sonydevworld/spresense-hw-design-files/GNSS/SPRESENSE_GNSS_antenna_char_en.pdf

## The characteristics of GNSS antenna

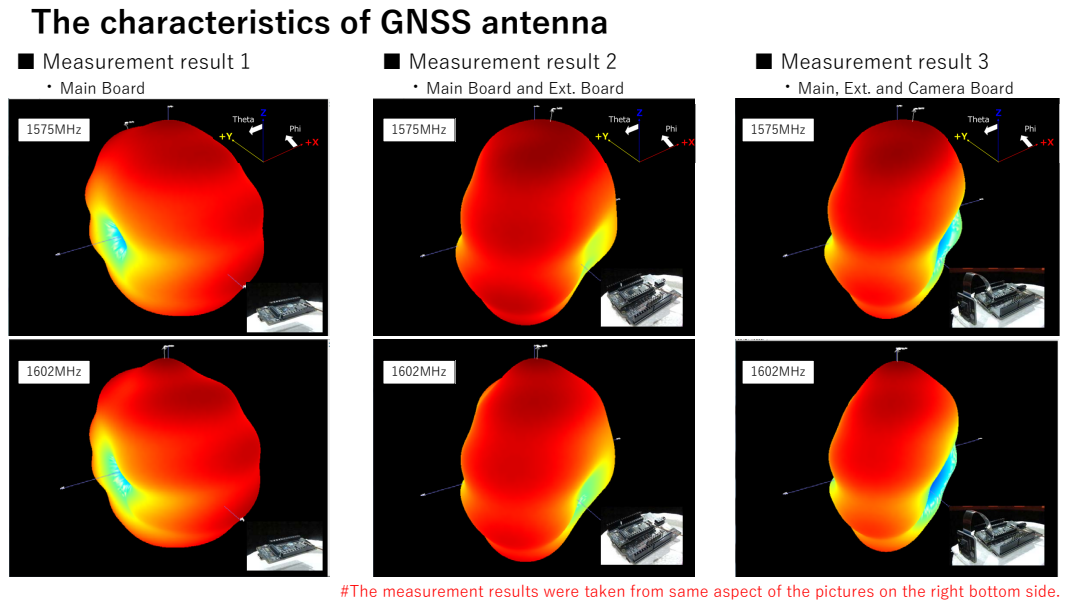
[picture p5: page 1]
1602MHz; 1575MHz; ■ Measurement result 1 ・Main Board

■ Measurement result 2
・Main Board and Ext. Board

■ Measurement result 3
・Main, Ext. and Camera Board

#The measurement results were taken from same aspect of the pictures on the right bottom side.

## Total gain in two-dimensional plane （Main board）

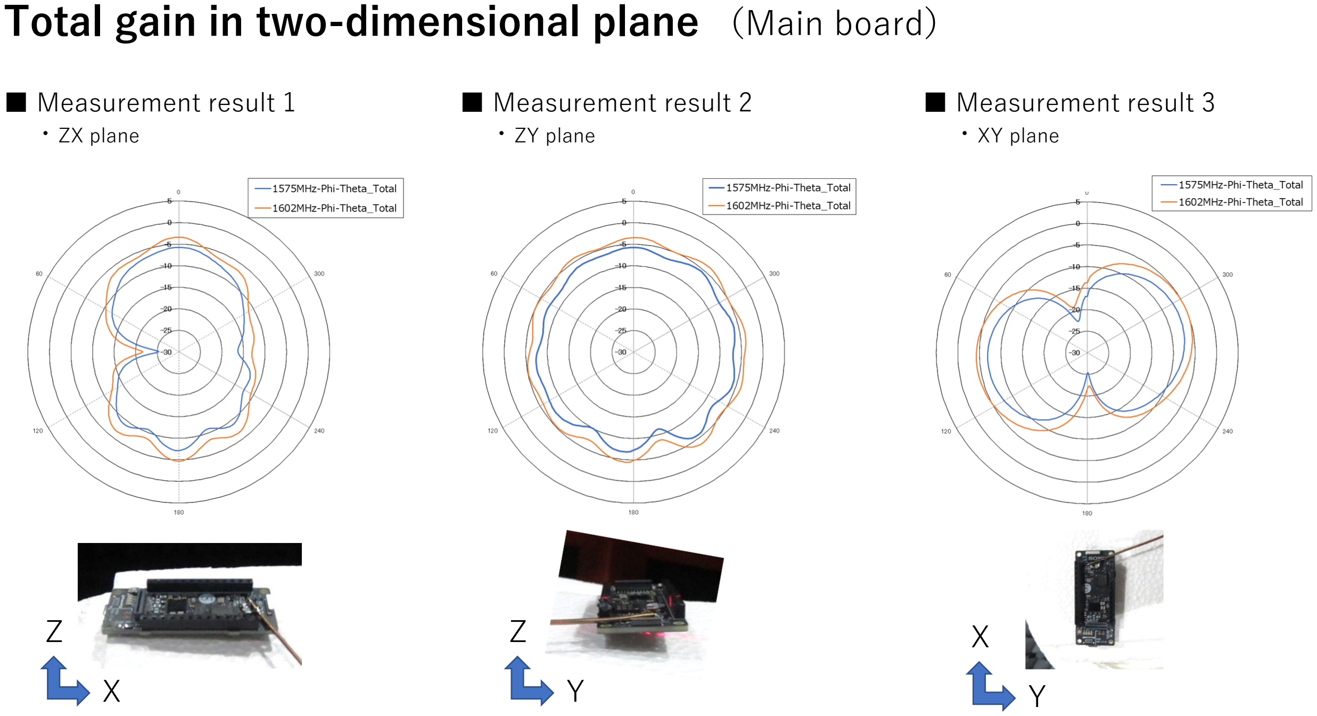
[picture p6: page 2]

■ Measurement result 1
・ZX plane

■ Measurement result 2
・ZY plane

■ Measurement result 3
・XY plane

X

Z

Y

Z

Y

X

## Total gain in two-dimensional plane （ Main board ＋Ext board）

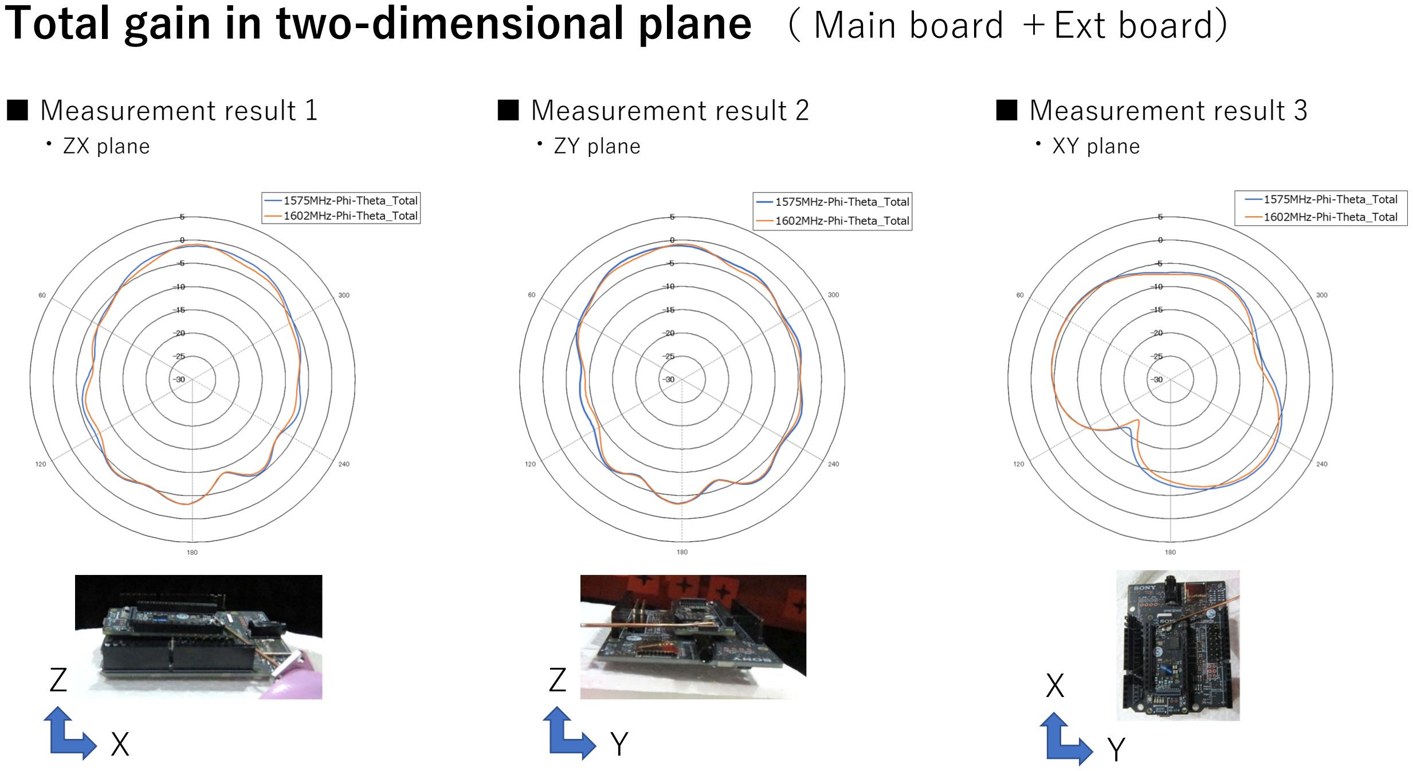
[picture p7: page 3]

X

Z

Y

Z

Y

X

■ Measurement result 1
・ZX plane

■ Measurement result 2
・ZY plane

■ Measurement result 3
・XY plane

## Total gain in two-dimensional plane （ Main＋Ext + Camera board）

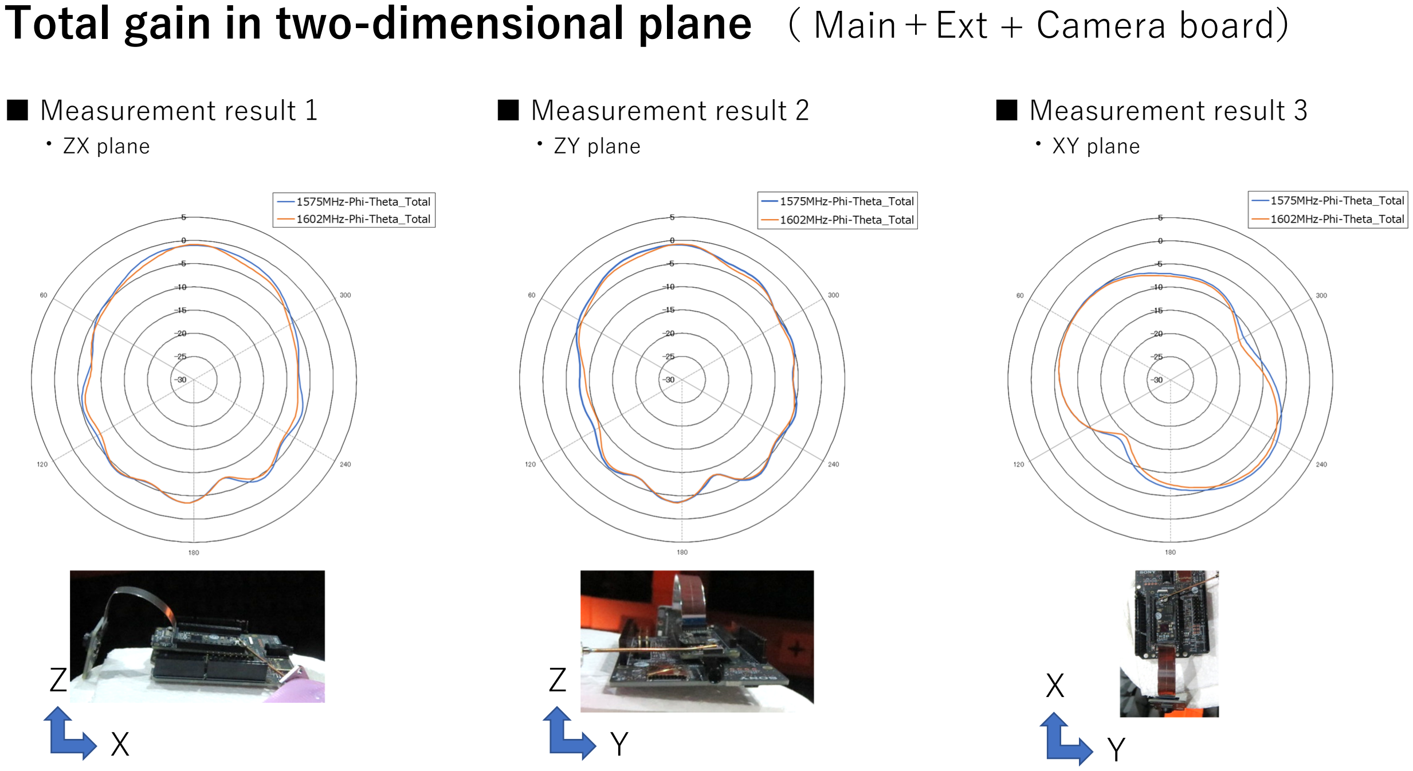
[picture p8: page 4]

X

Z

Y

Z

Y

X

■ Measurement result 1
・ZX plane

■ Measurement result 2
・ZY plane

■ Measurement result 3
・XY plane

Main Board
| 1575MHz | 1602MHz
Gain | Peak | Average of upper hemisphere(+Z) | Overall average | Peak | Average of upper hemisphere(+Z) | Overall average
[dBic] | -5.6 | -7.9 | -8.4 | -3.4 | -5.9 | -6.2
| 1575MHz | 1602MHz
Gain | Peak | Average of upper hemisphere(+Z) | Overall average | Peak | Average of upper hemisphere(+Z) | Overall average
[dBic] | -0.9 | -3.6 | -4.4 | -0.9 | -4.0 | -4.9
| 1575MHz | 1602MHz
Gain | Peak | Average of upper hemisphere(+Z) | Overall average | Peak | Average of upper hemisphere(+Z) | Overall average
[dBic] | -1.2 | -3.6 | -4.2 | -0.9 | -4.0 | -4.6

Main Board and Ext. Board

Main, Ext. and Camera Board

## The gain values of the antenna
