sonydevworld/spresense-hw-design-files/GNSS/SPRESENSE_GNSS_antenna_char_ja.pdf

## GNSSアンテナ特性

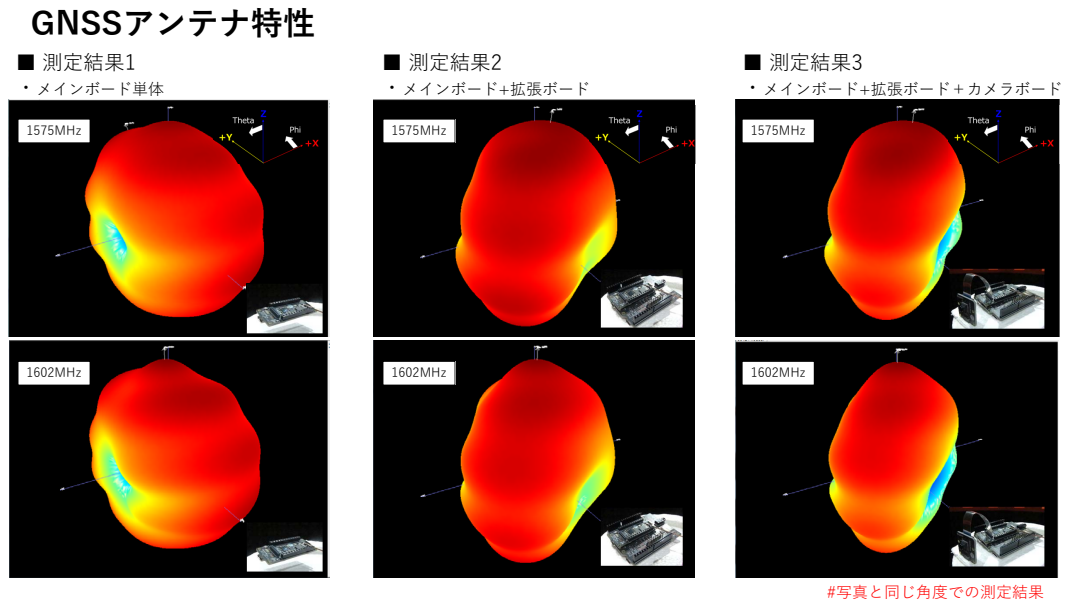
[picture p9: page 1]
#写真と同じ⾓度での測定結果; 1602MHz; 1575MHz; ■ 測定結果1 ・メインボード単体; ■ 測定結果2 ・メインボード+拡張ボード

■ 測定結果3
・メインボード+拡張ボード＋カメラボード

## 2D放射パターン Total Gain （メインボード単体）

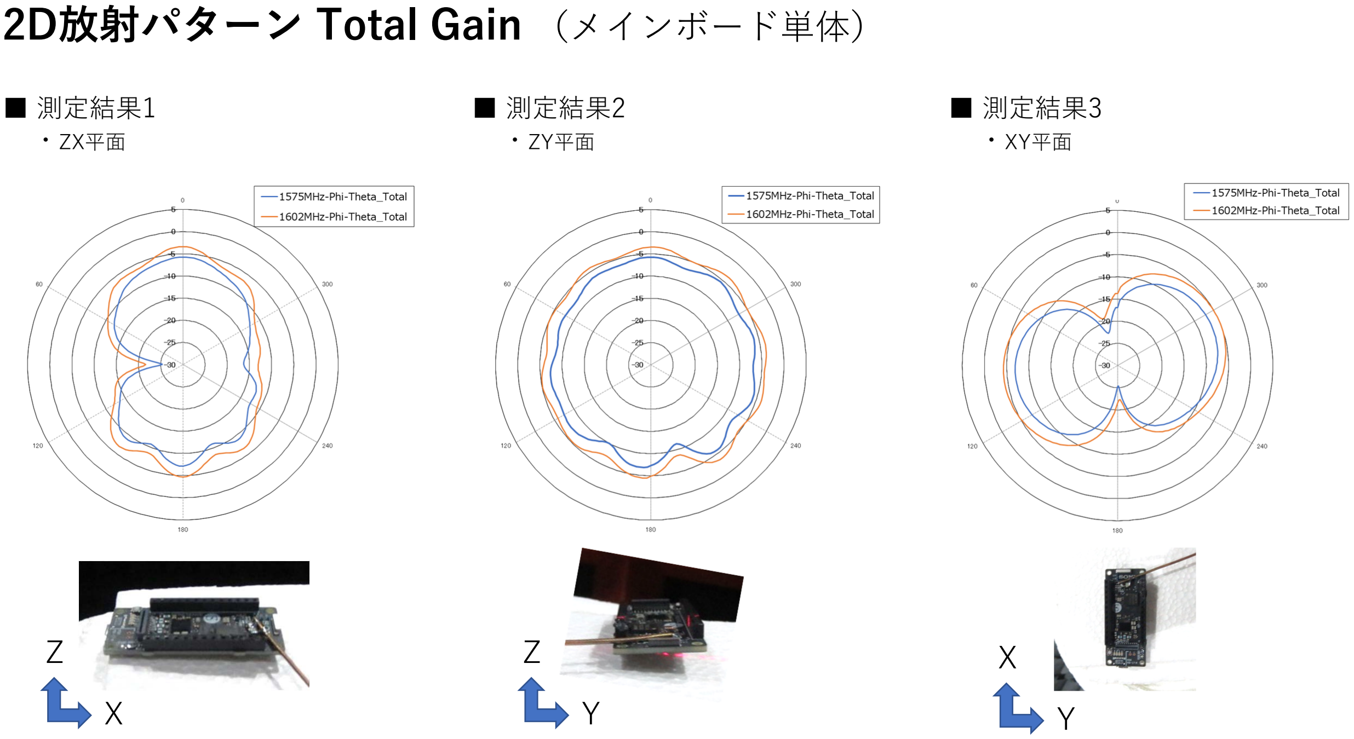
[picture p10: page 2]

■ 測定結果1
・ZX平⾯

■ 測定結果2
・ZY平⾯

■ 測定結果3
・XY平⾯

X

Z

Y

Z

Y

X

## 2D放射パターン Total Gain （メインボード＋拡張ボード）

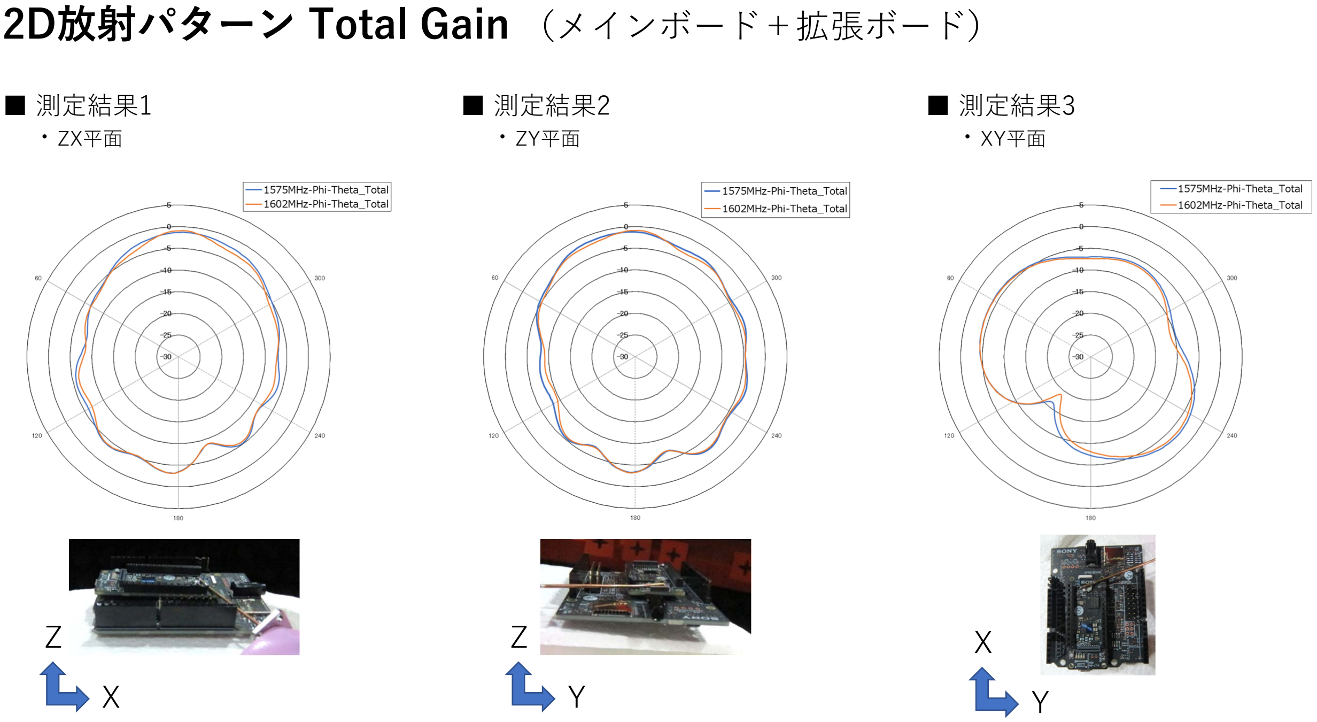
[picture p11: page 3]

■ 測定結果1
・ZX平⾯

■ 測定結果2
・ZY平⾯

■ 測定結果3
・XY平⾯

X

Z

Y

Z

Y

X

## 2D放射パターン Total Gain （メイン＋拡張＋カメラボード）

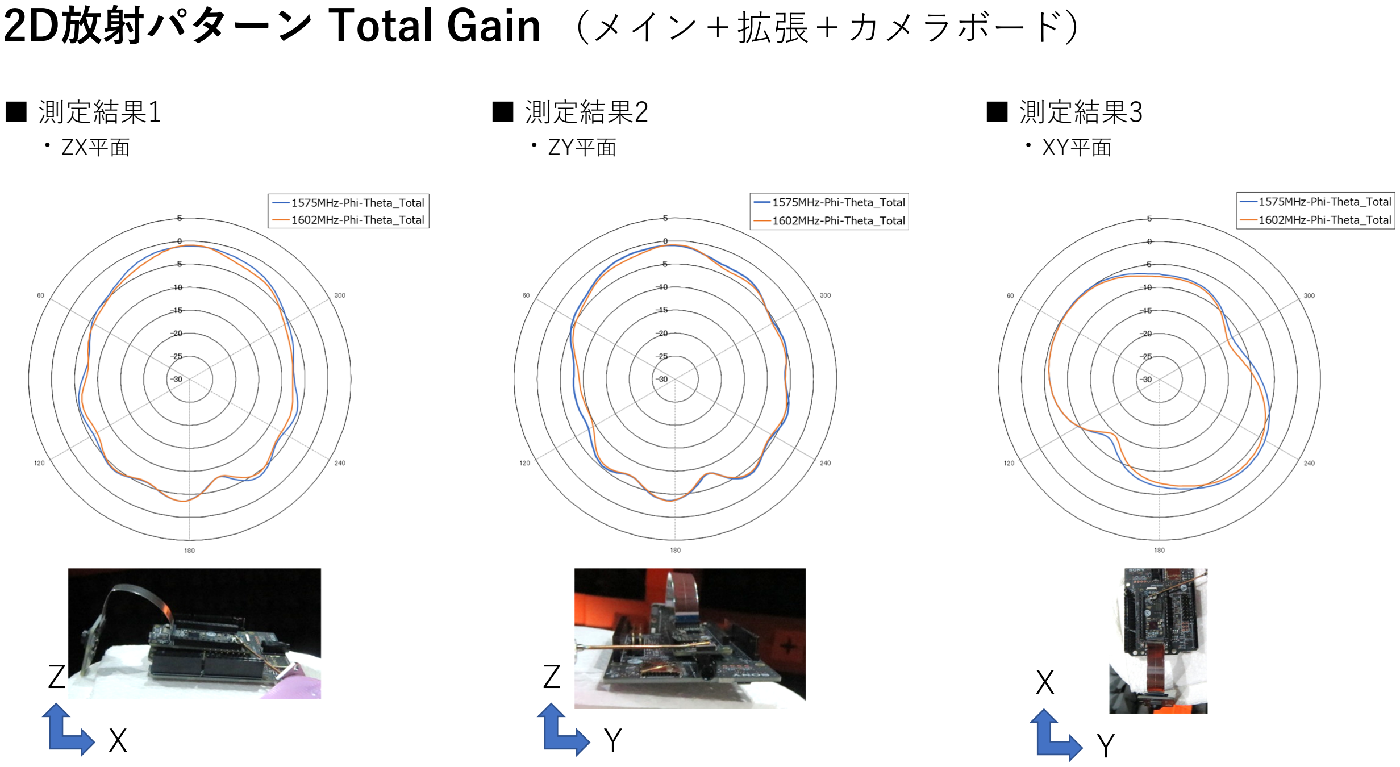
[picture p12: page 4]

■ 測定結果1
・ZX平⾯

■ 測定結果2
・ZY平⾯

■ 測定結果3
・XY平⾯

X

Z

Y

Z

Y

X

Main基板単体
| 1575MHz | 1602MHz
ゲイン | Peak | 上半球(+Z) 平均 | 全体平均 | Peak | 上半球(+Z) 平均 | 全体平均
[dBic] | -5.6 | -7.9 | -8.4 | -3.4 | -5.9 | -6.2
| 1575MHz | 1602MHz
ゲイン | Peak | 上半球(+Z) 平均 | 全体平均 | Peak | 上半球(+Z) 平均 | 全体平均
[dBic] | -0.9 | -3.6 | -4.4 | -0.9 | -4.0 | -4.9
| 1575MHz | 1602MHz
ゲイン | Peak | 上半球(+Z) 平均 | 全体平均 | Peak | 上半球(+Z) 平均 | 全体平均
[dBic] | -1.2 | -3.6 | -4.2 | -0.9 | -4.0 | -4.6

Main基板+Ext基板

Main基板+Ext基板＋Camera基板

## アンテナゲイン
