sonydevworld/spresense-hw-design-files/CXD5602PWBCAM1/BOM/CXD5602PWBCAM1_BOM_list_en.pdf

CXD5602PWBCAM1 BOM List | Sony Semiconductor Solutions
Qty | Ref | Name | Model | Vender
5 | C1,C2,C3,C4,C5 | Ceramic capacitor 1uF (6.3V X5R 0603)
1 | C8 | Ceramic capacitor 10uF (6.3V X5R 1005)
1 | C7 | Ceramic capacitor 22pF （50V C0G 0603)
1 | C6 | Ceramic capacitor 4.7uF (6.3V X5R 1005)
1 | R3 | Chip resistor 47Ω (1/20W 0603 5%)
2 | R1,R2 | Chip ferrite bead (0603) | BLM03BD121SN | Murata
1 | FB1 | Chip resistor 0Ω (0603)
1 | L1 | Chip inductor 2.2uH (2016) | DFE201610E-2R2M=P2 | Murata
1 | CN1 | FFC/FPC connector ZIF (20P) | 086262020340846+ | Kyocera
1 | CN2 | FFC/FPC connector ZIF (25P) | FH35C-25S-0.3SHW(42) | Hirose Electric
1 | IC3 | Switching regurator | RP507K001B-TR | Ricoh Electronic Devices
1 | IC2 | LDO voltage regulator (1.8V) | TCR3DF18 | Toshiba Device
1 | IC1 | LDO voltage regulator (2.7V) | TCR3DF27 | Toshiba Device
1 | | Camera Module | G8P5-5604FF V2 | KingCome
