sonydevworld/spresense-hw-design-files/CXD5602PWBCAM1/BOM/CXD5602PWBCAM1_BOM_list_ja.pdf

CXD5602PWBCAM1 BOM List | Sony Semiconductor Solutions
Qty | Ref | 名称 | Model | ベンダー
5 | C1,C2,C3,C4,C5 | セラミックコンデンサ 1uF (6.3V X5R 0603)
1 | C8 | セラミックコンデンサ 10uF (6.3V X5R 1005)
1 | C7 | セラミツクコンデンサ 22pF （50V C0G 0603)
1 | C6 | セラミックコンデンサ 4.7uF (6.3V X5R 0603)
1 | R3 | チップ抵抗 47Ω (1/20W 0603 5%)
2 | R1,R2 | チップフェライトビーズ (0603) | BLM03BD121SN | 村田製作所
1 | FB1 | チップ抵抗 0Ω (0603)
1 | L1 | チップインダクタ 2.2uH (2016) | DFE201610E-2R2M=P2 | 村田製作所
1 | CN1 | FFC/FPC コネクタ ZIF (20極) | 086262020340846+ | 京セラ
1 | CN2 | FFC/FPC コネクタ ZIF (25極) | FH35C-25S-0.3SHW(42) | ヒロセ電機
1 | IC3 | スイッチングレギュレータ | RP507K001B-TR | リコー電子デバイス
1 | IC2 | LDO電圧レギュレータ (1.8V) | TCR3DF18 | 東芝デバイス
1 | IC1 | LDO電圧レギュレータ (2.7V) | TCR3DF27 | 東芝デバイス
1 | | カメラモジュール | G8P5-5604FF V2 | KingCome
