sonydevworld/spresense-hw-design-files/Case/LTE-Board-Case-Sample/stl/LTE-Board-Case-Sample_bottom.stl

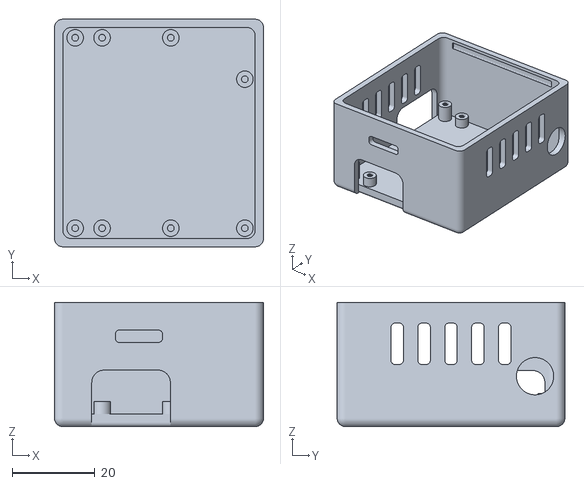
[picture p32: CAD file, 2021-03-09]
Case/LTE-Board-Case-Sample/stl/LTE-Board-Case-Sample_bottom.stl
50.5 x 55.0 x 30.0
