sonydevworld/spresense-hw-design-files/CXD5602PWBCAM1/dxf/CXD5602PWBCAM1_side_a.dxf

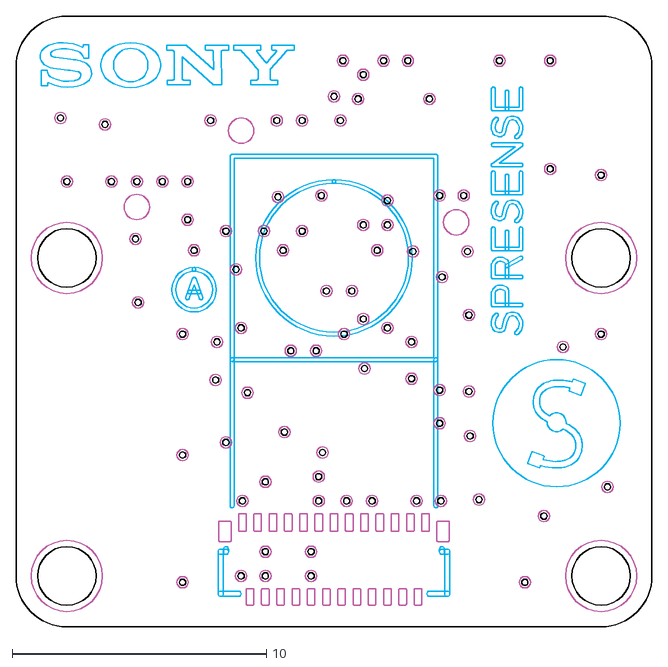
[picture p33: CAD file, 2019-08-30]
CXD5602PWBCAM1/dxf/CXD5602PWBCAM1_side_a.dxf
25.0 x 24.0
