sonydevworld/spresense-hw-design-files/CXD5602PWBCAM2/dxf/CXD5602PWBCAM2_side_b.dxf

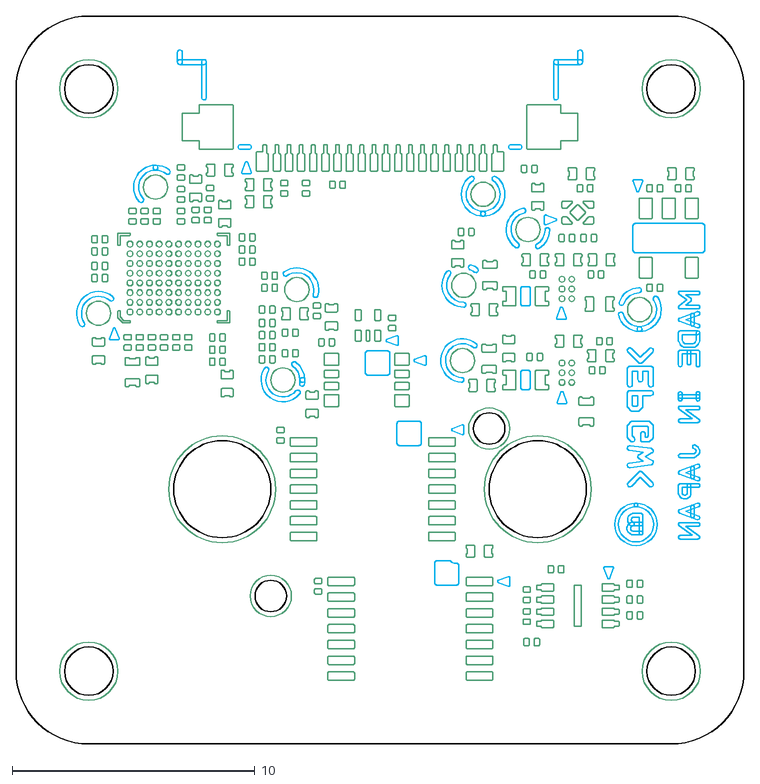
[picture p34: CAD file, 2022-03-31]
CXD5602PWBCAM2/dxf/CXD5602PWBCAM2_side_b.dxf
30.0 x 30.0
