sonydevworld/spresense-hw-design-files/CXD5602PWBEXT1/dxf/CXD5602PWBEXT1_side_b.dxf

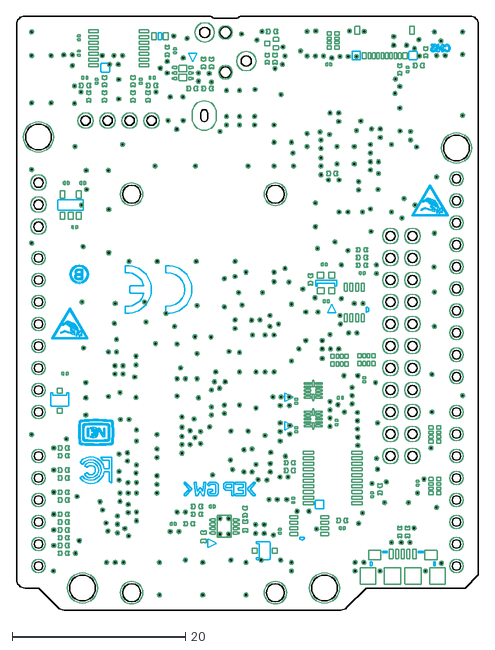
[picture p35: CAD file, 2019-08-30]
CXD5602PWBEXT1/dxf/CXD5602PWBEXT1_side_b.dxf
53.3 x 68.6
