sonydevworld/spresense-hw-design-files/CXD5602PWBGNSS1/dxf/CXD5602PWBGNSS1_side_a.dxf

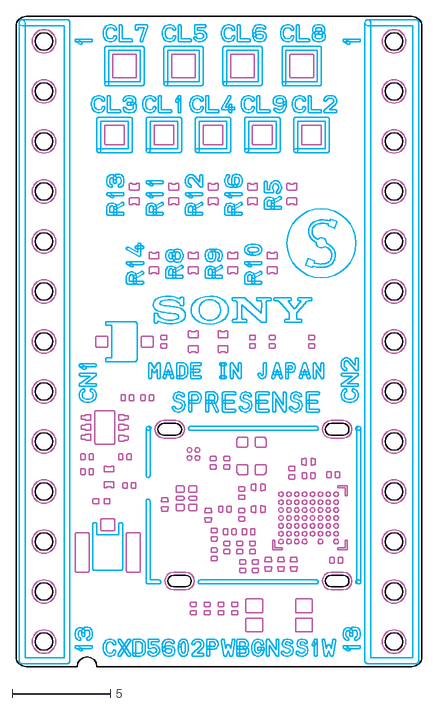
[picture p36: CAD file, 2023-07-11]
CXD5602PWBGNSS1/dxf/CXD5602PWBGNSS1_side_a.dxf
20.6 x 33.0
