sonydevworld/spresense-hw-design-files/CXD5602PWBLM1/dxf/CXD5602PWBLM1_side_b.dxf

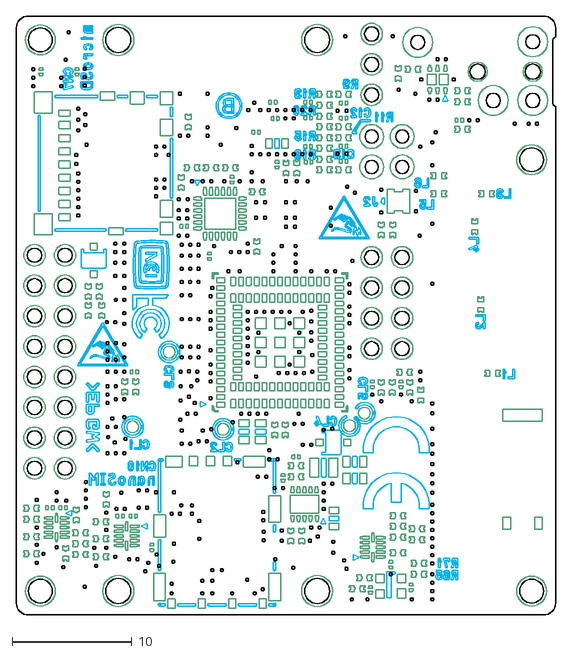
[picture p37: CAD file, 2019-12-17]
CXD5602PWBLM1/dxf/CXD5602PWBLM1_side_b.dxf
45.0 x 50.0
