sonydevworld/spresense-hw-design-files/CXD5602PWBLM2/dxf/CXD5602PWBLM2_side_b.dxf

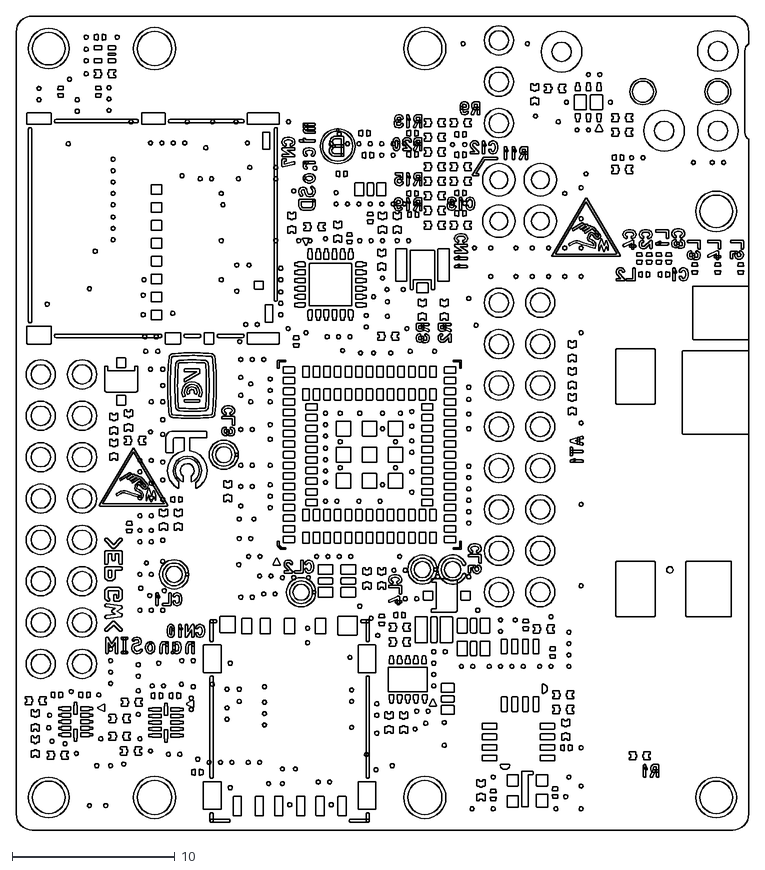
[picture p38: CAD file, 2024-06-07]
CXD5602PWBLM2/dxf/CXD5602PWBLM2_side_b.dxf
45.0 x 50.0
