sonydevworld/spresense-hw-design-files/CXD5602PWBEXT1/schematics/CXD5602PWBEXT1_schematics_en.pdf

# Digital I/F

A

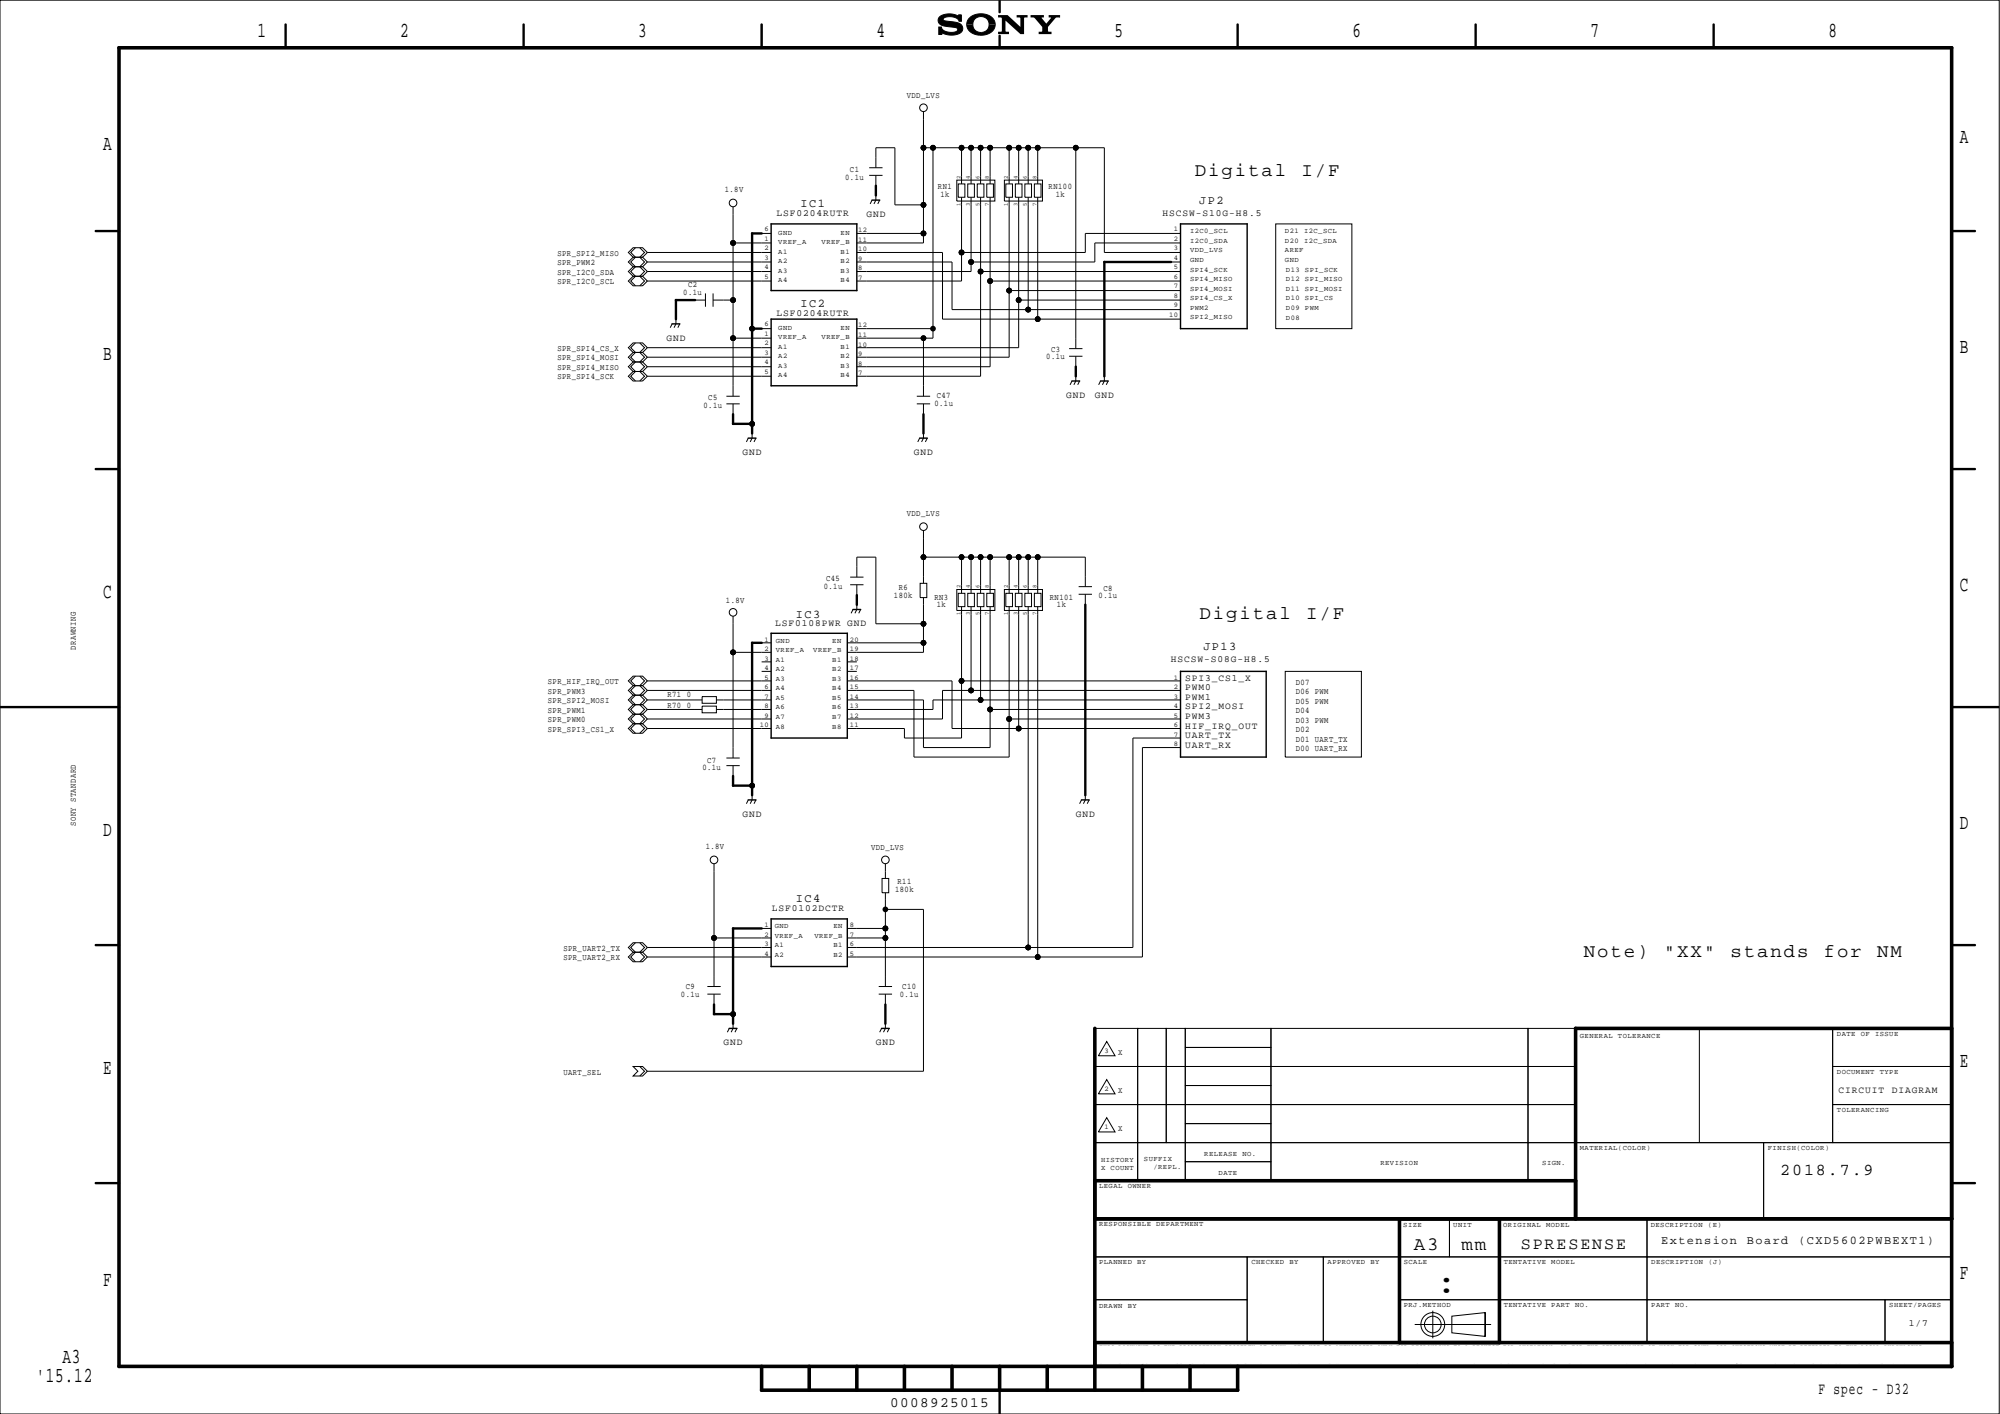
[picture p61: page 1]

Note) "XX" stands for NM

Purchase recyled resins and wire rods only from the business partners that Sony approves as Green Partners.
再生樹脂・被覆電線はグリ－ンパ－トナ－認定取引先から調達すること。

THIS DOCUMENT IS THE PROPRIETARY PROPERTY OF SONY. ITS USE IS AUTHORIZED ONLY FOR RESPONDING TO A REQUEST FOR QUOTATION, OR FOR THE PERFORMANCE OF WORK FOR SONY. ALL QUESTIONS MUST BE REFERRED TO THE LOCAL PURCHASING
DEPARTMENT OF SONY. THIS PART SHOULD NOT CONTAIN ANY SUBSTANCES WHICH ARE SPECIFIED IN SS-00259-01. THE REPRODUCTION, DISTRIBUTION AND UTILIZATION OF THIS DOCUMENT AS WELL AS THE COMMUNICATION OF ITS CONTENTS TO
OTHERS WITHOUT EXPRESS AUTHORIZATION IS PROHIBITED. OFFENDERS WILL BE HELD LIABLE FOR THE PAYMENT OF DAMAGES. ALL RIGHTS RESERVED IN THE EVENT OF THE GRANT OF A PATENT,UTILITY MODEL OR DESIGN. COPYRIGHT RESERVED.

## IC5 PST8416UL

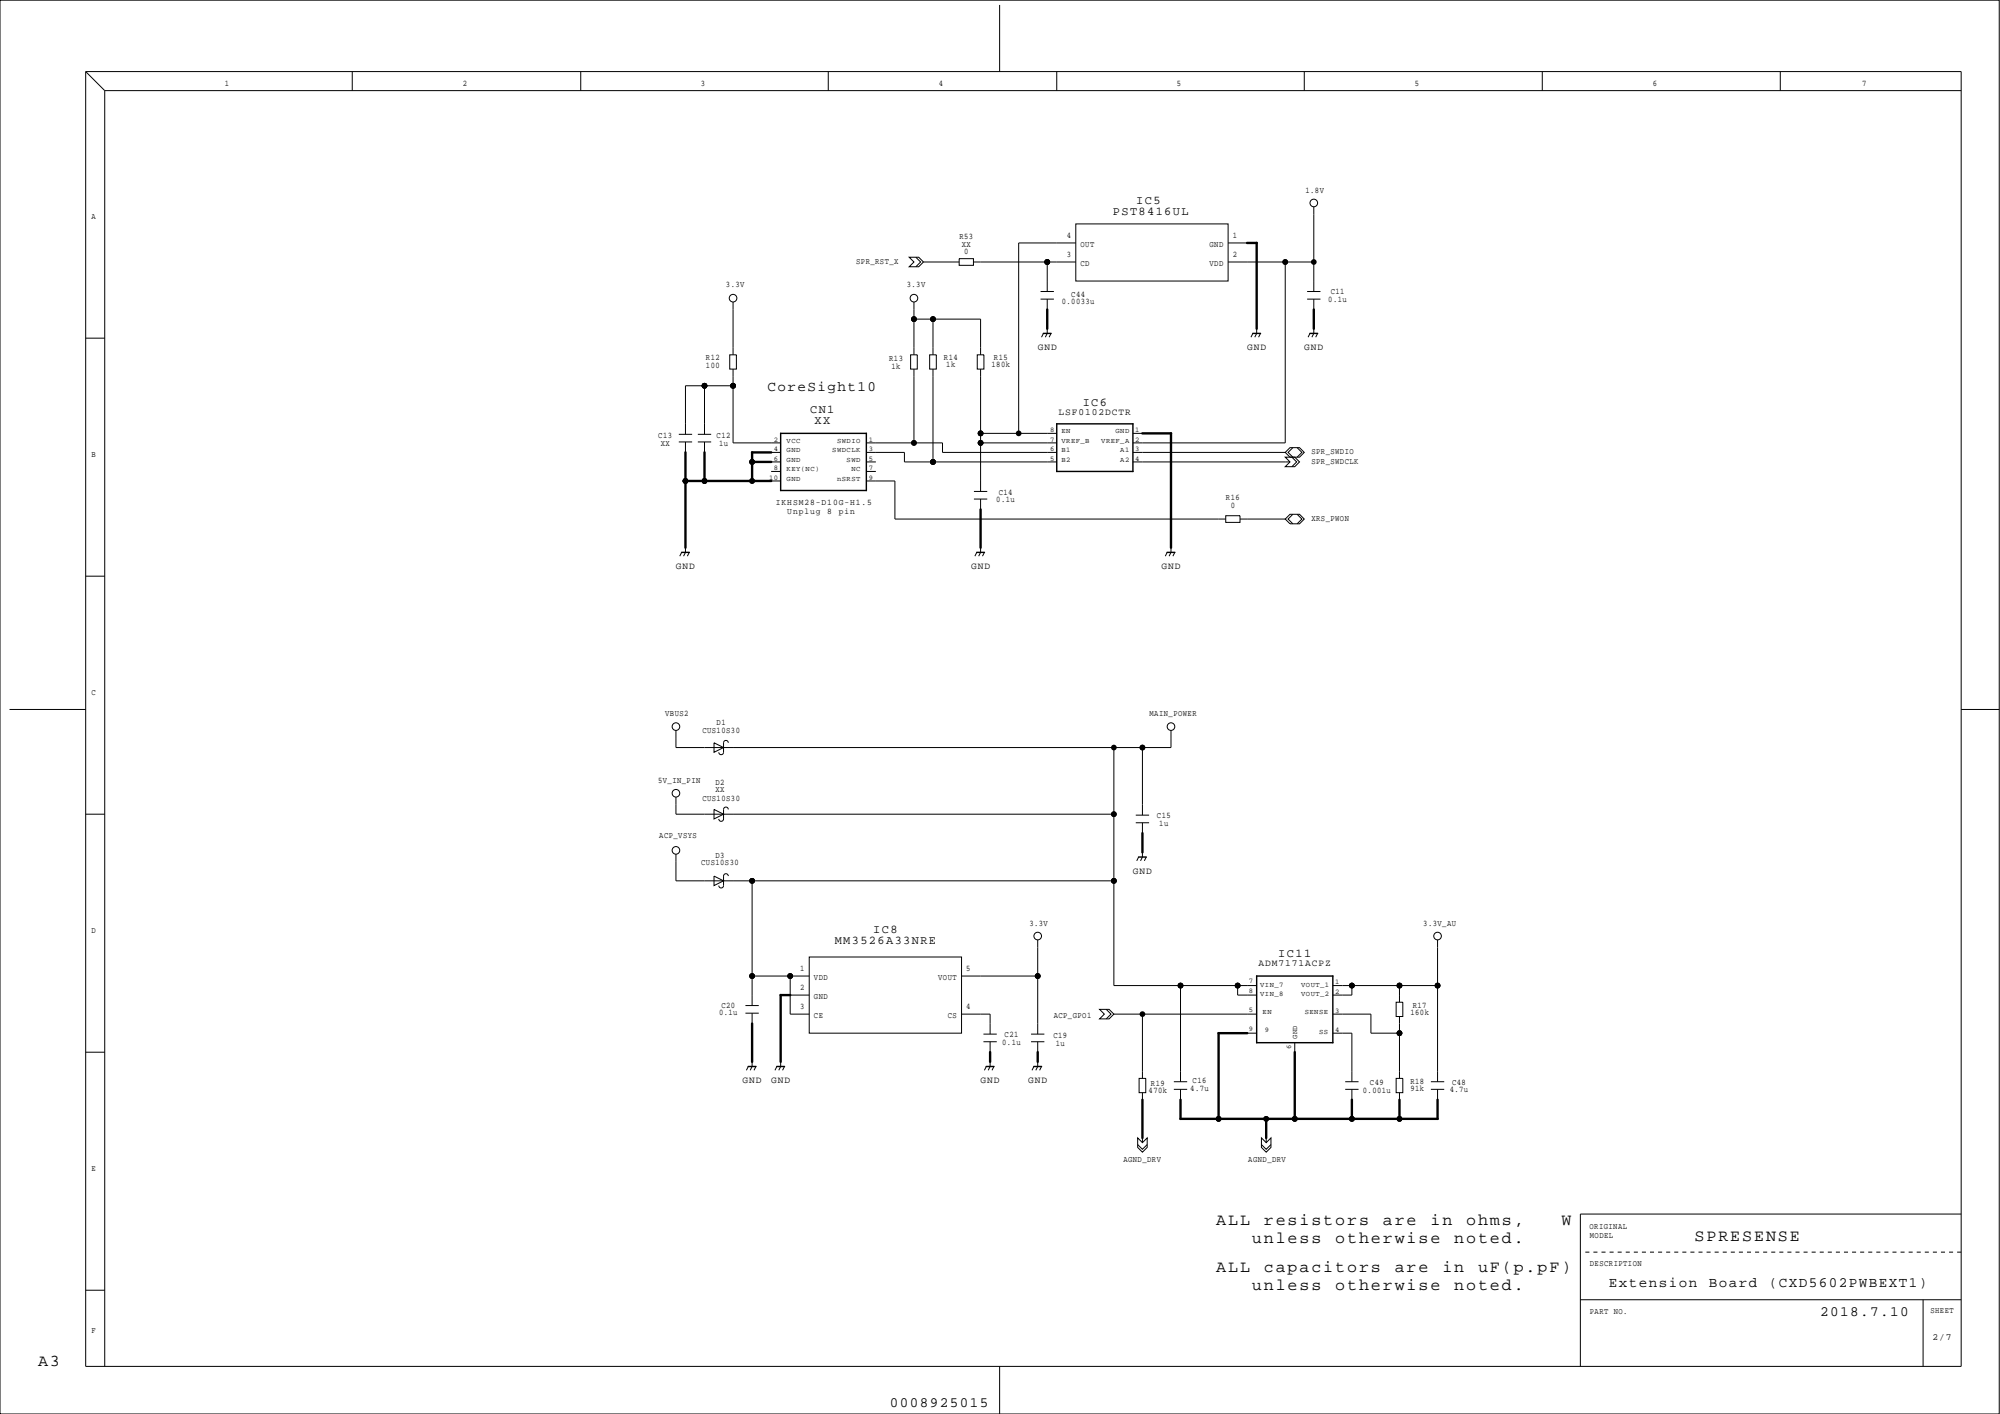
[picture p62: page 2]

unless otherwise noted.
ALL capacitors are in uF(p.pF)

THIS DOCUMENT IS THE PROPRIETARY PROPERTY OF SONY. ITS USE IS AUTHORIZED ONLY FOR RESPONDING TO A REQUEST FOR QUOTATION, OR FOR THE PERFORMANCE OF WORK FOR SONY. ALL QUESTIONS MUST BE
REFERRED TO THE LOCAL PURCHASING DEPARTMENT OF SONY. THE REPRODUCTION, DISTRIBUTION AND UTILIZATION OF THIS DOCUMENT AS WELL AS THE COMMUNICATION OF ITS CONTENTS TO OTHERS WITHOUT EXPRESS
AUTHORIZATION IS PROHIBITED. OFFENDERS WILL BE HELD LIABLE FOR THE PAYMENT OF DAMAGES. ALL RIGHTS RESERVED IN THE EVENT OF THE GRANT OF A PATENT, UTILITY MODEL OR DESIGN. COPYRIGHT RESERVED.

CN3

# BtoB CN

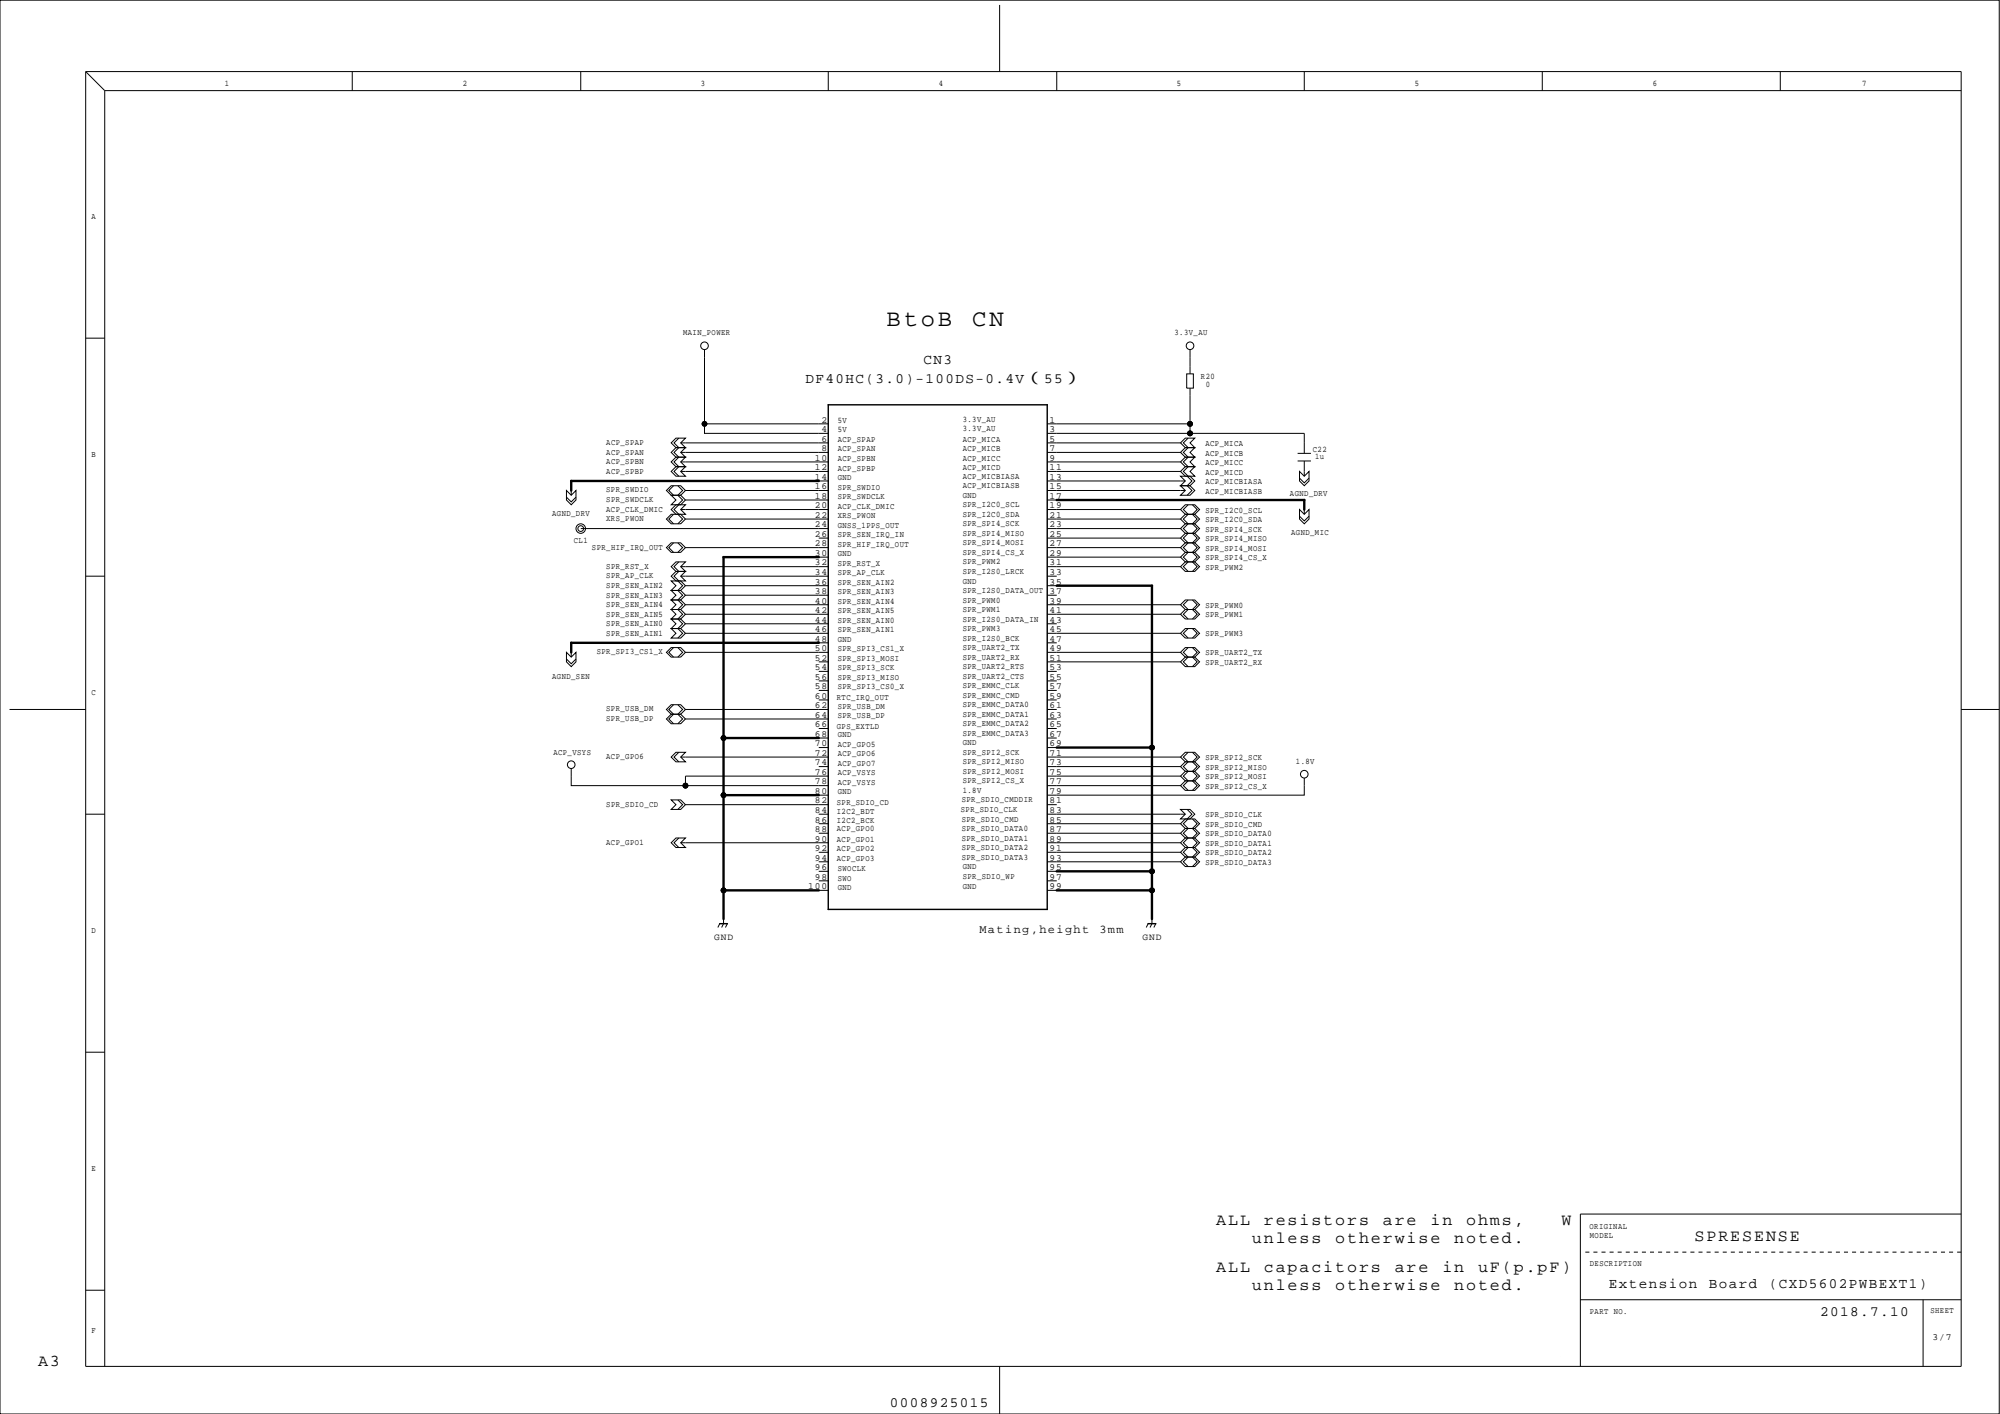
[picture p63: page 3]
ORIGINAL MODEL; DESCRIPTION; SPRESENSE; Extension Board (CXD5602PWBEXT1); ALL resistors are in ohms,; EXT1-00.cir/003.sht; ACP_MICB; SPR_SEN_AIN1; SPR_SEN_AIN0; SPR_SEN_AIN5; SPR_SEN_AIN4; SPR_SEN_AIN3; SPR_SEN_AIN2; SPR_SWDCLK; ACP_MICC ACP_MICD; ACP_MICA; ACP_SPBP; ACP_MICBIASB; SPR_RST_X SPR_AP_CLK; ACP_SPBN; ACP_SPAN; ACP_SPAP; AGND_DRV; AGND_MIC; ACP_CLK_DMIC; AGND_SEN; ACP_MICBIASA; ACP_GPO1; ACP_GPO6; SPR_USB_DP; SPR_USB_DM; SPR_SDIO_DATA3; SPR_SPI3_CS1_X; SPR_HIF_IRQ_OUT; XRS_PWON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

unless otherwise noted.
ALL capacitors are in uF(p.pF)

# Power I/F

# I/O Power SW JP

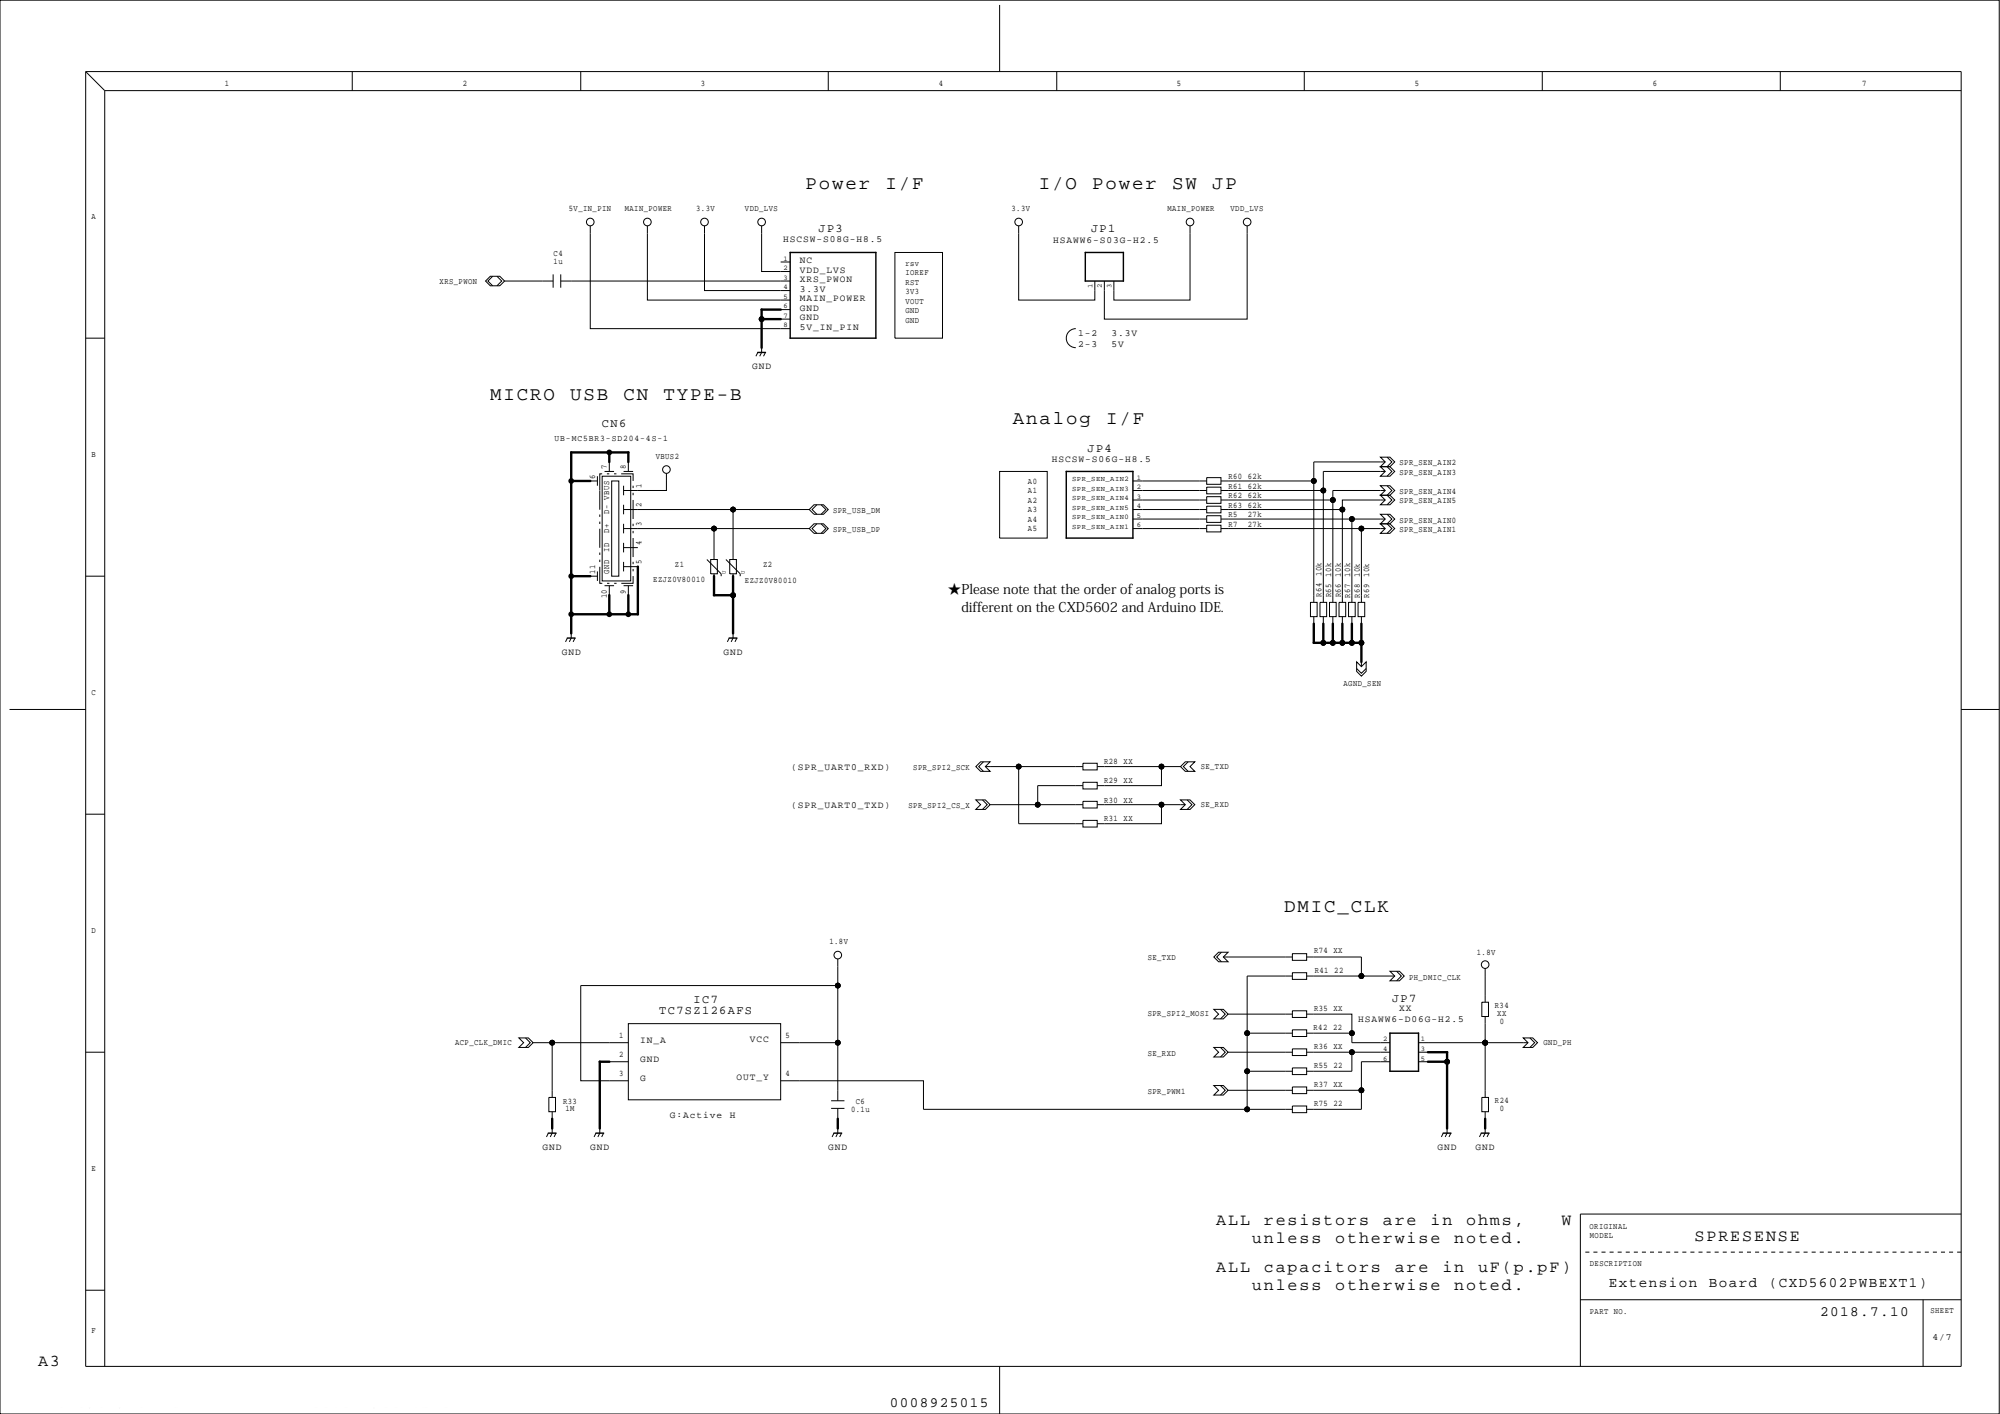
[picture p64: page 4]

MICRO USB CN TYPE-B

★Please note that the order of analog ports is
different on the CXD5602 and Arduino IDE.

unless otherwise noted.
ALL capacitors are in uF(p.pF)

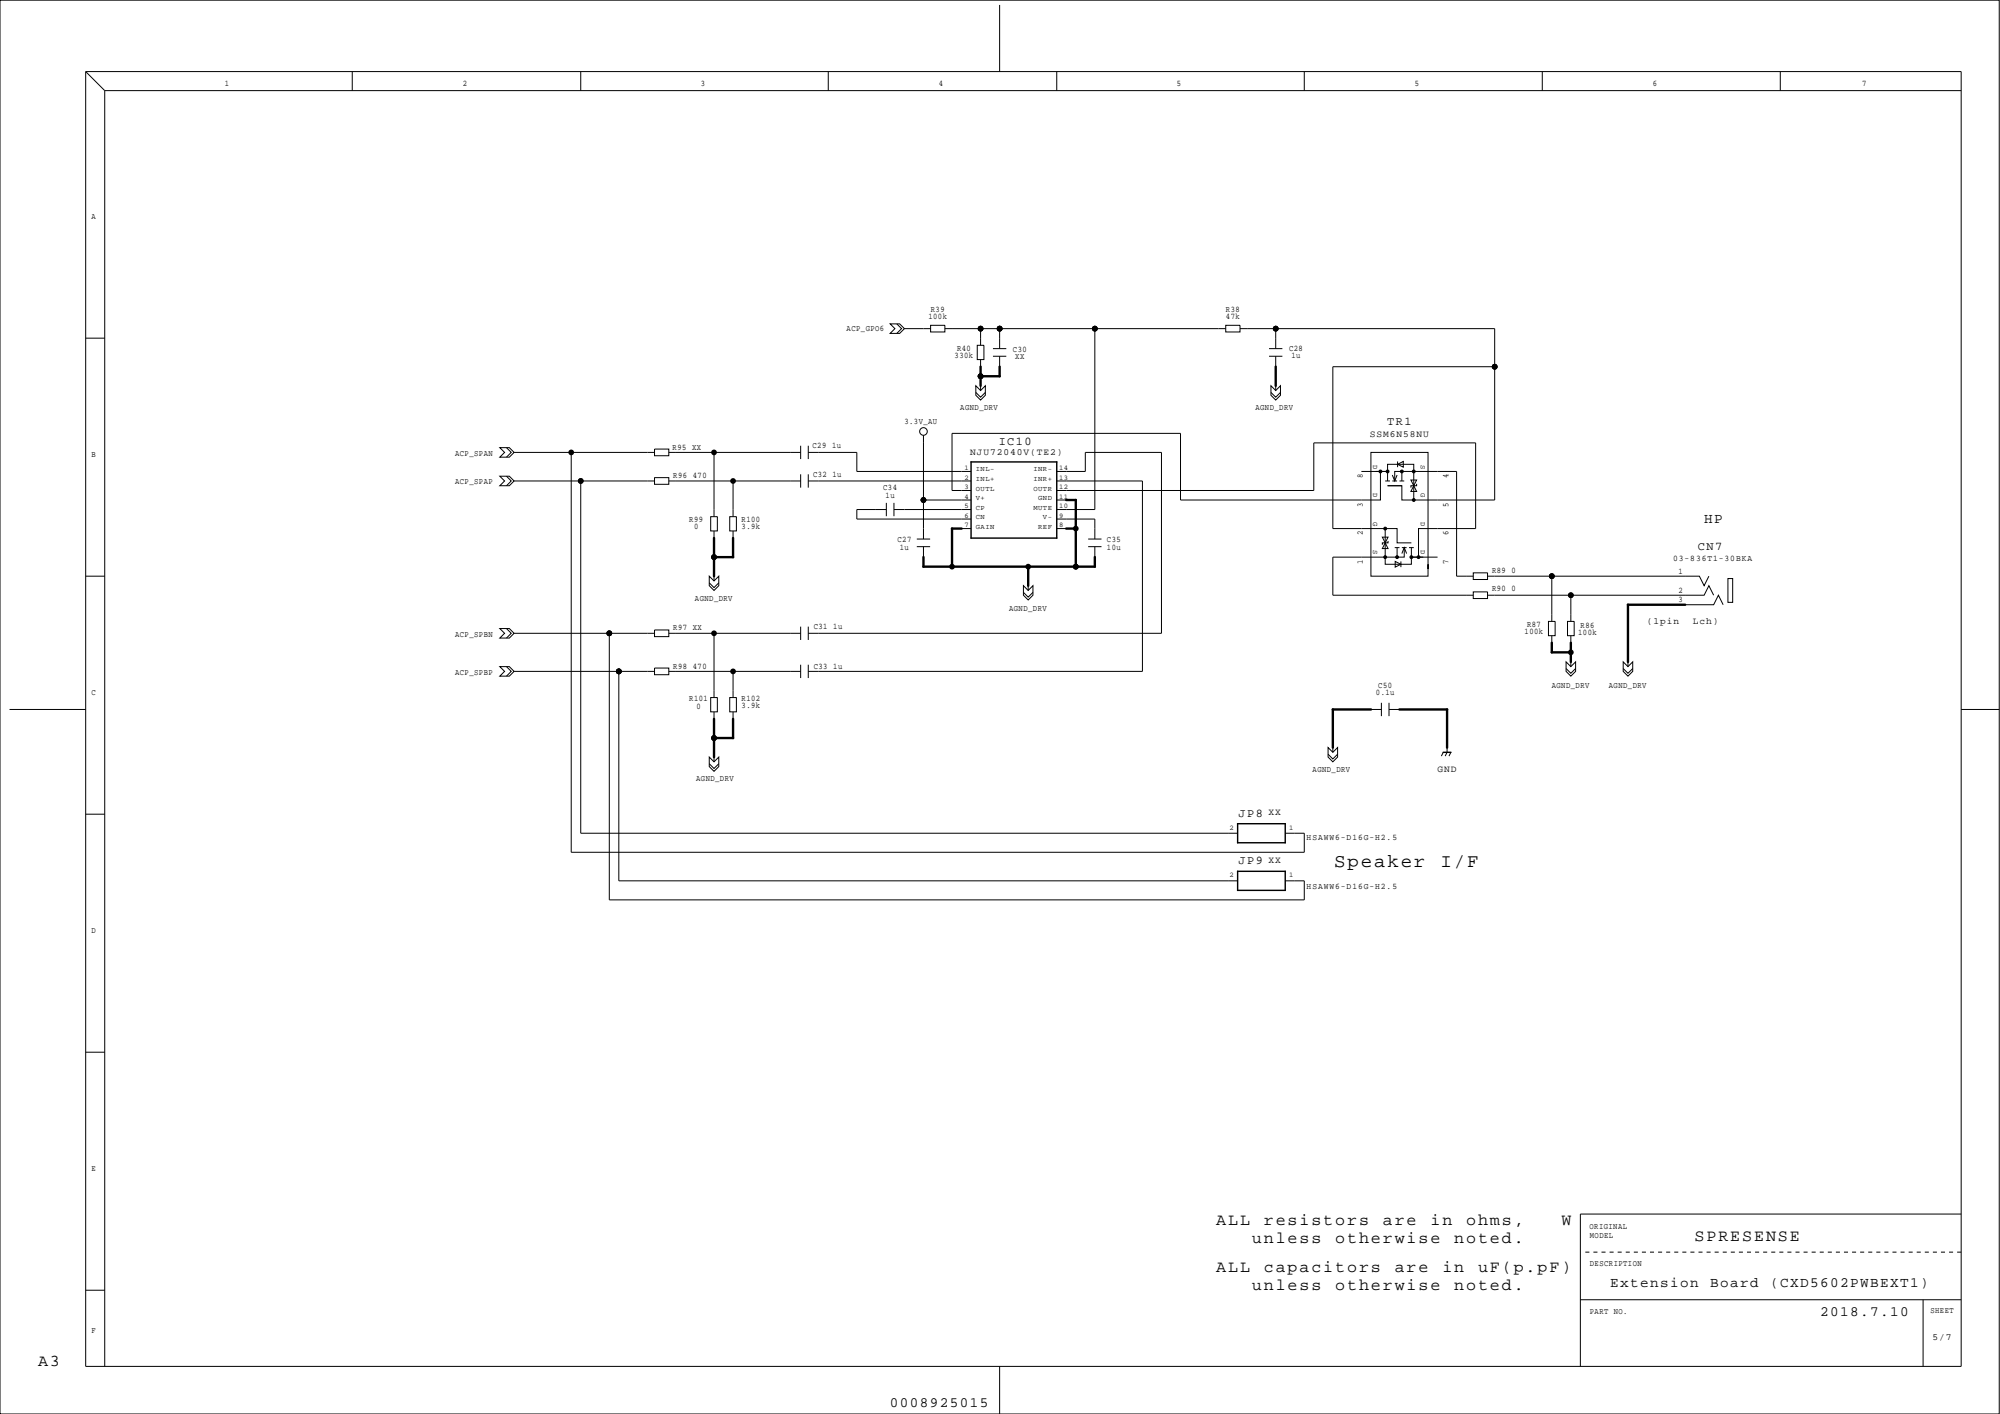
[picture p65: page 5]

unless otherwise noted.
ALL capacitors are in uF(p.pF)

# microSD

CN4

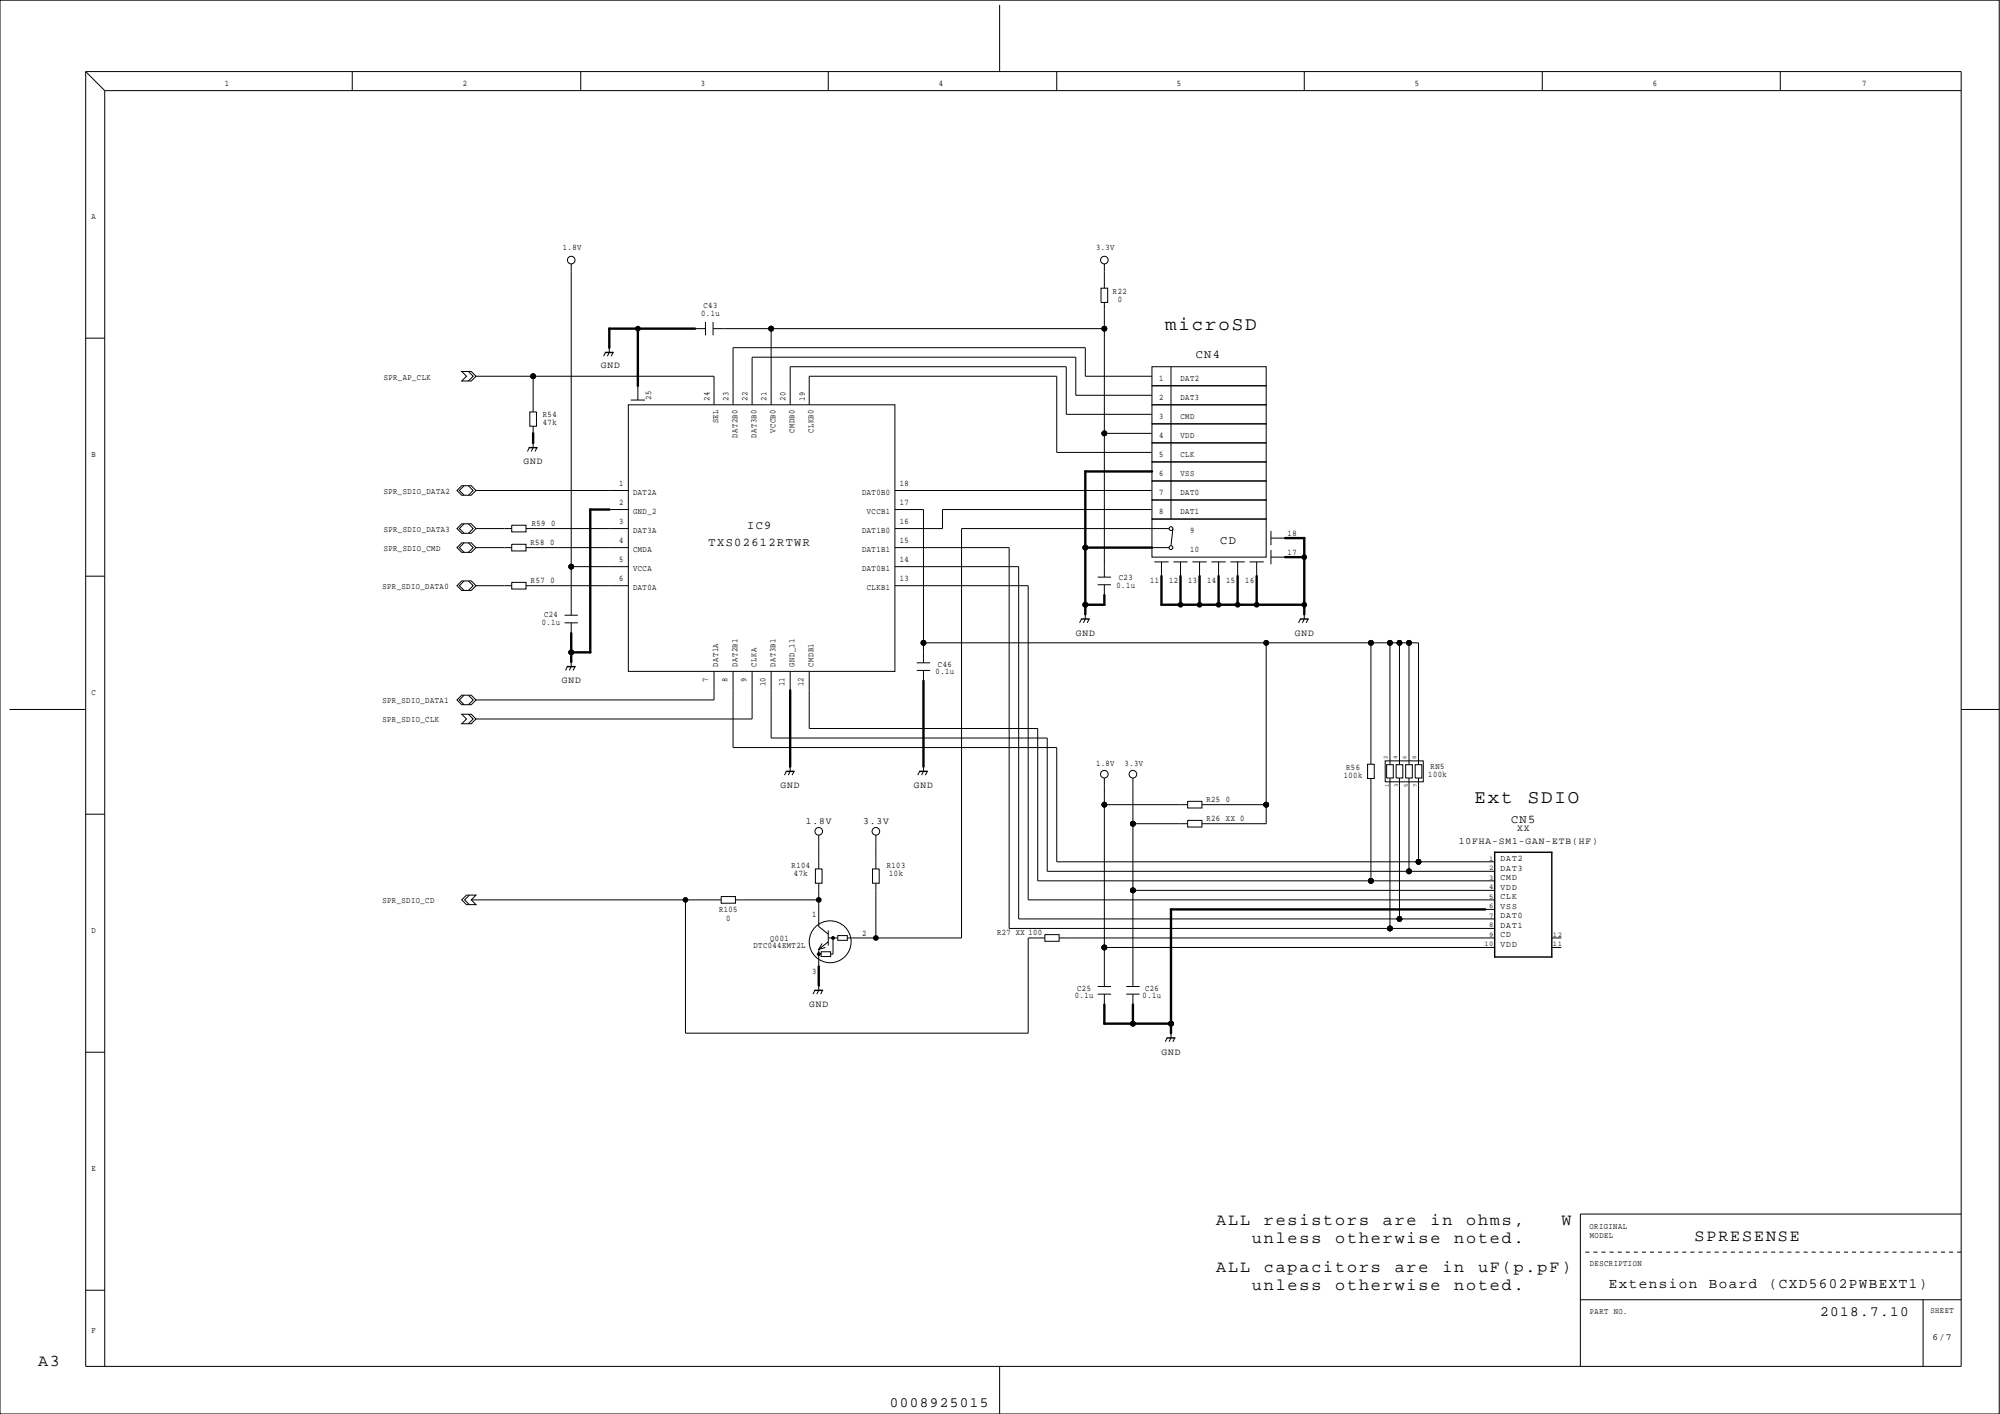
[picture p66: page 6]

1 | DAT2

2 | DAT3

4 | VDD

5 | CLK

6 | VSS

7 | DAT0

8 | DAT1

unless otherwise noted.
ALL capacitors are in uF(p.pF)

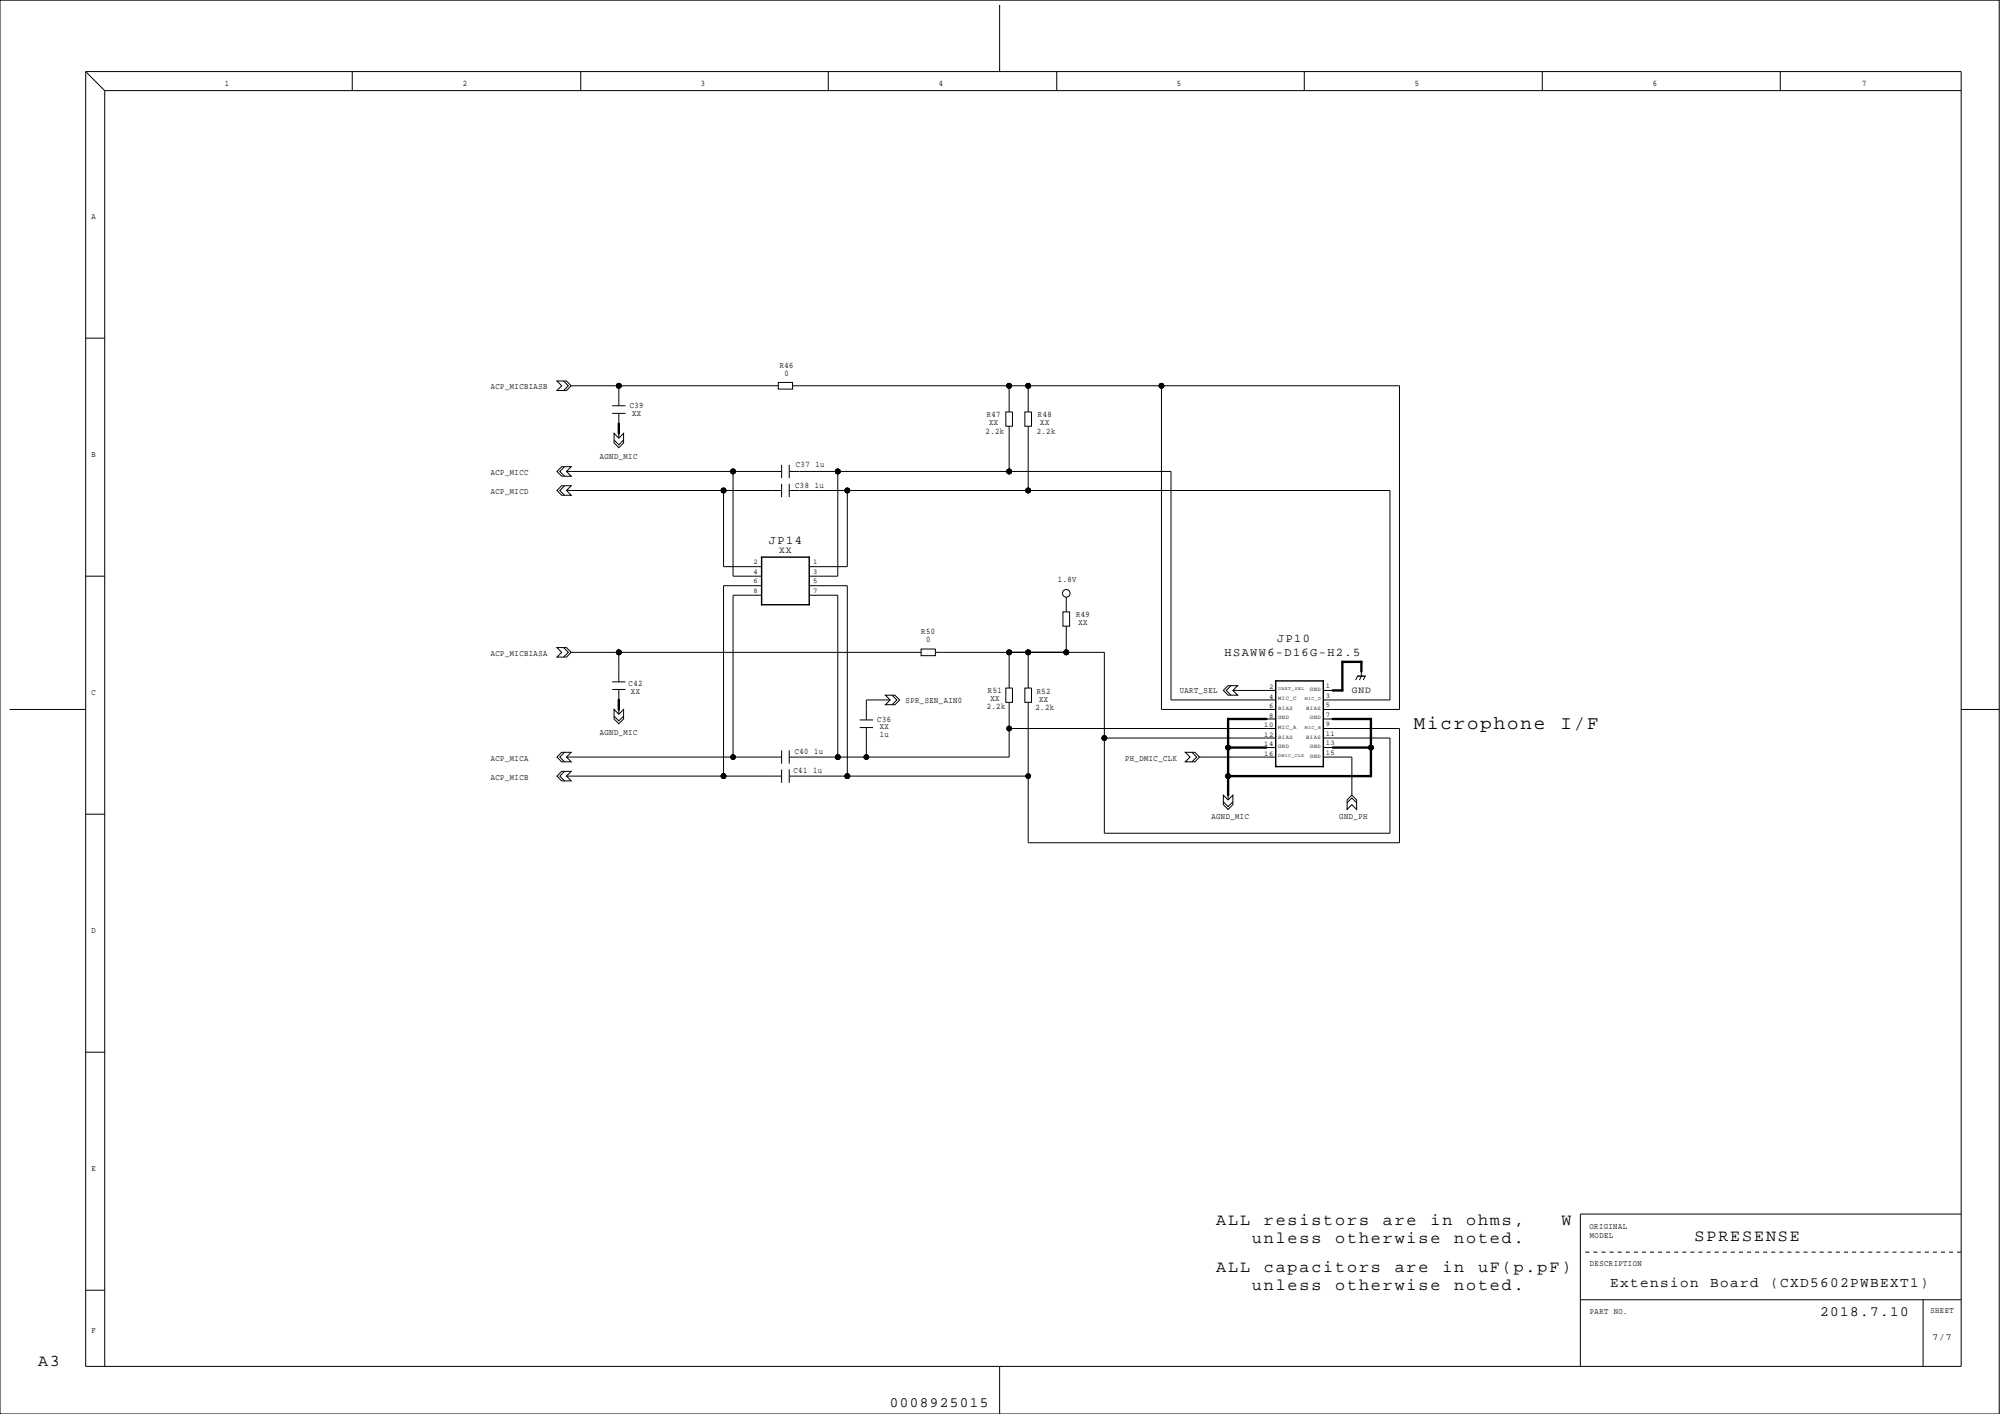
[picture p67: page 7]

unless otherwise noted.
ALL capacitors are in uF(p.pF)
