sonydevworld/spresense-hw-design-files/CXD5602PWBLM1/schematics/CXD5602PWBLM1_schematics.pdf

# I/O Power SW JP

# MICRO USB CN TYPE-B


Note) "XX" stands for NM

CN3

# BtoB CN

SHEET; ORIGINAL; MODEL; DESCRIPTION; SPRESENSE; LTE Board (CXD5602PWBLM1); ALL resistors are in ohms,; ACP_MICB; SPR_SWDCLK; ACP_MICA; SPR_SDIO_CD; SPR_GPS_EXTLD; SPR_RTC_IRQ_OUT; SPR_AP_CLK; SPR_UART2_CTS; SPR_UART2_RTS; ACP_MICC; SPR_SEN_AIN2; SPR_SDIO_CMDDIR; SPR_UART2_RX; SPR_UART2_TX; SPR_SEN_AIN0 SPR_SEN_AIN1; SPR_SDIO_WP; ACP_GPO2; ACP_CLK_DMIC; ACP_MICBIASA; SPR_SWO; ACP_GPO3; ACP_GPO1; ACP_GPO6; SPR_SDIO_CLK; ACP_SPBP; ACP_MICBIASB; AGND_MIC; AGND_DRV; ACP_GPO0; ACP_SPAP ACP_SPAN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

unless otherwise noted.
ALL capacitors are in uF(p.pF)

# Microphone I/F

CN6


unless otherwise noted.
ALL capacitors are in uF(p.pF)

# CLE9108-2A08E


1 | DAT2

2 | DAT3

4 | VDD

5 | CLK

6 | VSS

7 | DAT0

8 | DAT1

unless otherwise noted.
ALL capacitors are in uF(p.pF)

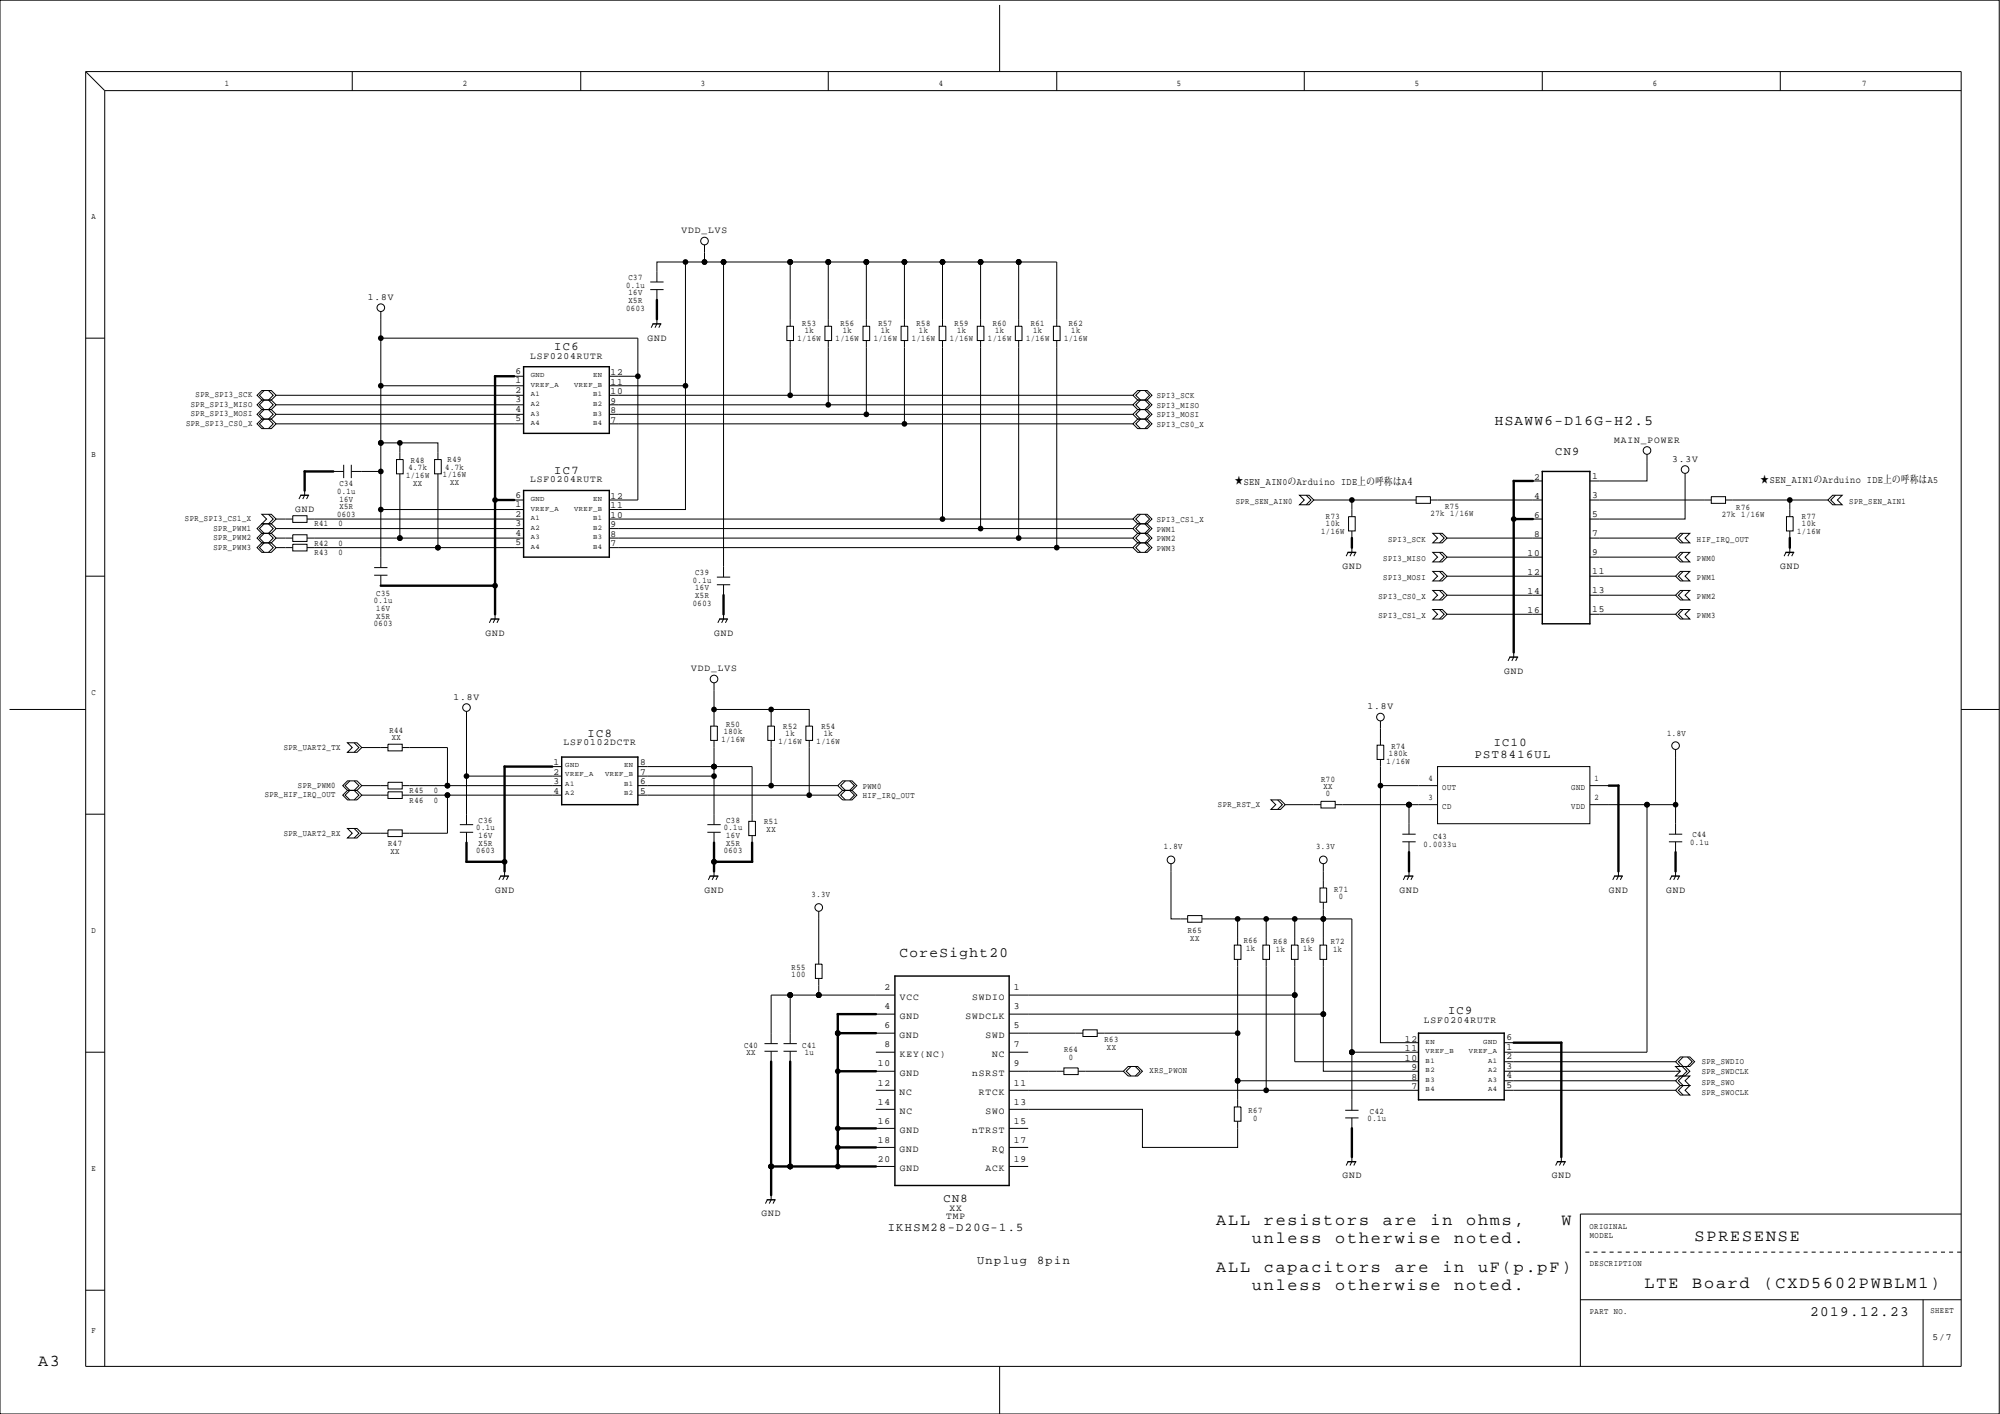
[picture p68: page 5]

unless otherwise noted.
ALL capacitors are in uF(p.pF)

# LBAD01XX1SC

CP1

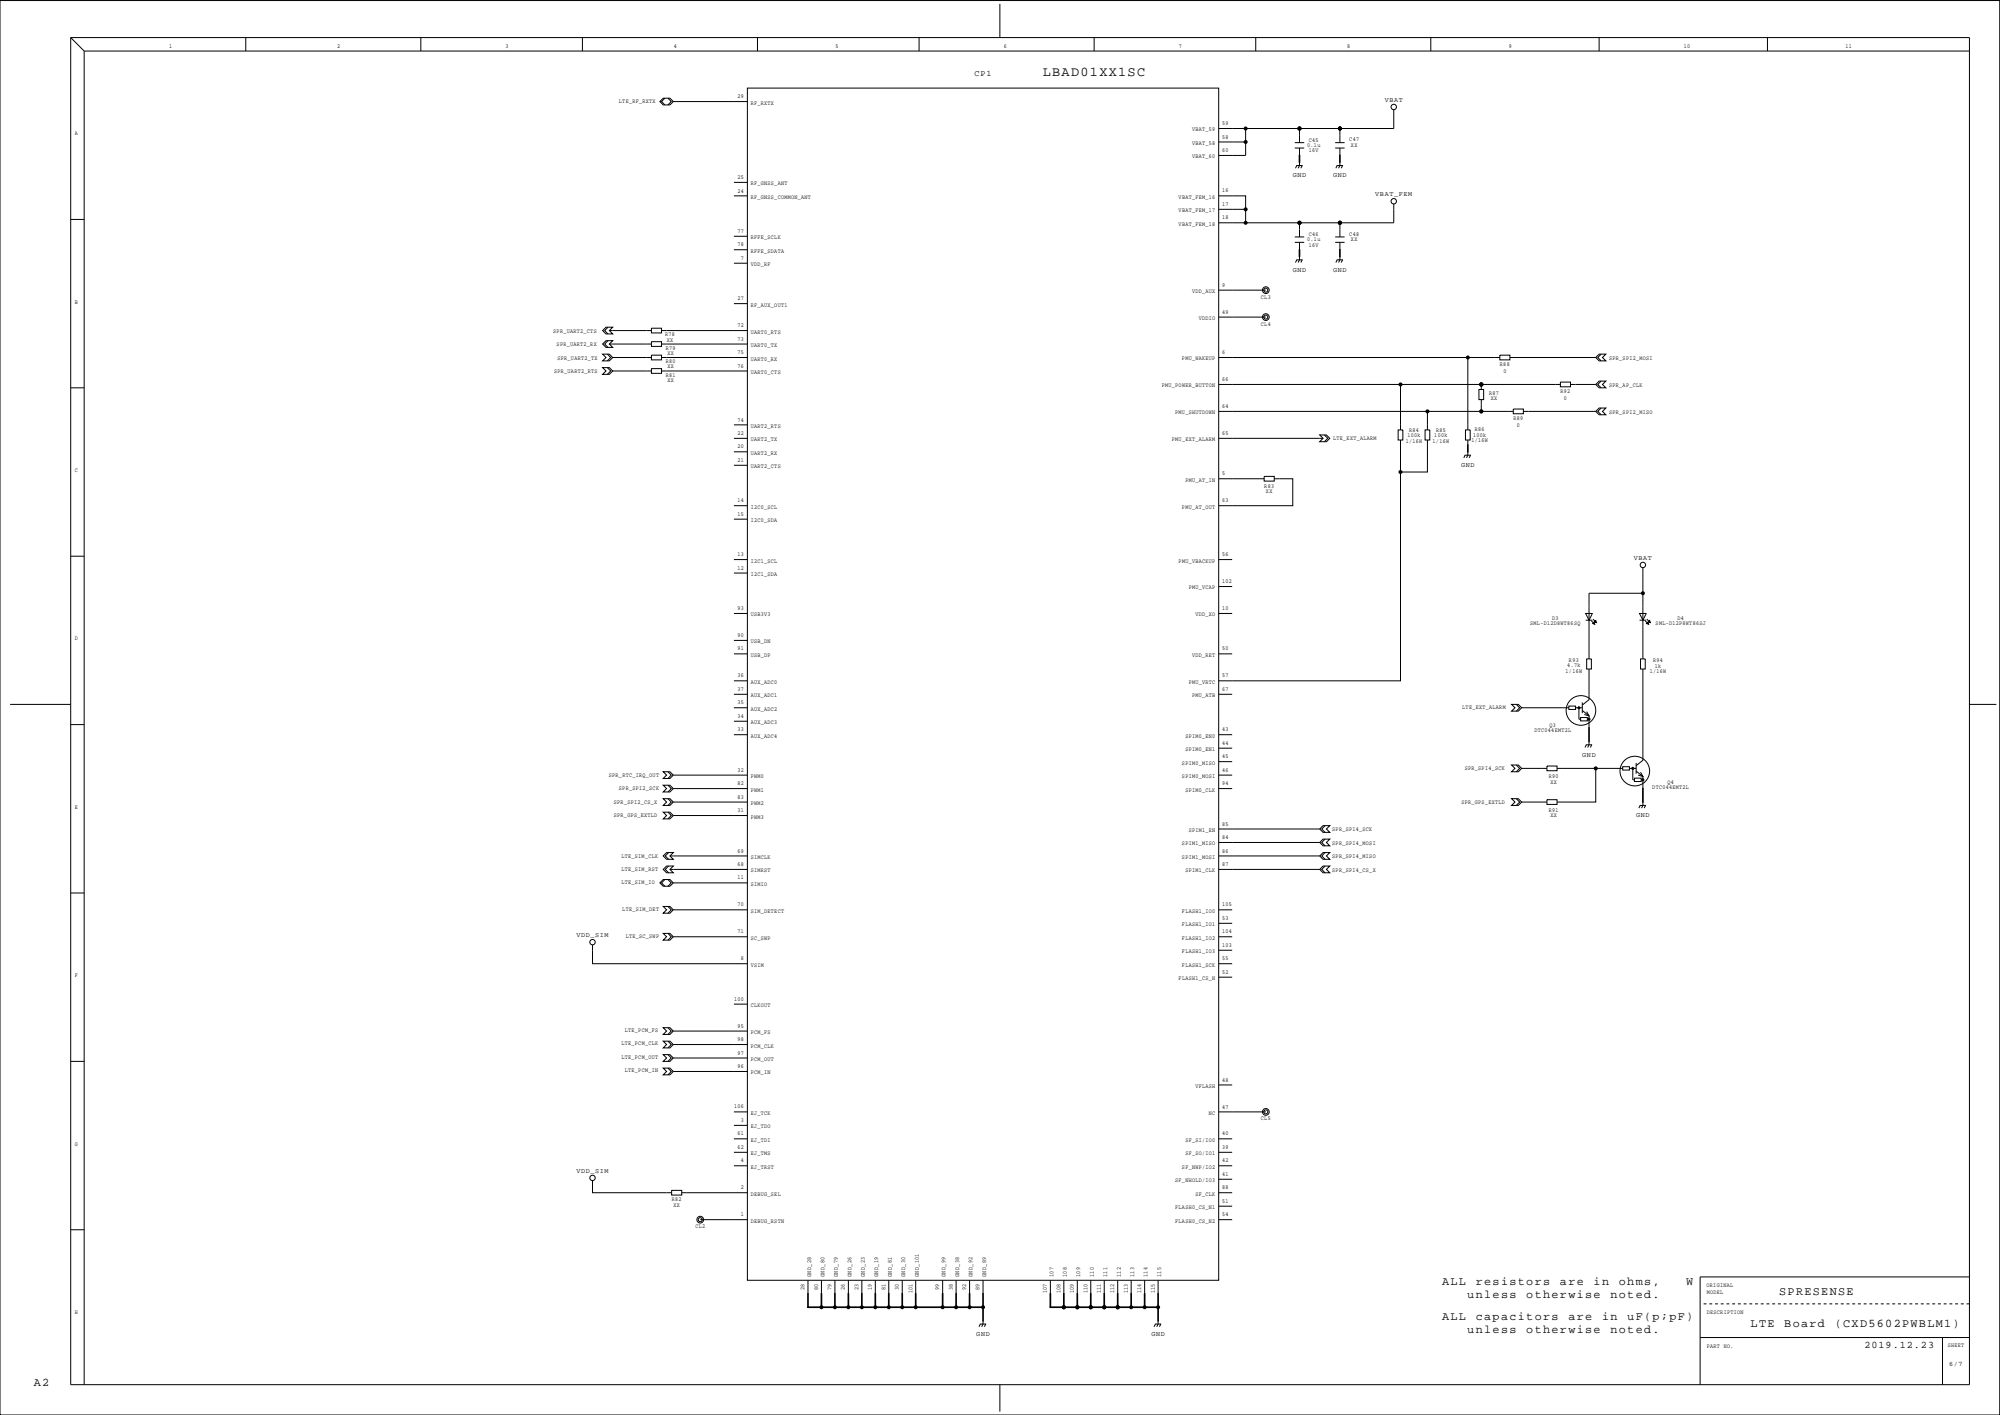
[picture p69: page 6]

unless otherwise noted.
ALL capacitors are in uF(p;pF)

IC13

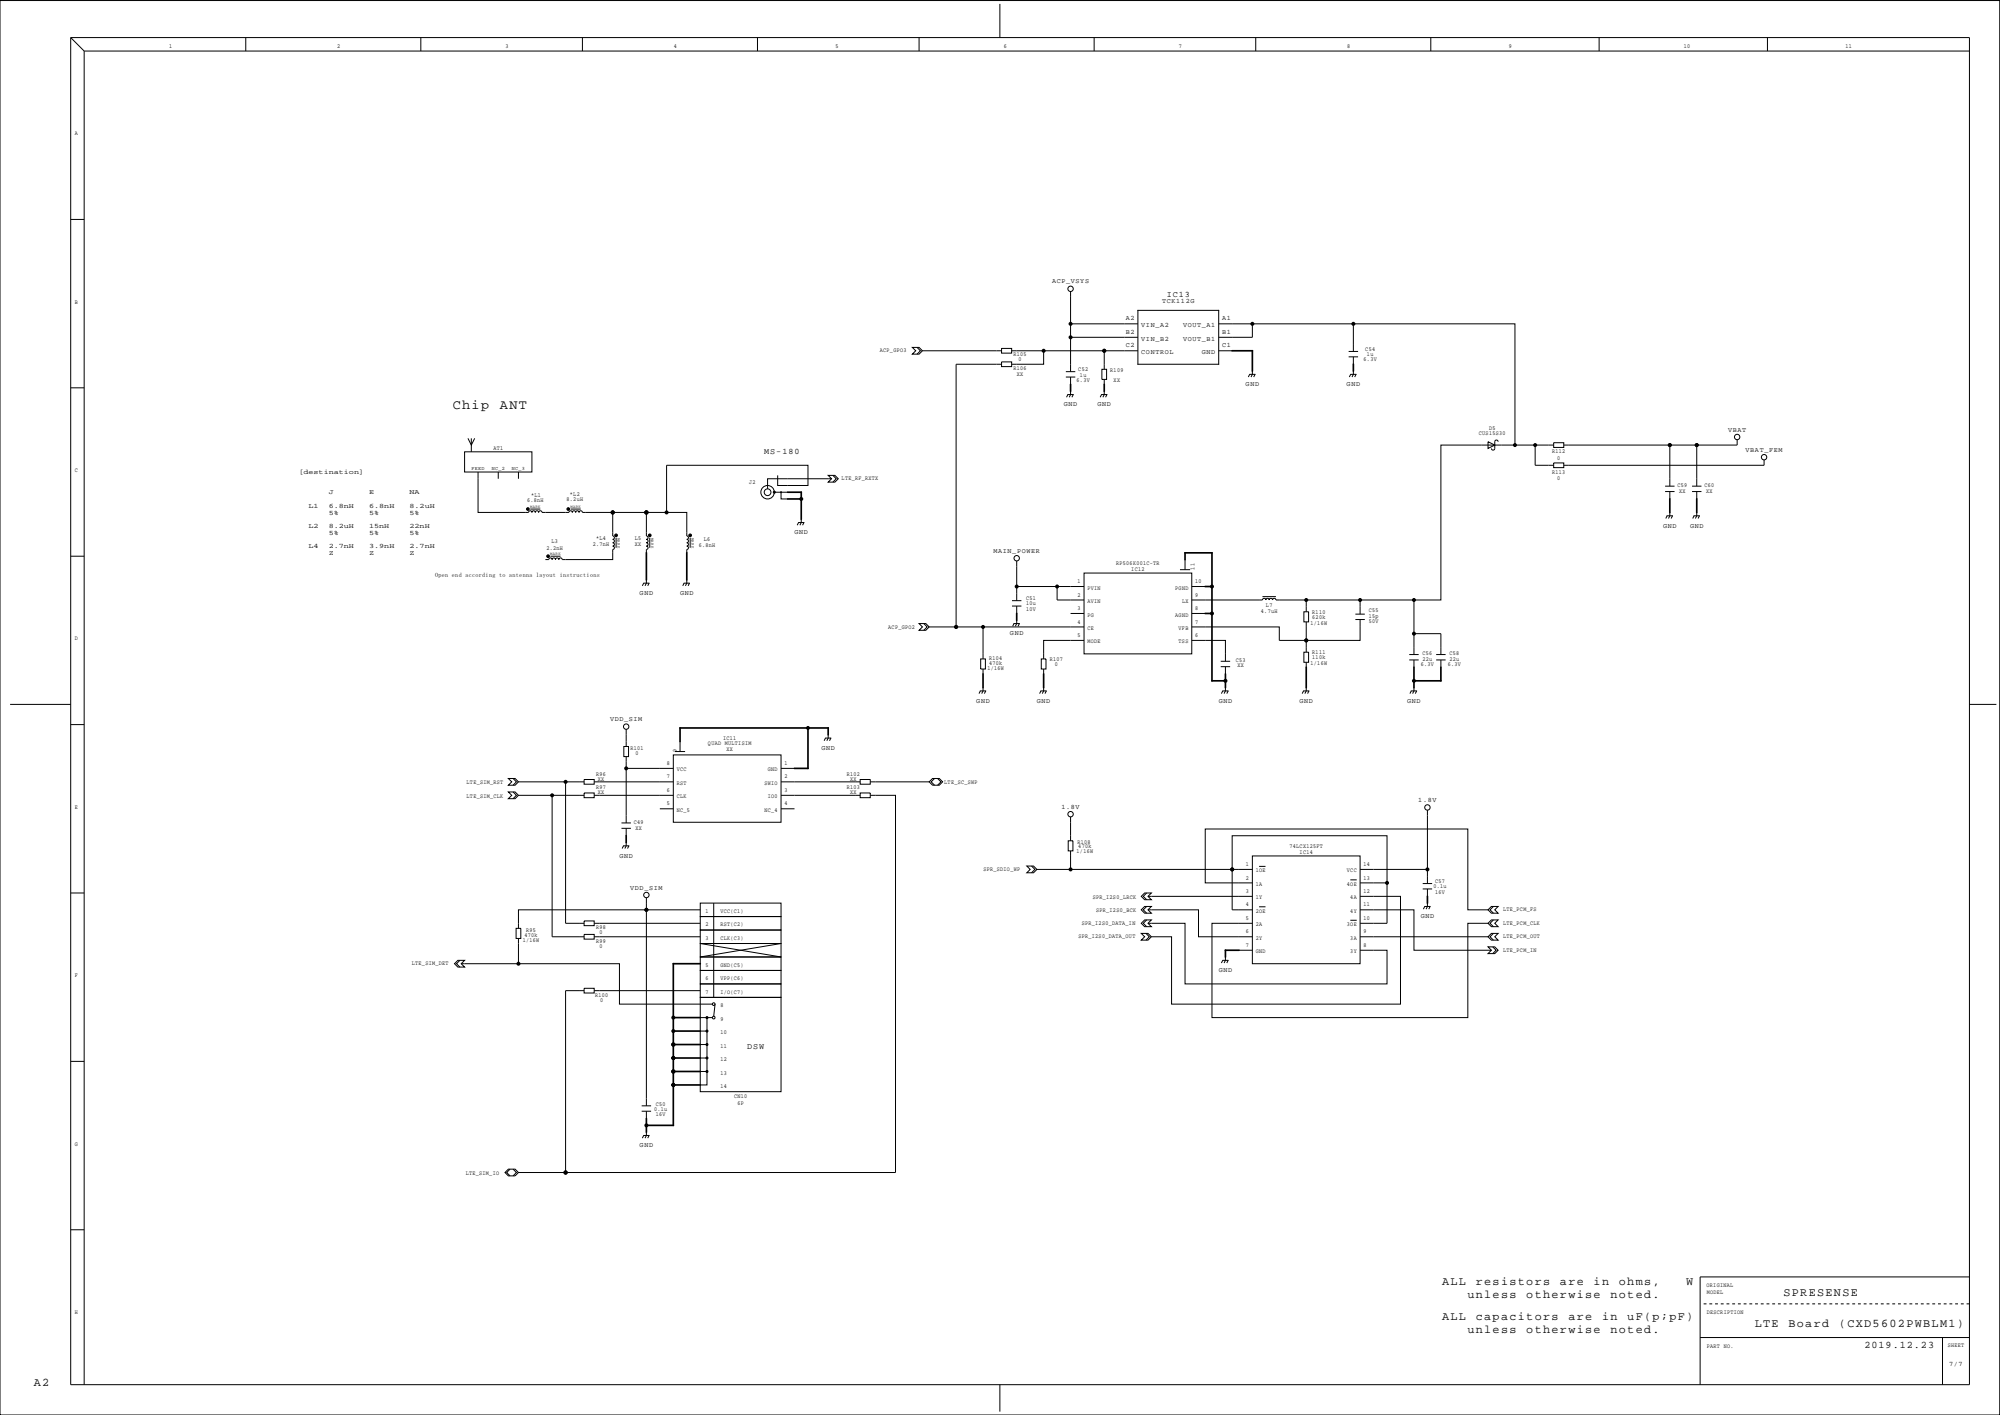
[picture p70: page 7]

Open end according to antenna layout instructions

1 | VCC(C1)

2 | RST(C2)

3 | CLK(C3)

5 | GND(C5)

6 | VPP(C6)

unless otherwise noted.
ALL capacitors are in uF(p;pF)
