sonydevworld/spresense-hw-design-files/CXD5602PWBGNSS1/board_dimensions/CXD5602PWBGNSS1_board_dimensions.pdf

## Spresense GNSS Add_on Board (CXD5602PWBGNSS1W) Dimensional Drawing

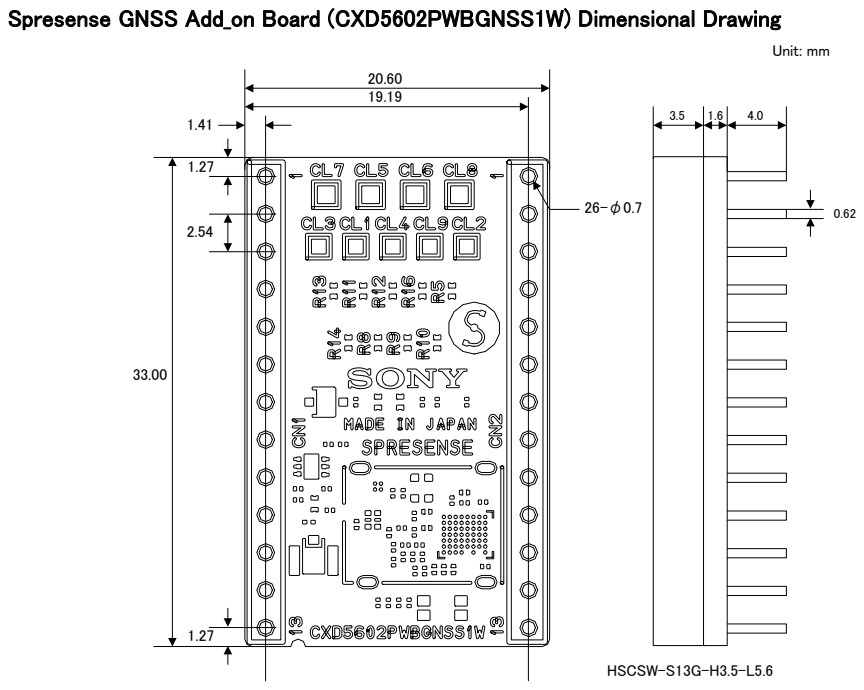
[picture p71: page 1]
HSCSW-S13G-H3.5-L5.6; Unit: mm
