sonydevworld/spresense-hw-design-files/CXD5602PWBLM1/board_dimensions/CXD5602PWBLM1_board_dimensions_en.pdf

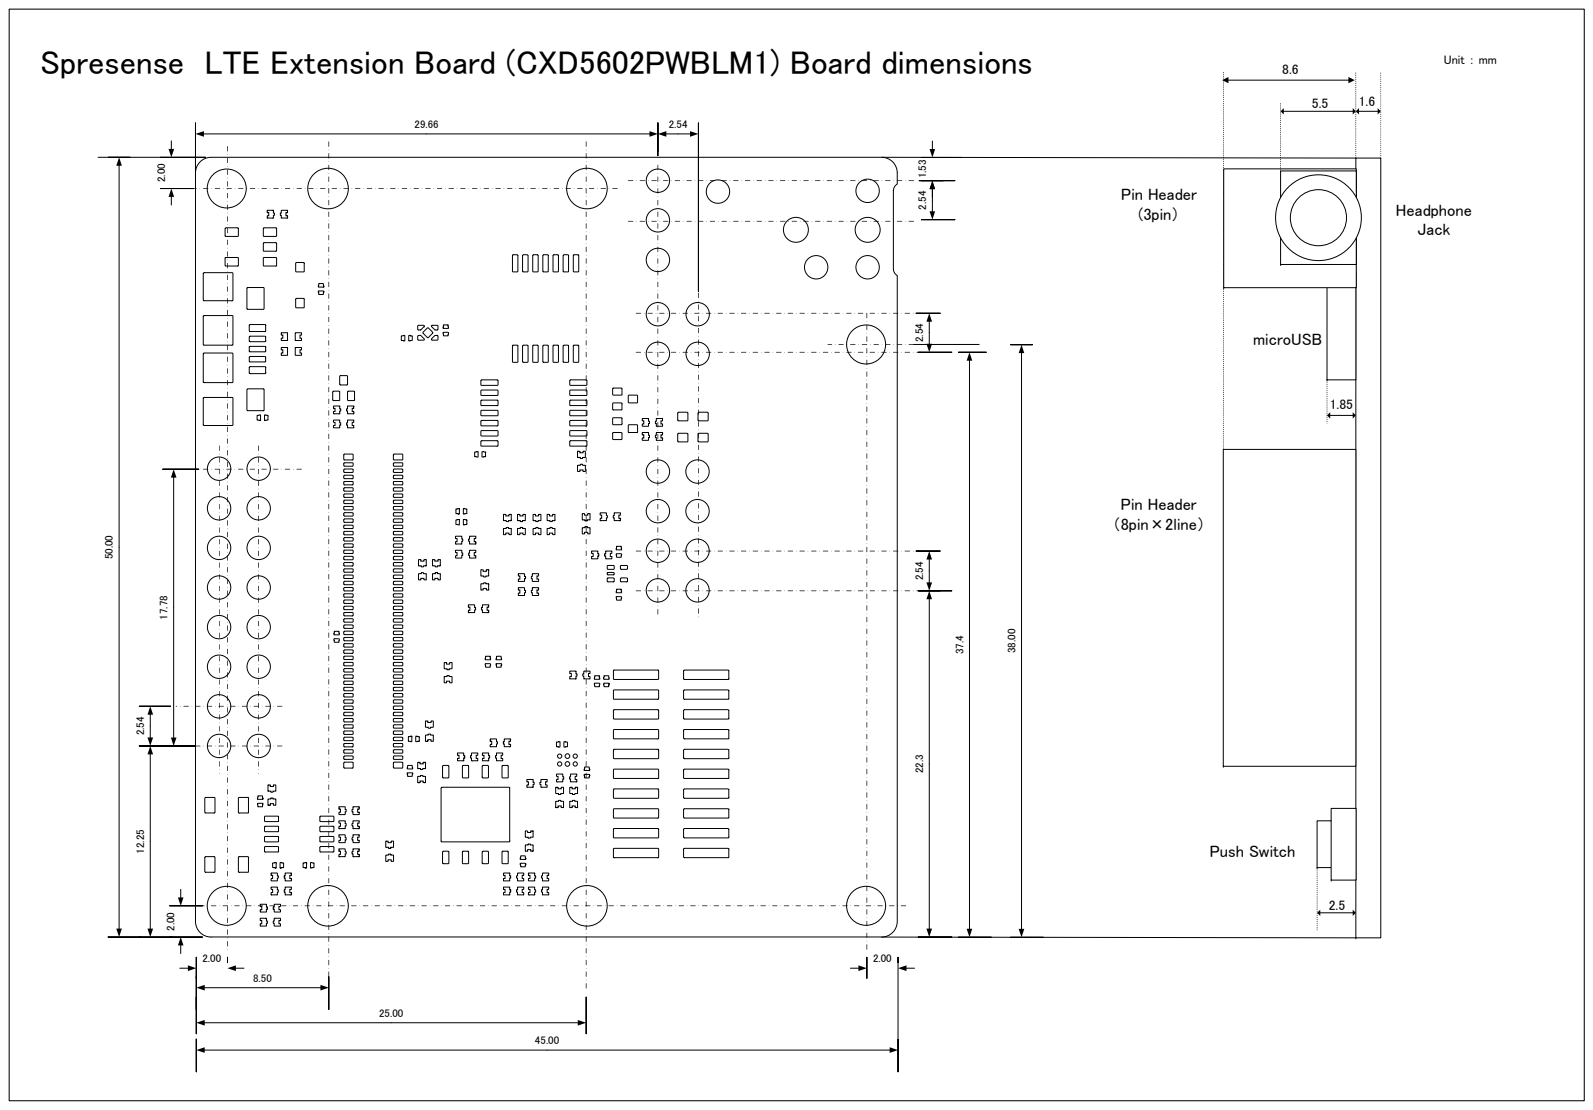
[picture p72: page 1]
Pin Header (3pin）; Pin Header （8pin×2line）; Push Switch; microUSB; Headphone Jack

Unit ： mm Spresense LTE Extension Board (CXD5602PWBLM1) Board dimensions
