sonydevworld/spresense-hw-design-files/CXD5602PWBCAM1/board_dimensions/CXD5602PWBCAM1_board_dimensions_en.pdf

# Spresense Camera Board (CXD5602PWBCAM1) Board dimensions

### Unit : mm

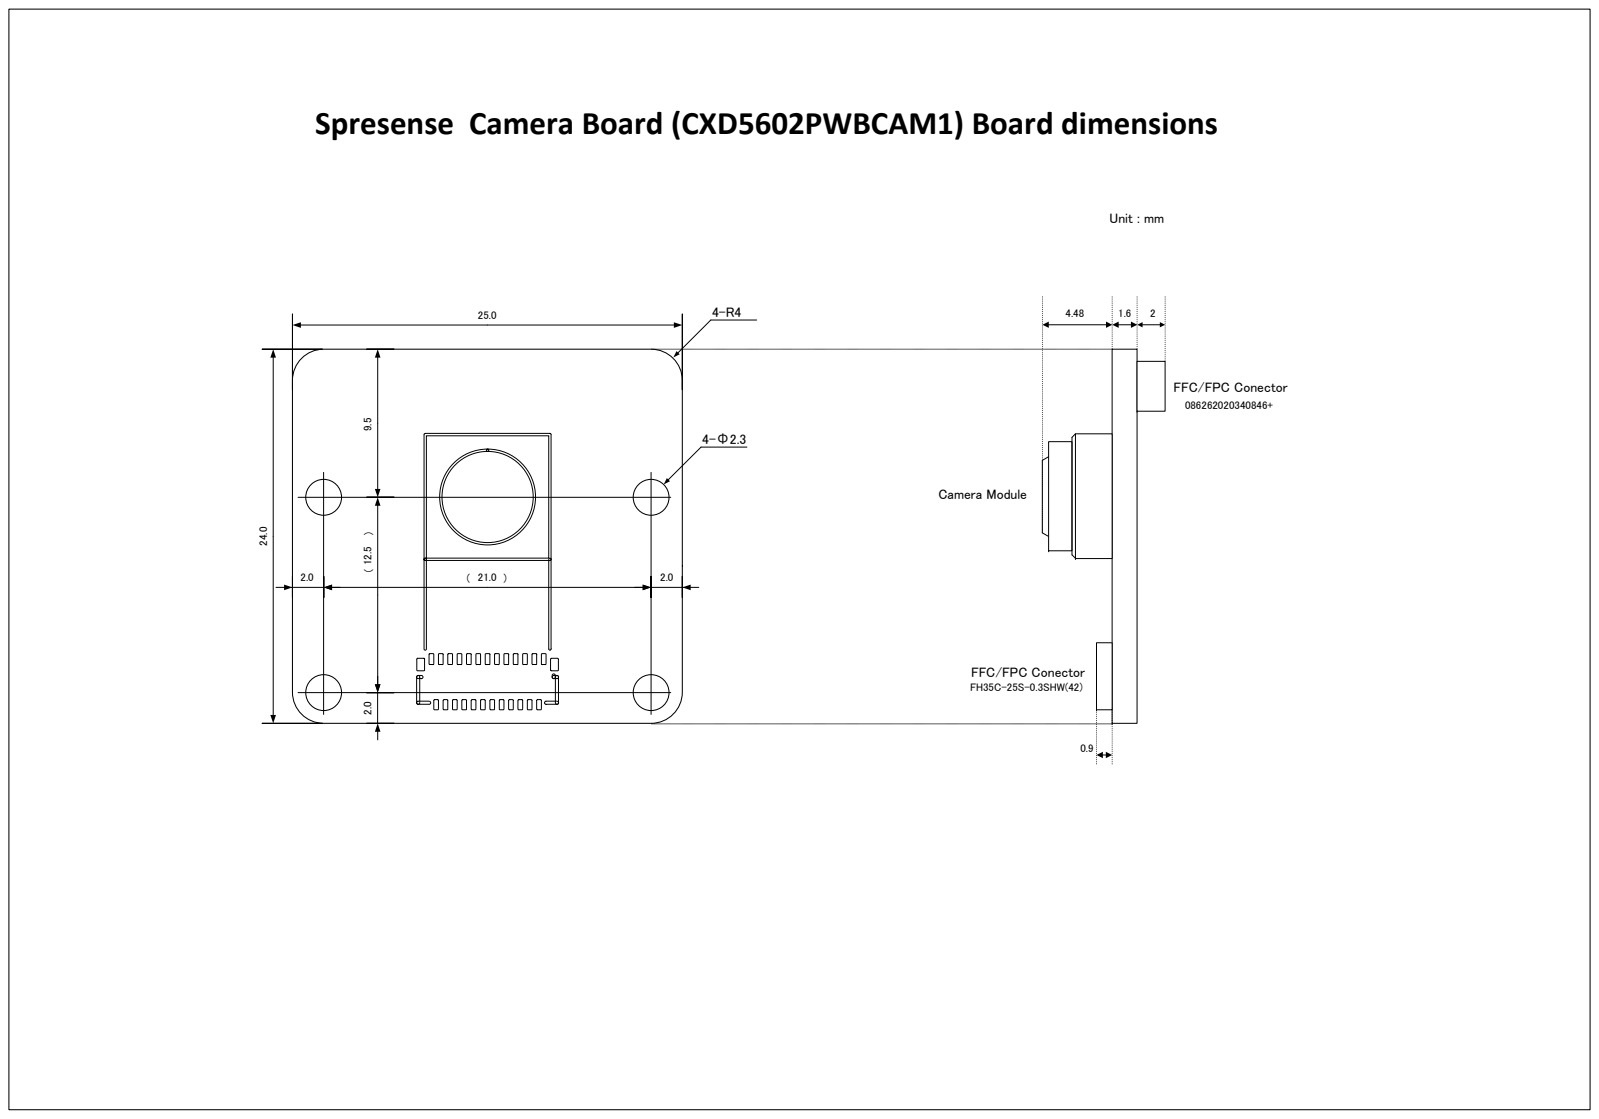
[picture p73: page 1]
Camera Module

FFC/FPC Conector

FH35C-25S-0.3SHW(42)
