sonydevworld/spresense-hw-design-files/CXD5602PWBCAM1/board_dimensions/CXD5602PWBCAM1_board_dimensions_ja.pdf

# Spresense Camera Board (CXD5602PWBCAM1)

### Unit : mm

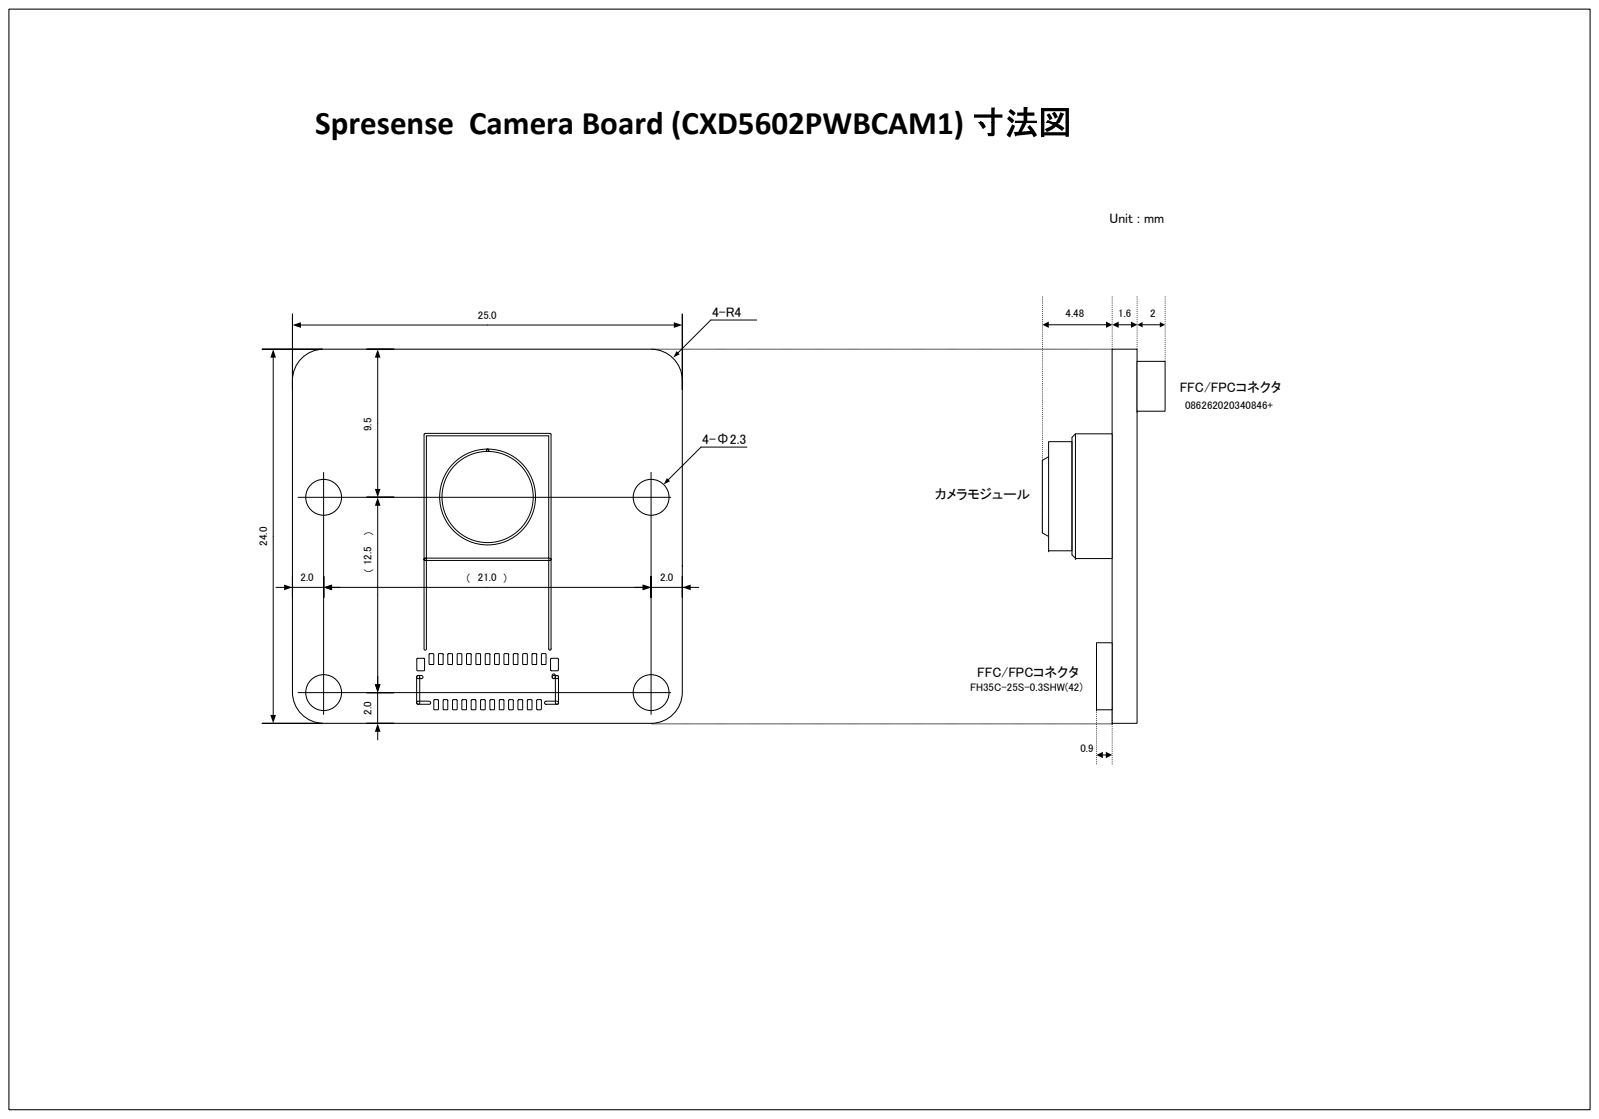
[picture p74: page 1]
FFC/FPCコネクタ; カメラモジュール; FH35C-25S-0.3SHW(42)
