sonydevworld/spresense-hw-design-files/CXD5602PWBEXT1/board_dimensions/CXD5602PWBEXT1_board_dimensions_en.pdf

# Spresense Extension Board (CXD5602PWBEXT1) Board dimensions

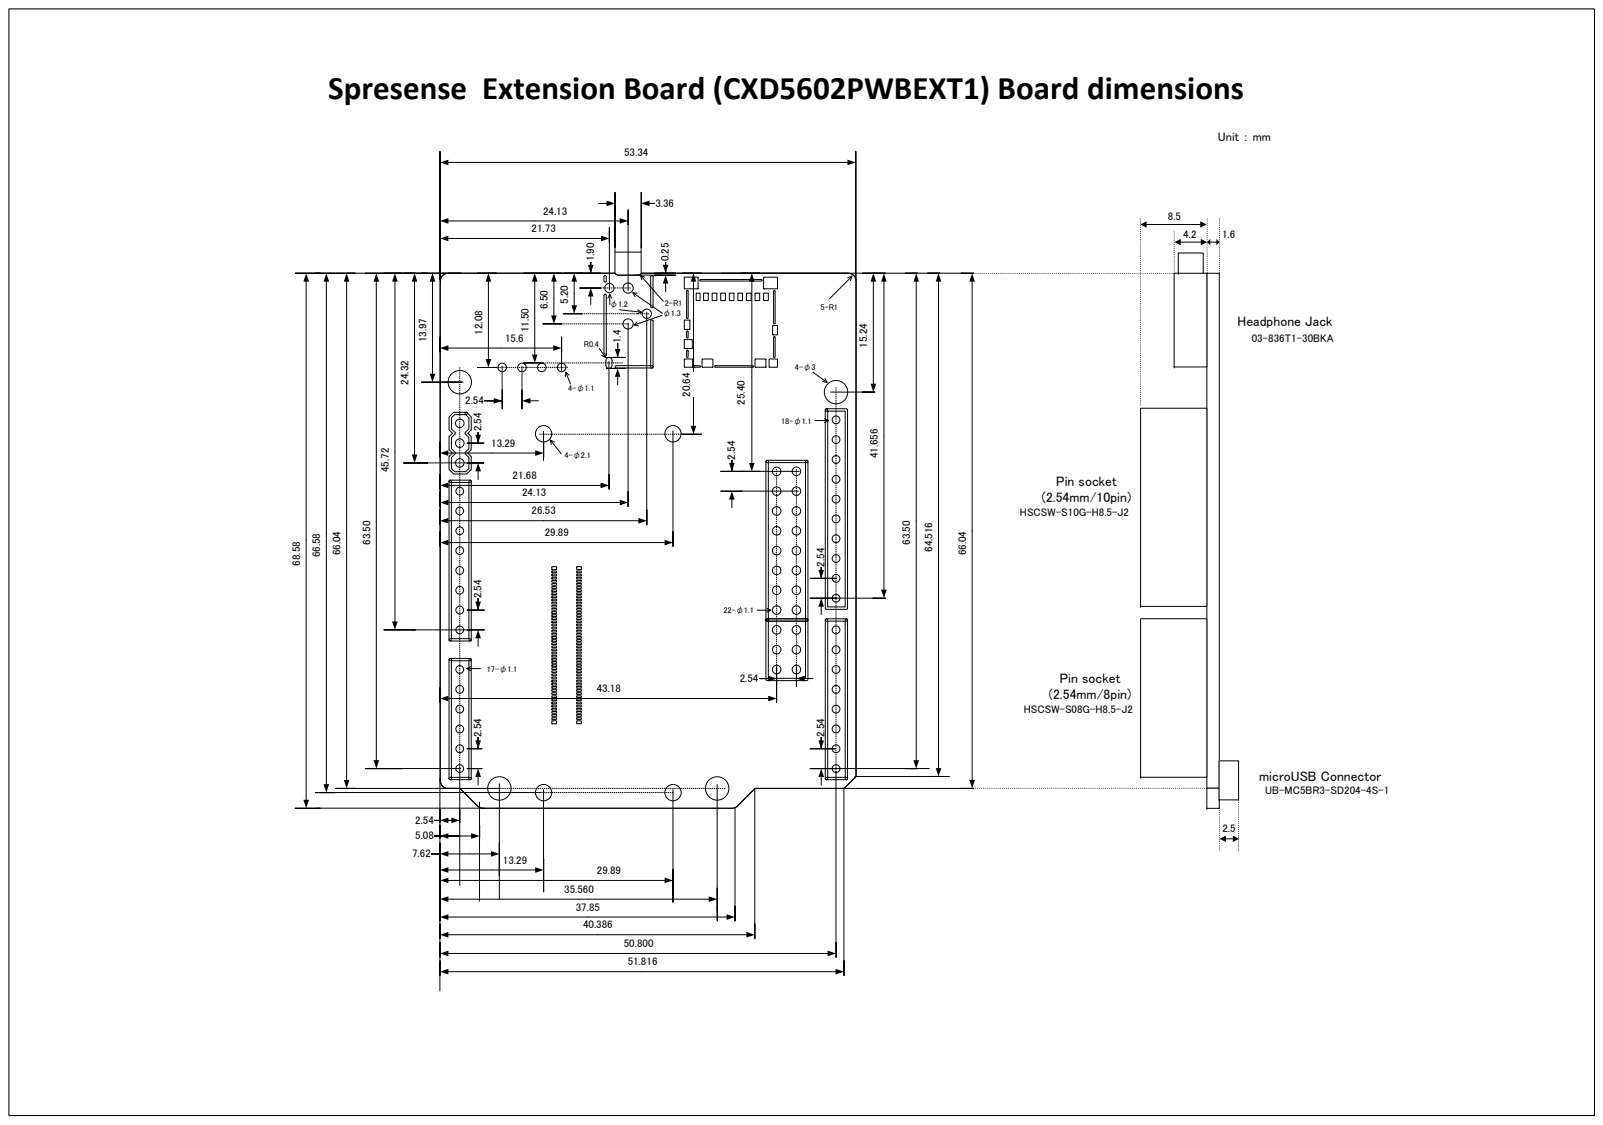
[picture p75: page 1]
Unit ： mm; Headphone Jack; Pin socket (2.54mm/10pin); Pin socket (2.54mm/8pin); microUSB Connector UB-MC5BR3-SD204-4S-1; 03-836T1-30BKA; HSCSW-S08G-H8.5-J2; HSCSW-S10G-H8.5-J2
