sonydevworld/spresense-hw-design-files/CXD5602PWBEXT1/board_dimensions/CXD5602PWBEXT1_board_dimensions_ja.pdf

# Spresense Extension Board (CXD5602PWBEXT1)

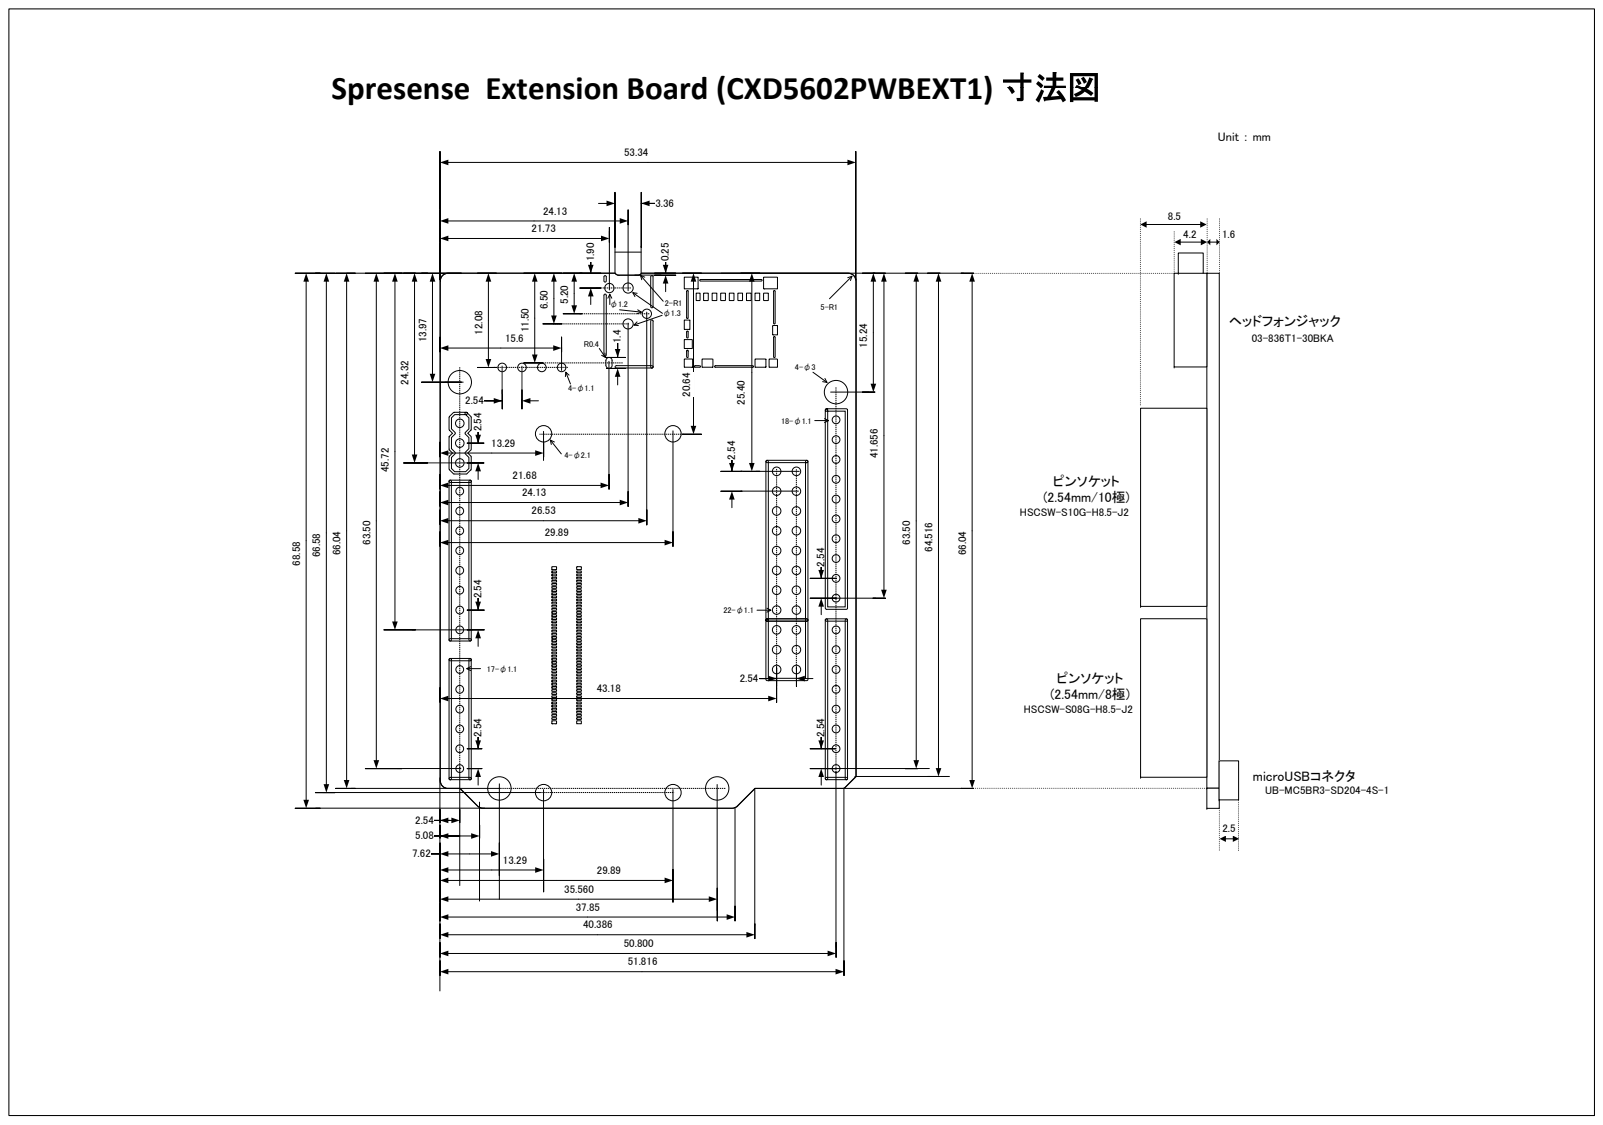
[picture p76: page 1]
Unit ： mm; ヘッドフォンジャック; ピンソケット (2.54mm/10極); ピンソケット (2.54mm/8極); microUSBコネクタ UB-MC5BR3-SD204-4S-1; 03-836T1-30BKA; HSCSW-S08G-H8.5-J2; HSCSW-S10G-H8.5-J2
