sonydevworld/spresense-hw-design-files/CXD5602PWBMAIN1/board_dimensions/CXD5602PWBMAIN1_board_dimensions_en.pdf

# Spresense Main Board (CXD5602PWBMAIN1) Board dimensions

### Unit : mm

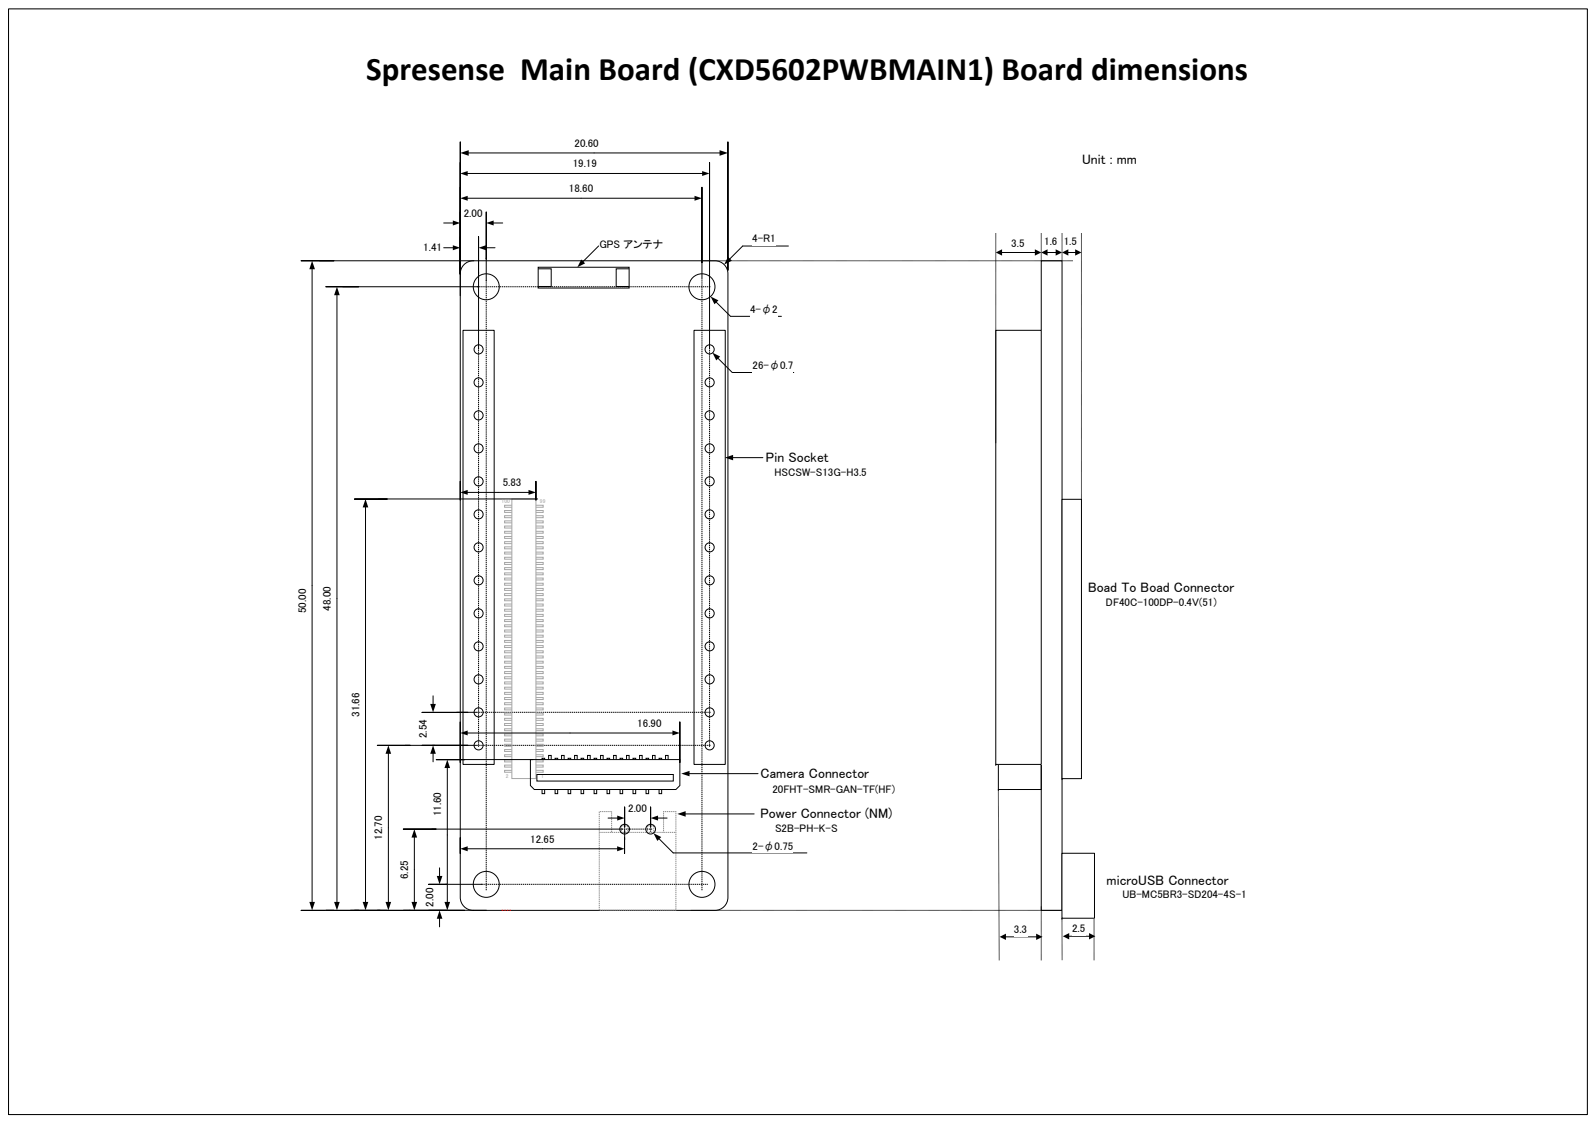
[picture p77: page 1]
Pin Socket HSCSW-S13G-H3.5; GPS アンテナ; microUSB Connector

Boad To Boad Connector

Camera Connector
20FHT-SMR-GAN-TF(HF)
Power Connector (NM)
