sonydevworld/spresense-hw-design-files/CXD5602PWBMAIN1/board_dimensions/CXD5602PWBMAIN1_board_dimensions_ja.pdf

# Spresense Main Board (CXD5602PWBMAIN1)

### Unit : mm

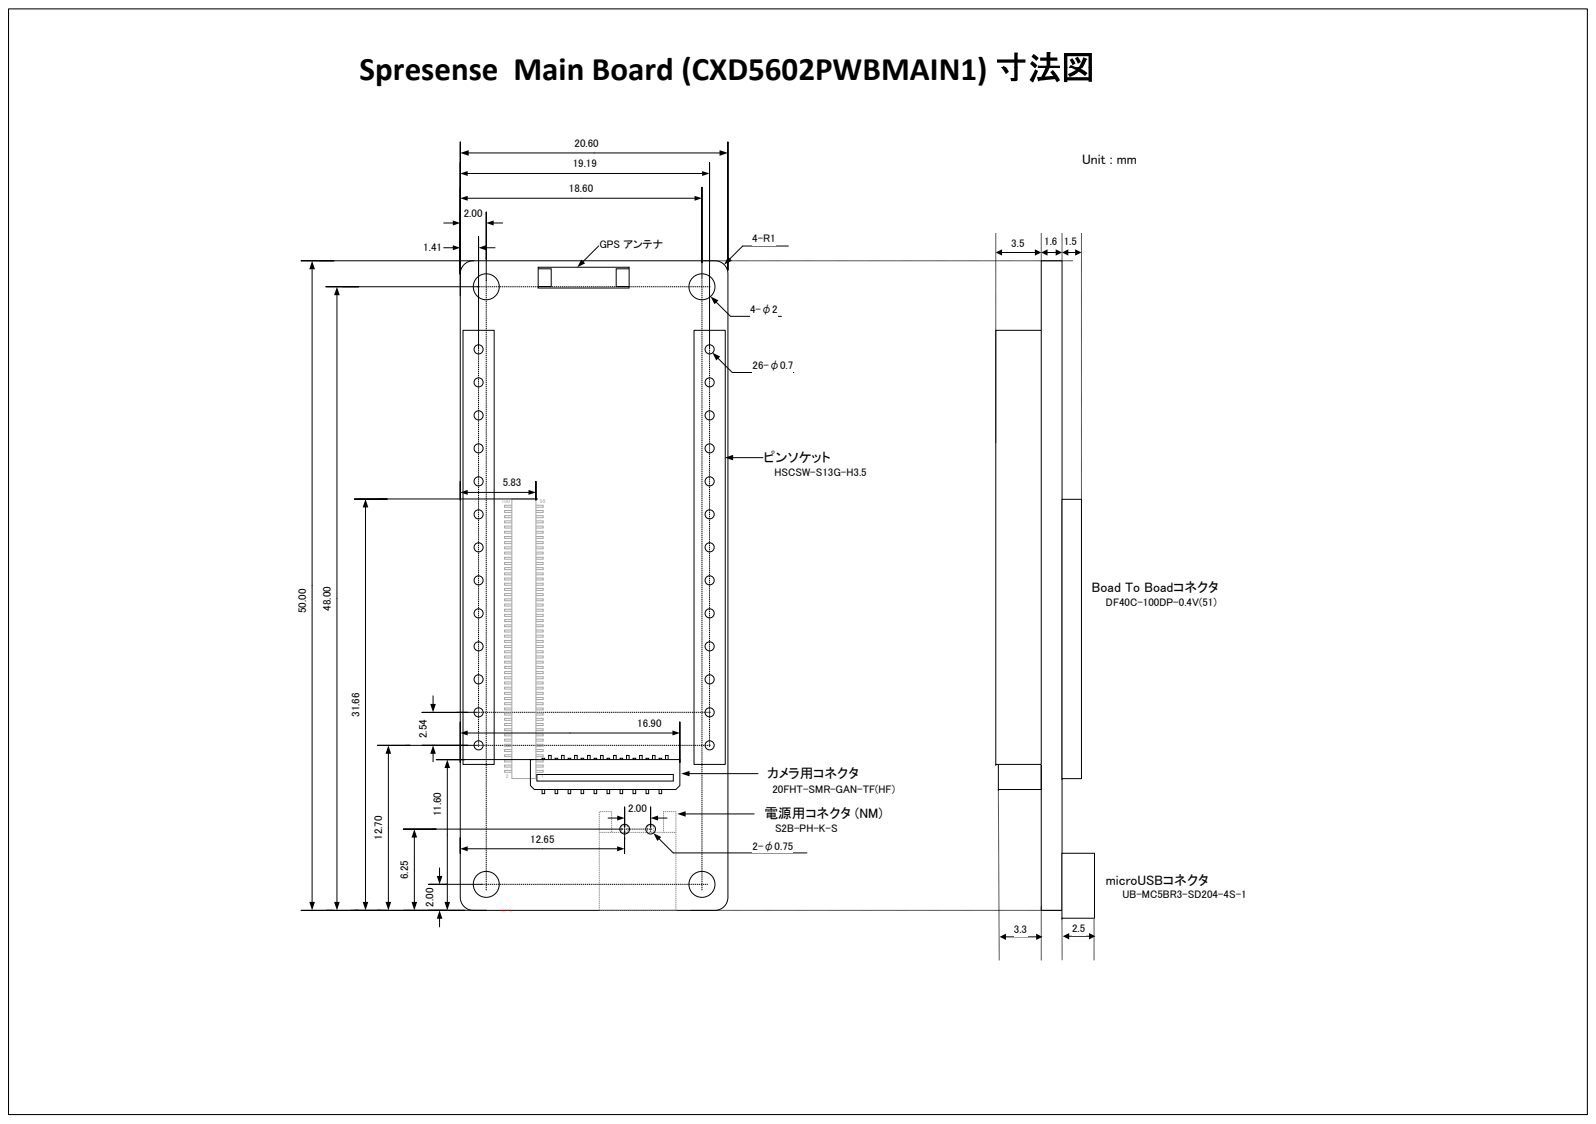
[picture p78: page 1]
ピンソケット HSCSW-S13G-H3.5; GPS アンテナ; microUSBコネクタ

Boad To Boadコネクタ

カメラ用コネクタ
20FHT-SMR-GAN-TF(HF)
電源用コネクタ (NM)
