sonydevworld/spresense-hw-design-files/CXD5602PWBCAM2/parts_layout/CXD5602PWBCAM2_part_layout.pdf

# Side-A

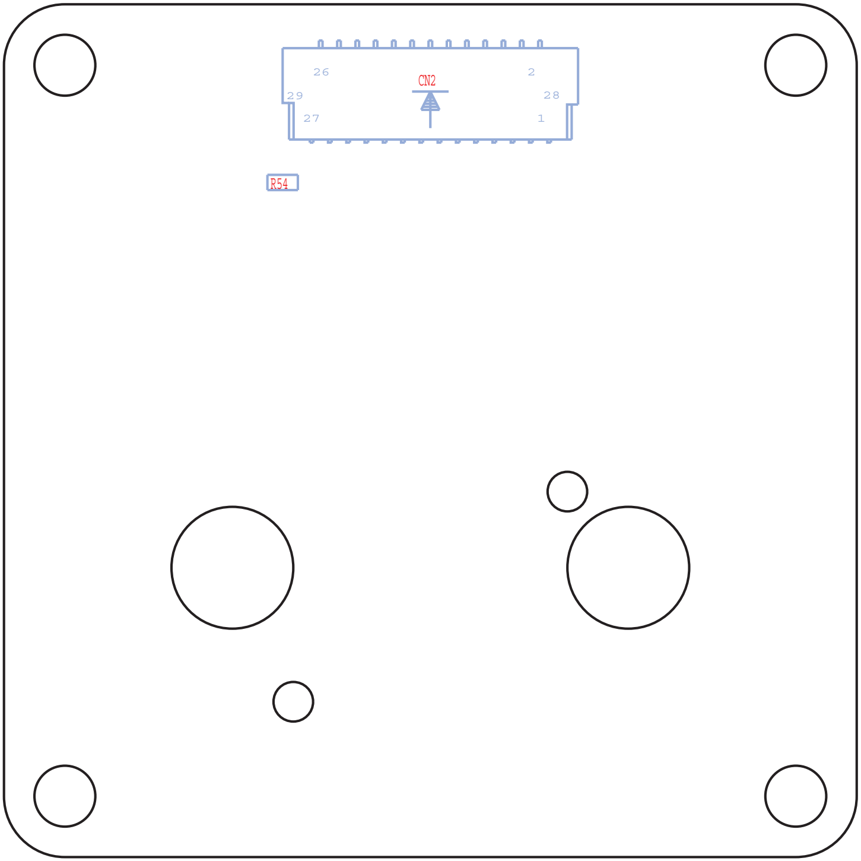
[picture p82: figure]

# Side-B

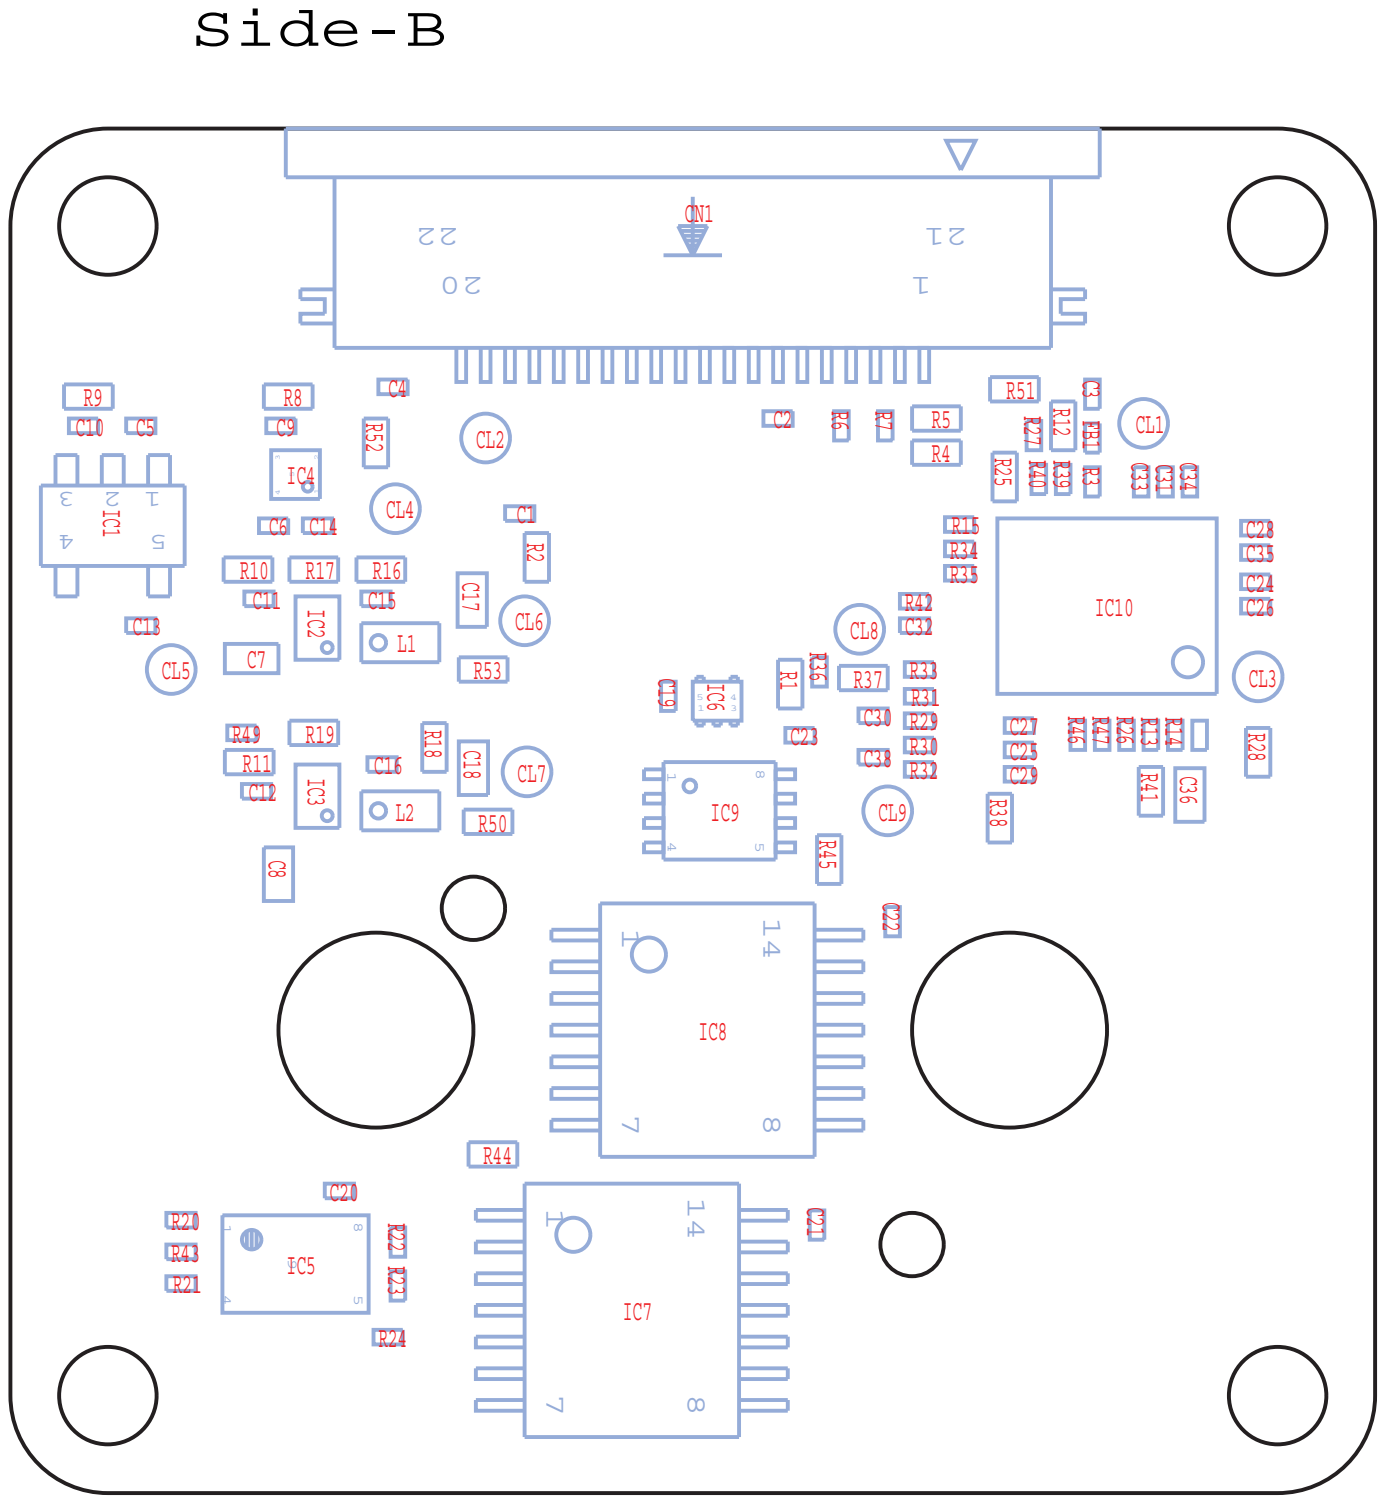
[picture p83: page 2]
