sonydevworld/spresense-hw-design-files/CXD5602PWBCAM1/parts_layout/CXD5602PWBCAM1_part_layout.pdf

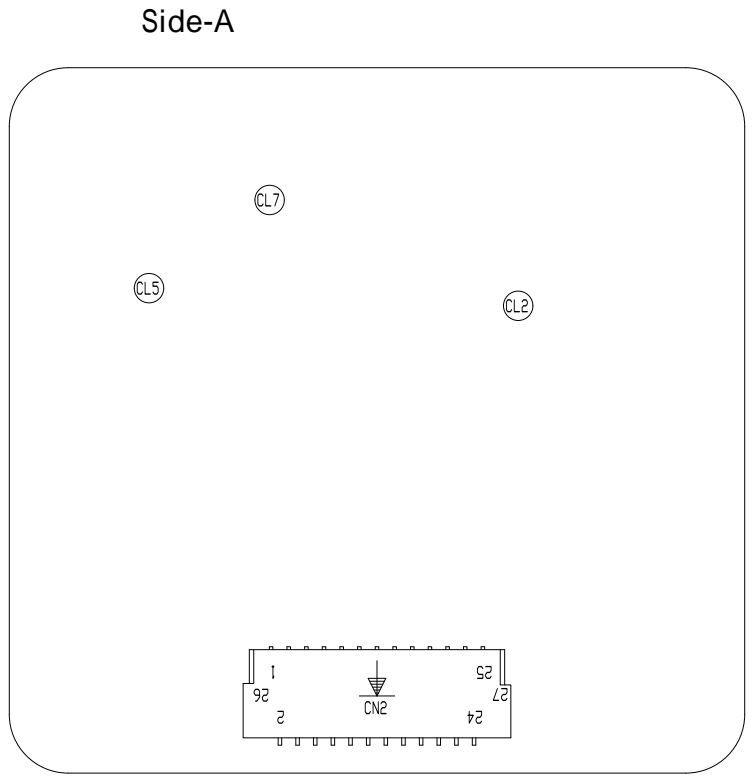
[picture p84: page 1]

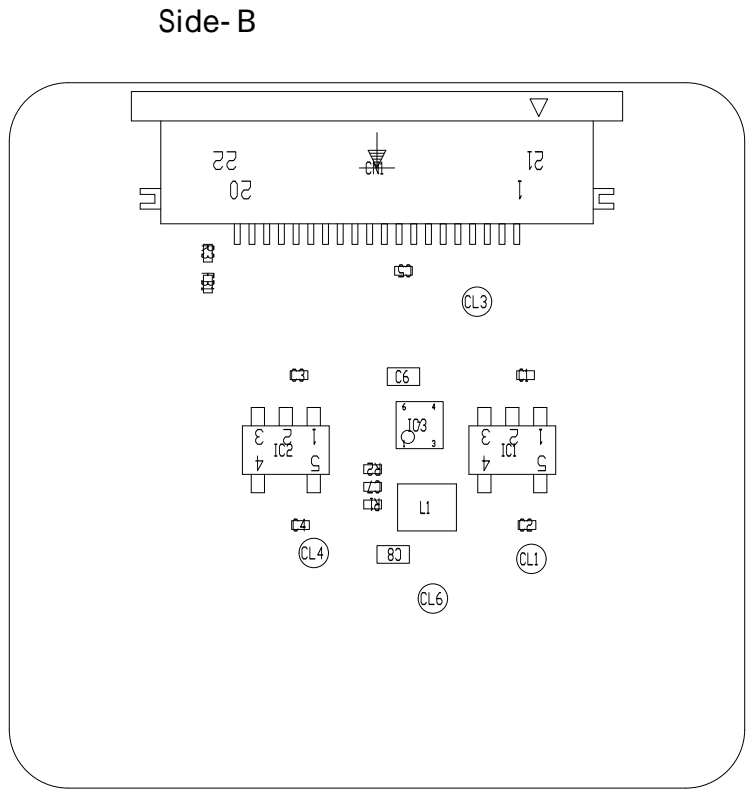
[picture p85: page 2]
