sonydevworld/spresense-hw-design-files/CXD5602PWBCAM1/schematics/CXD5602PWBCAM1_schematics.pdf

086262020340868+

A

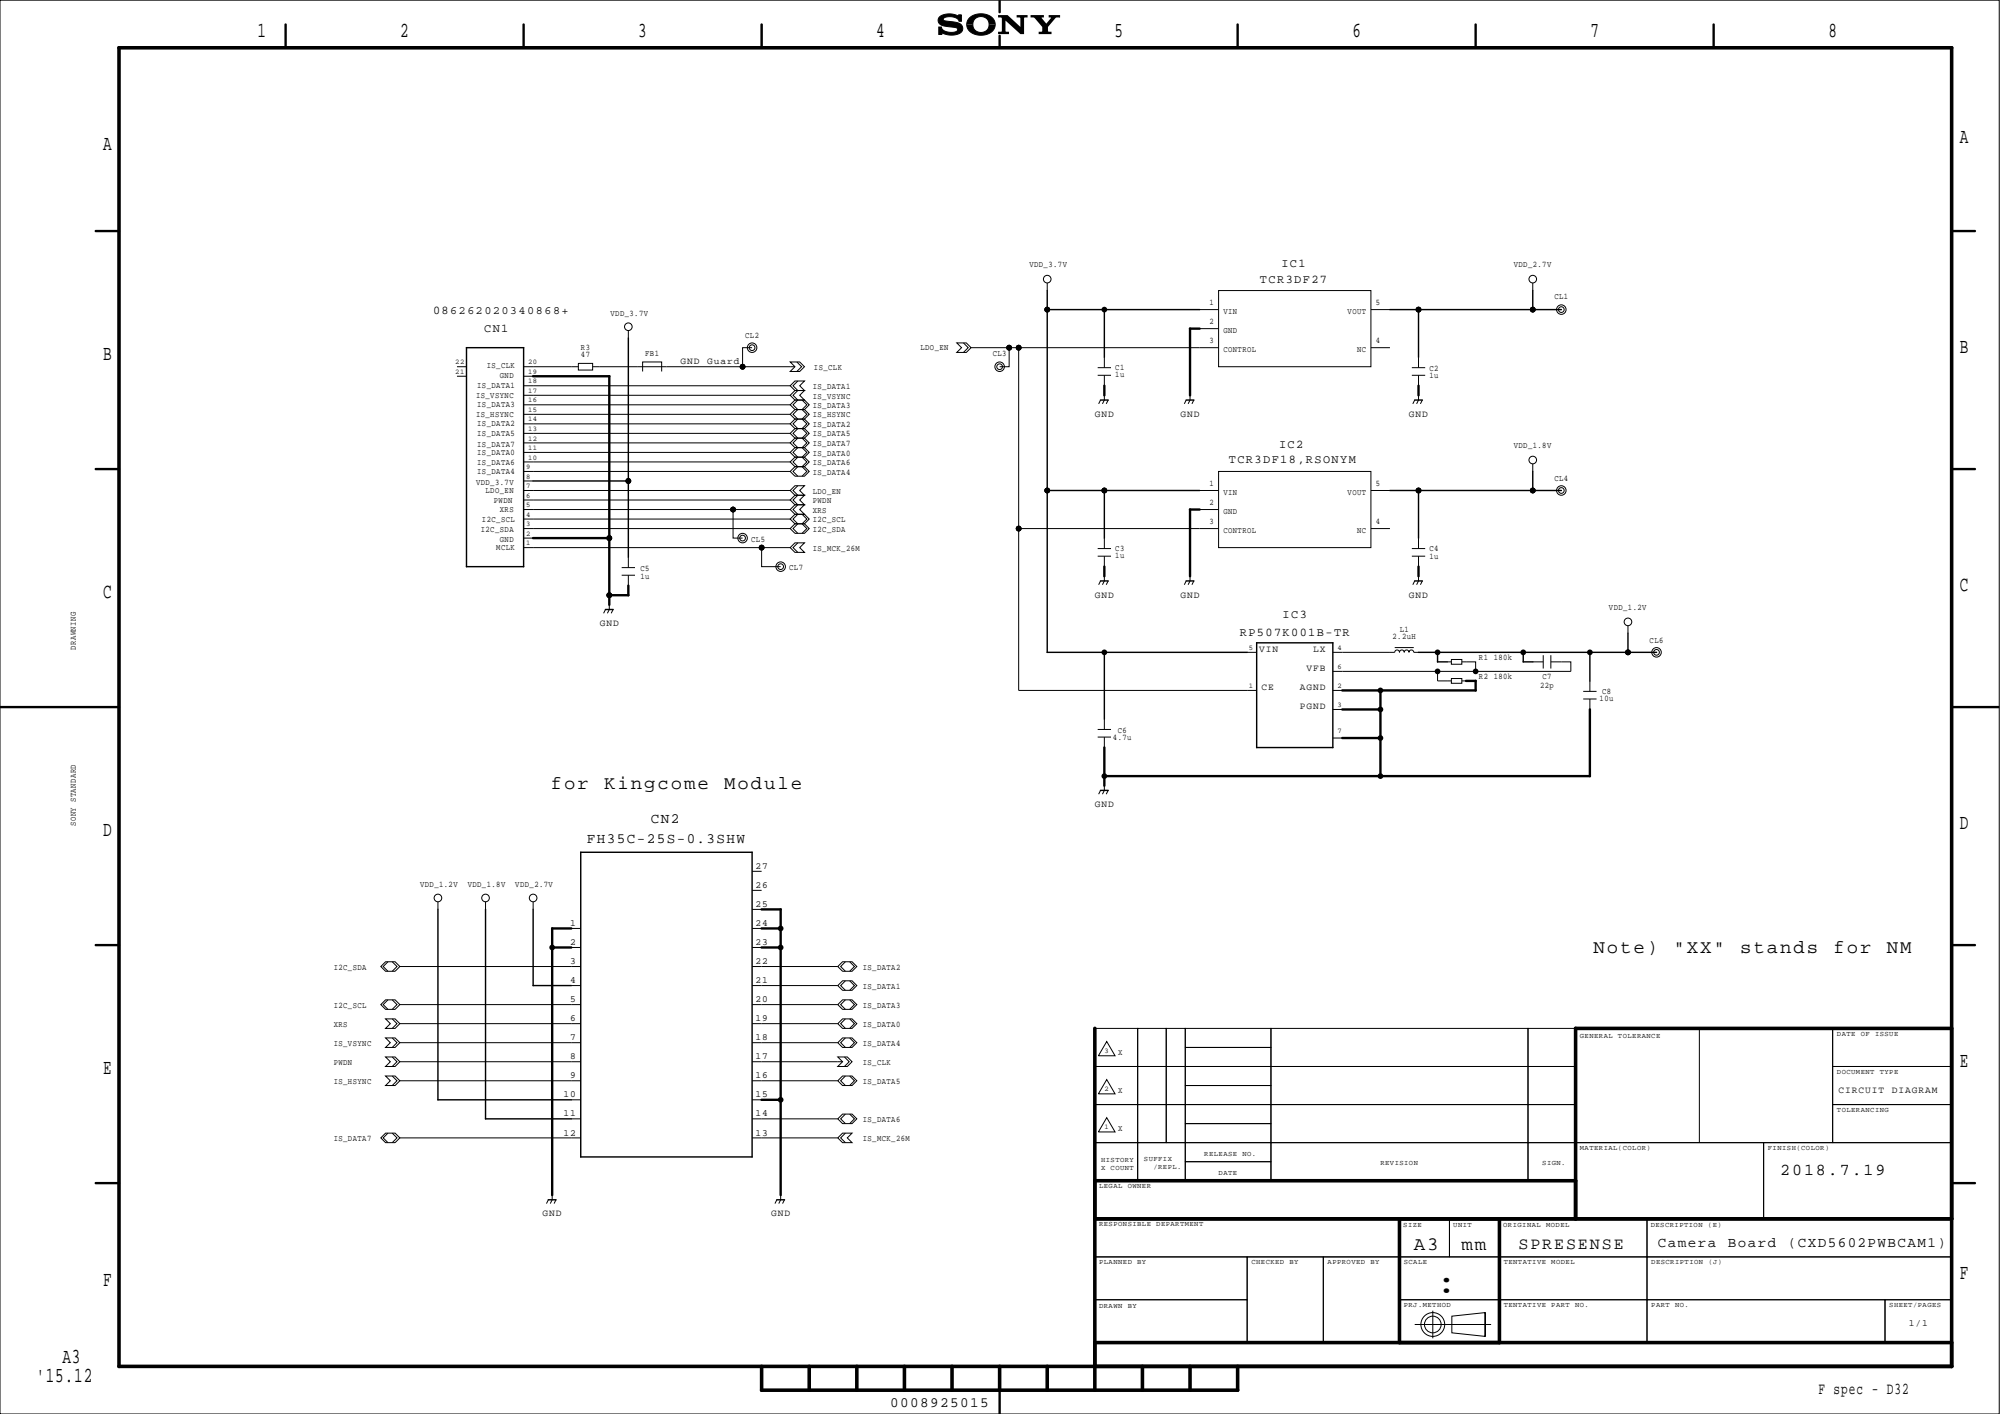
[picture p86: page 1]

Note) "XX" stands for NM
