sonydevworld/spresense-hw-design-files/CXD5602PWBEXT1/parts_layout/CXD5602PWBEXT1_part_layout.pdf

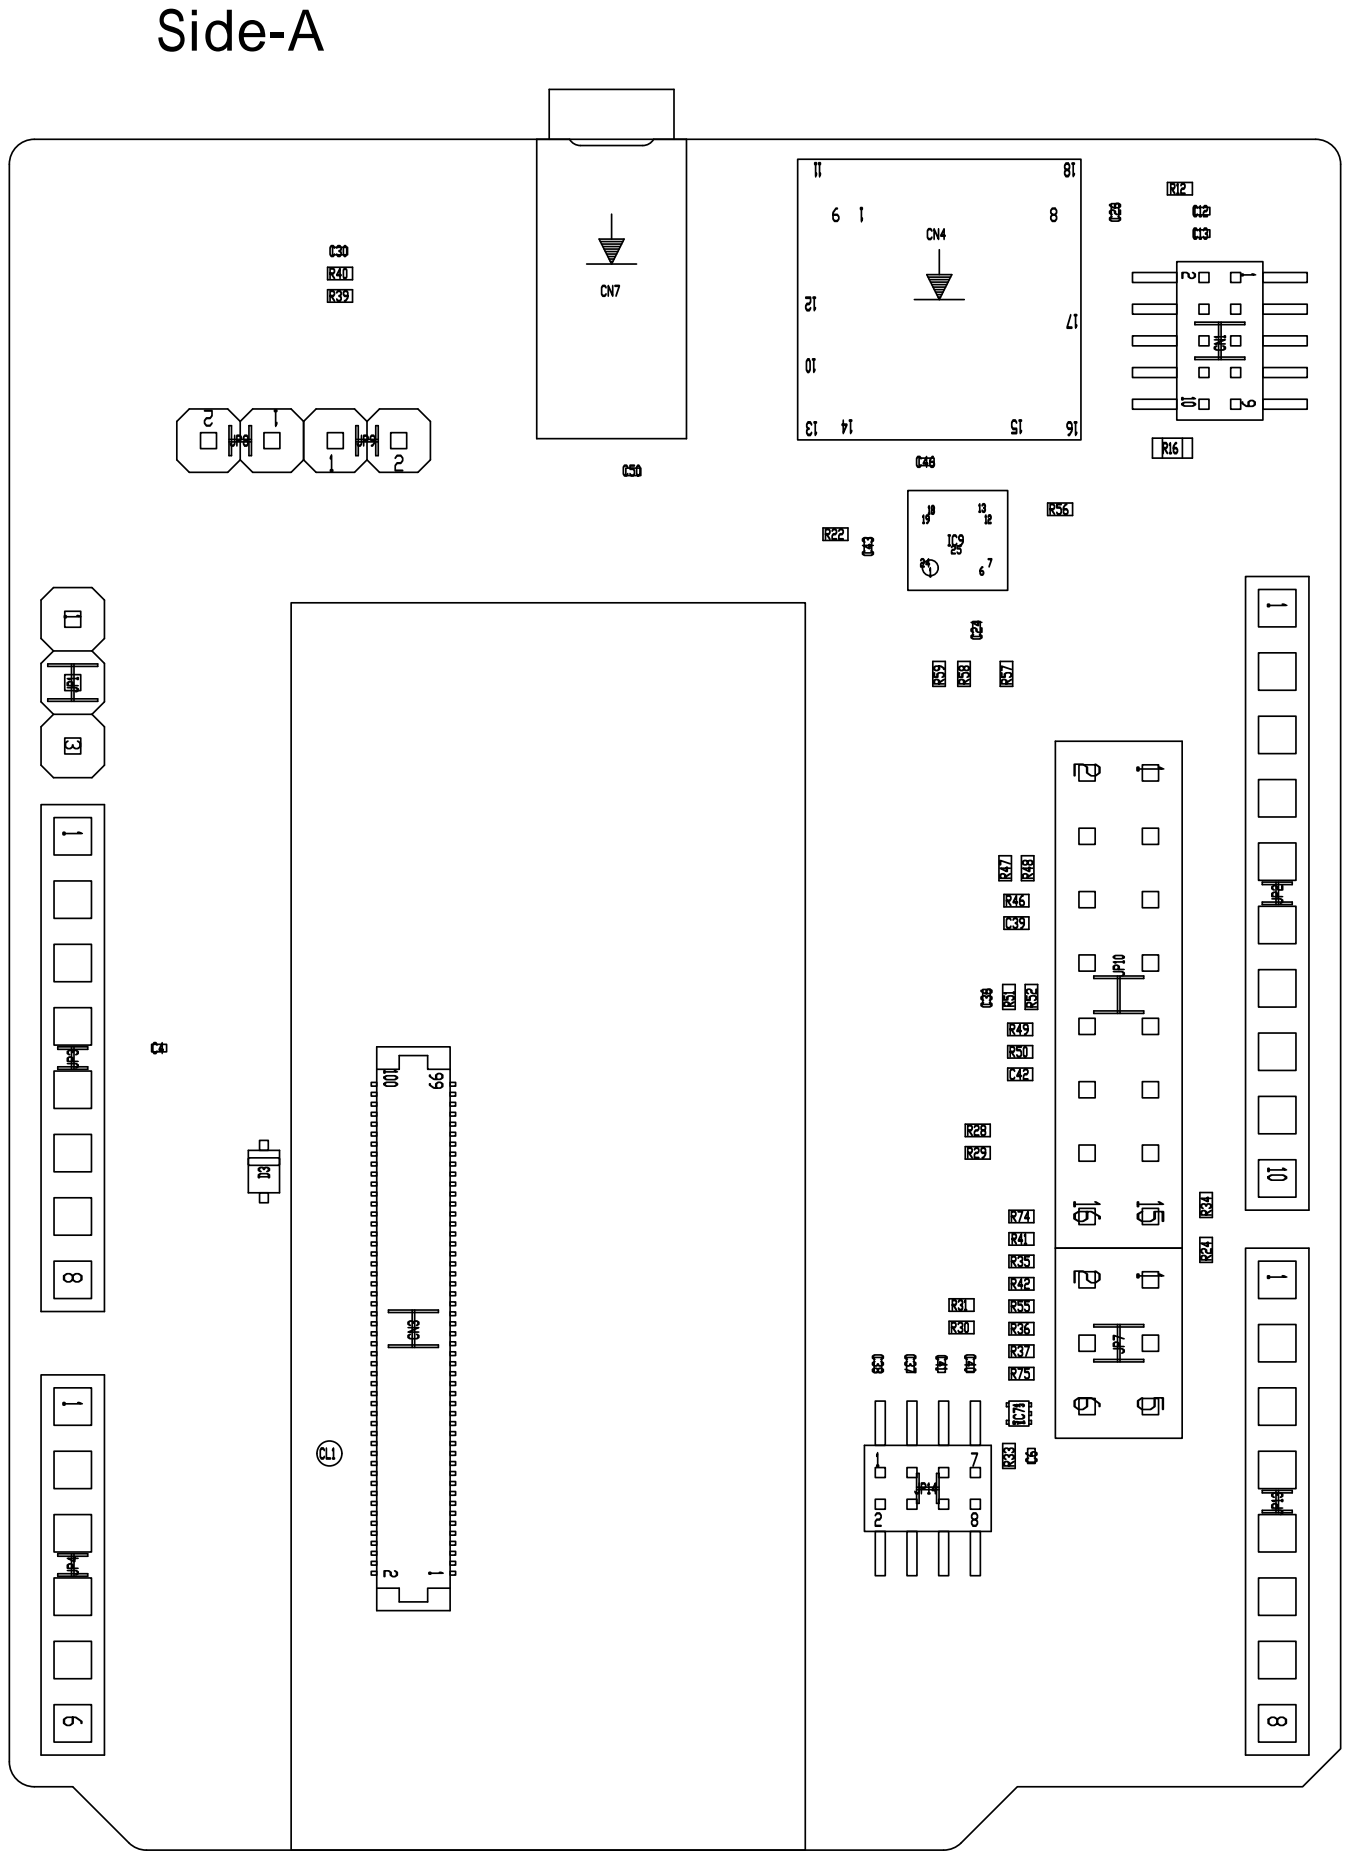
[picture p87: page 1]

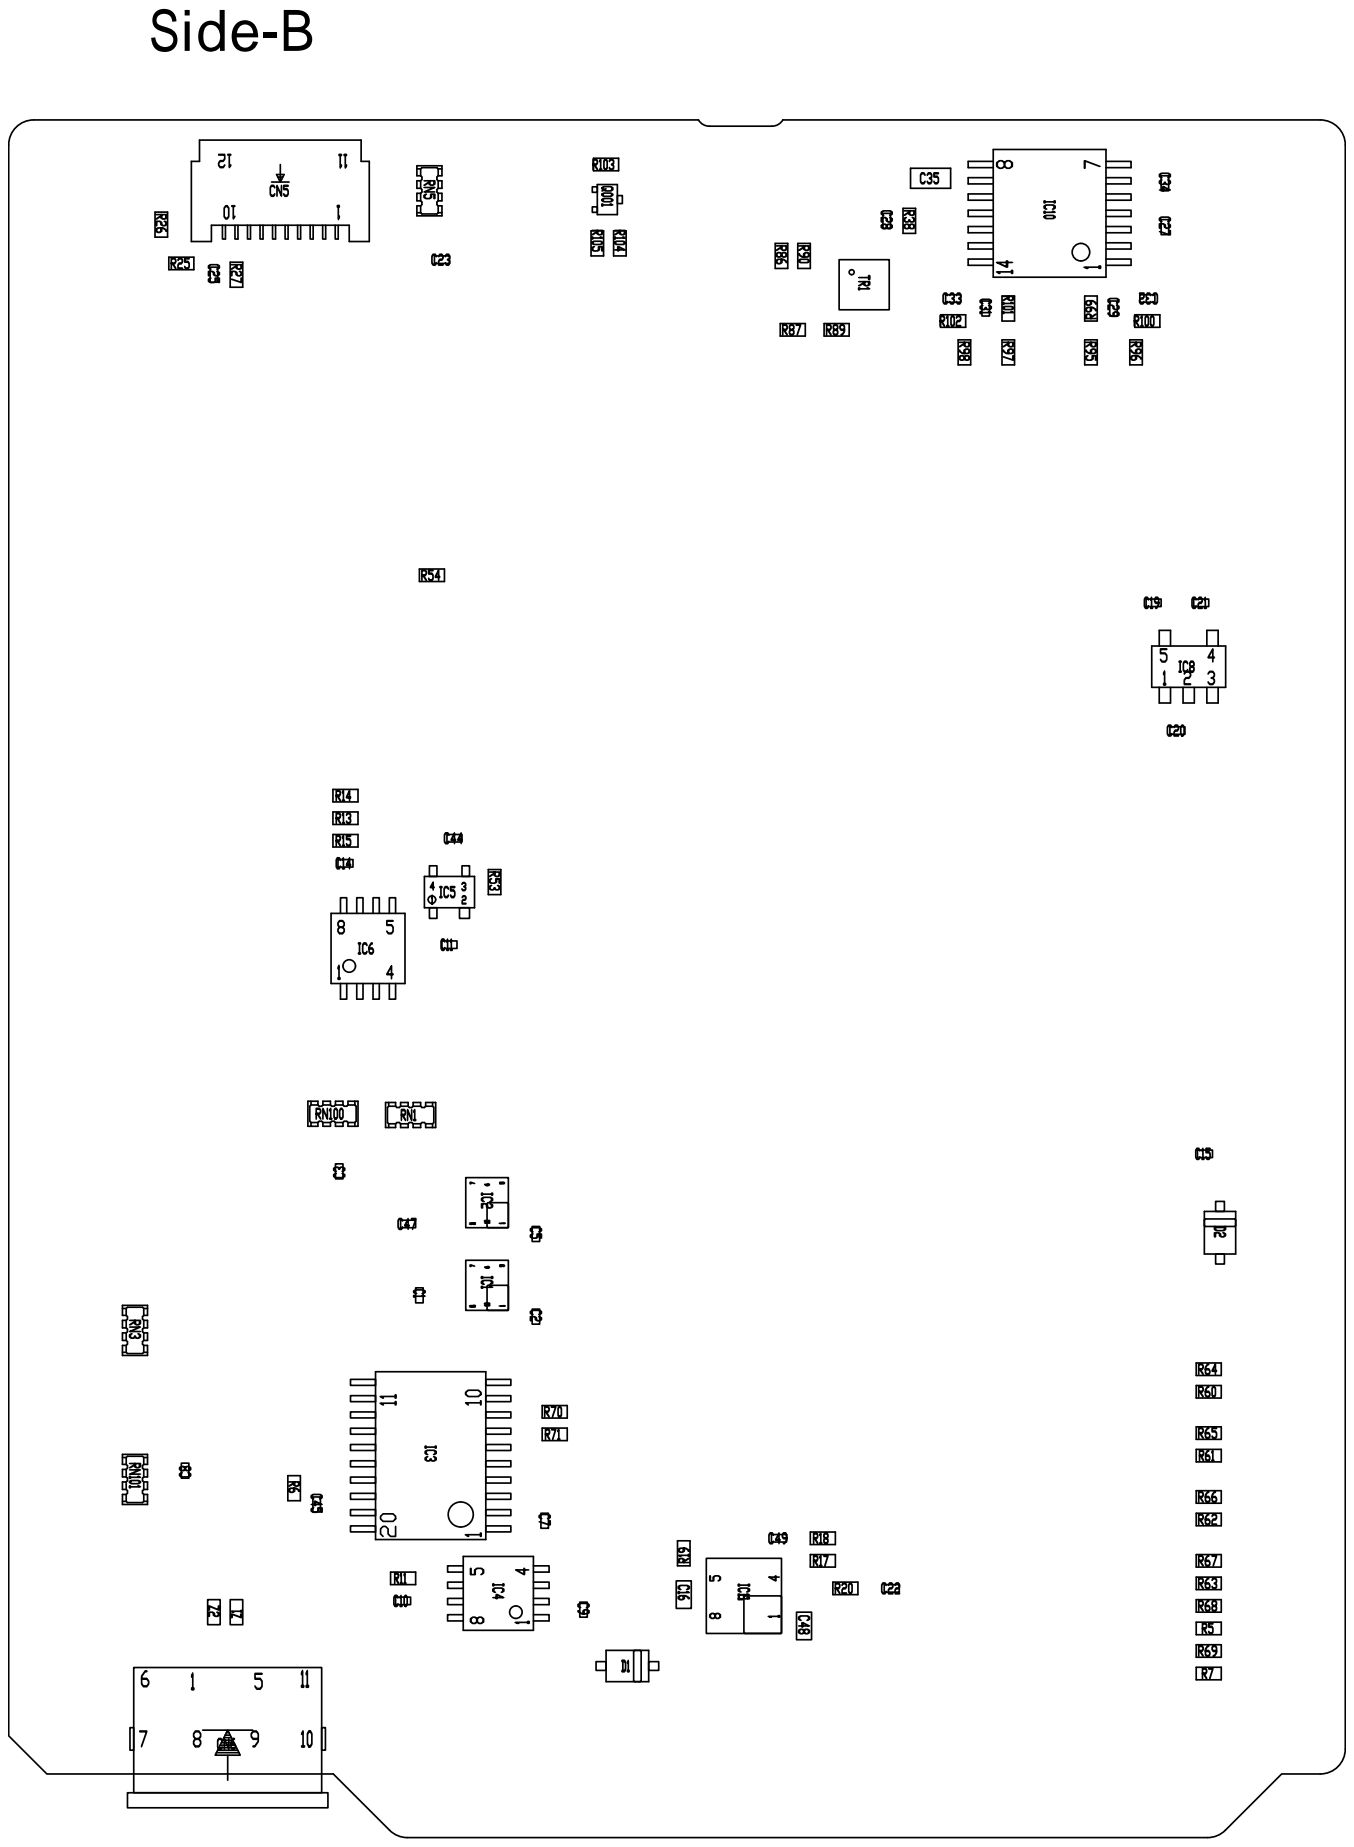
[picture p88: page 2]
