sonydevworld/spresense-hw-design-files/CXD5602PWBLM1/parts_layout/CXD5602PWBLM1_part_layout.pdf

# Side-A

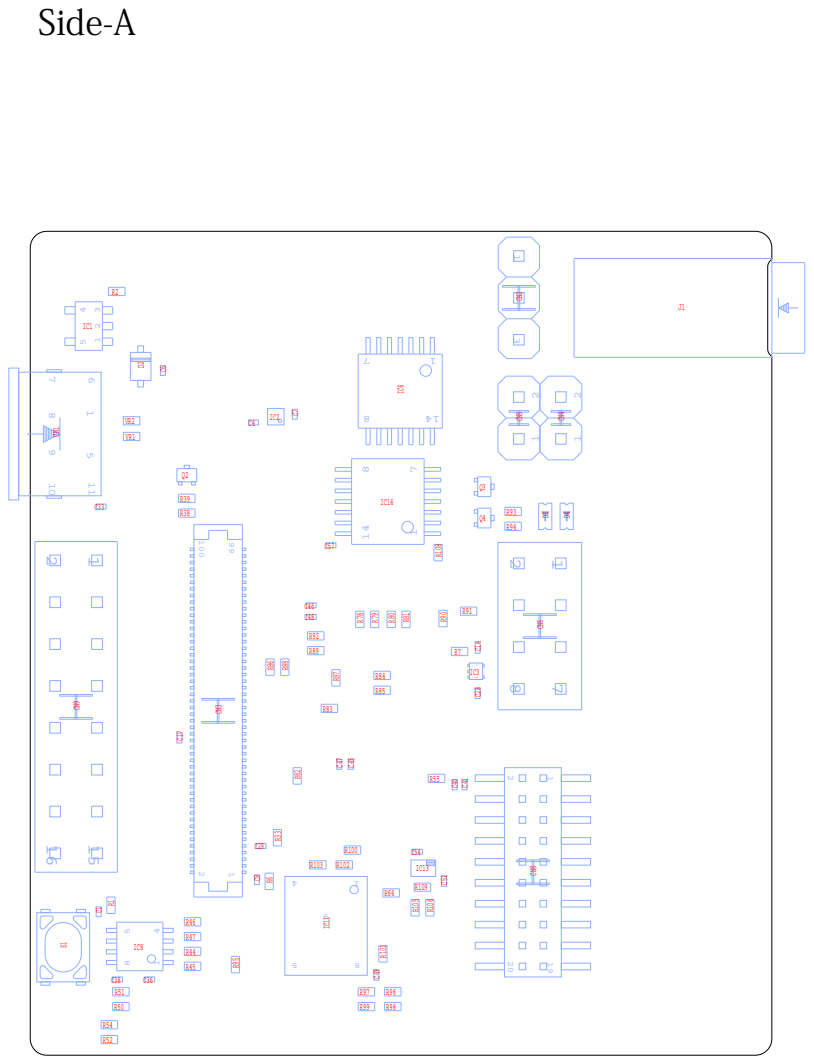
[picture p89: page 1]

# Side-B

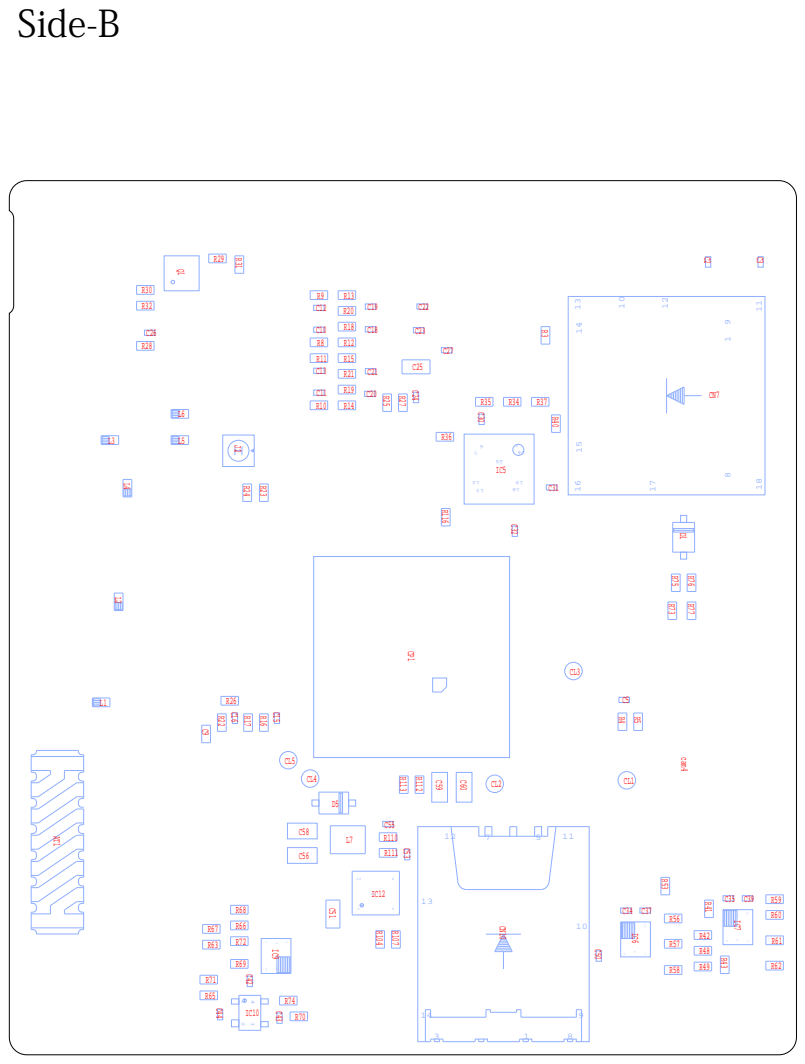
[picture p90: page 2]
