sonydevworld/spresense-hw-design-files/CXD5602PWBMAIN1/parts_layout/CXD5602PWBMAIN1_part_layout.pdf

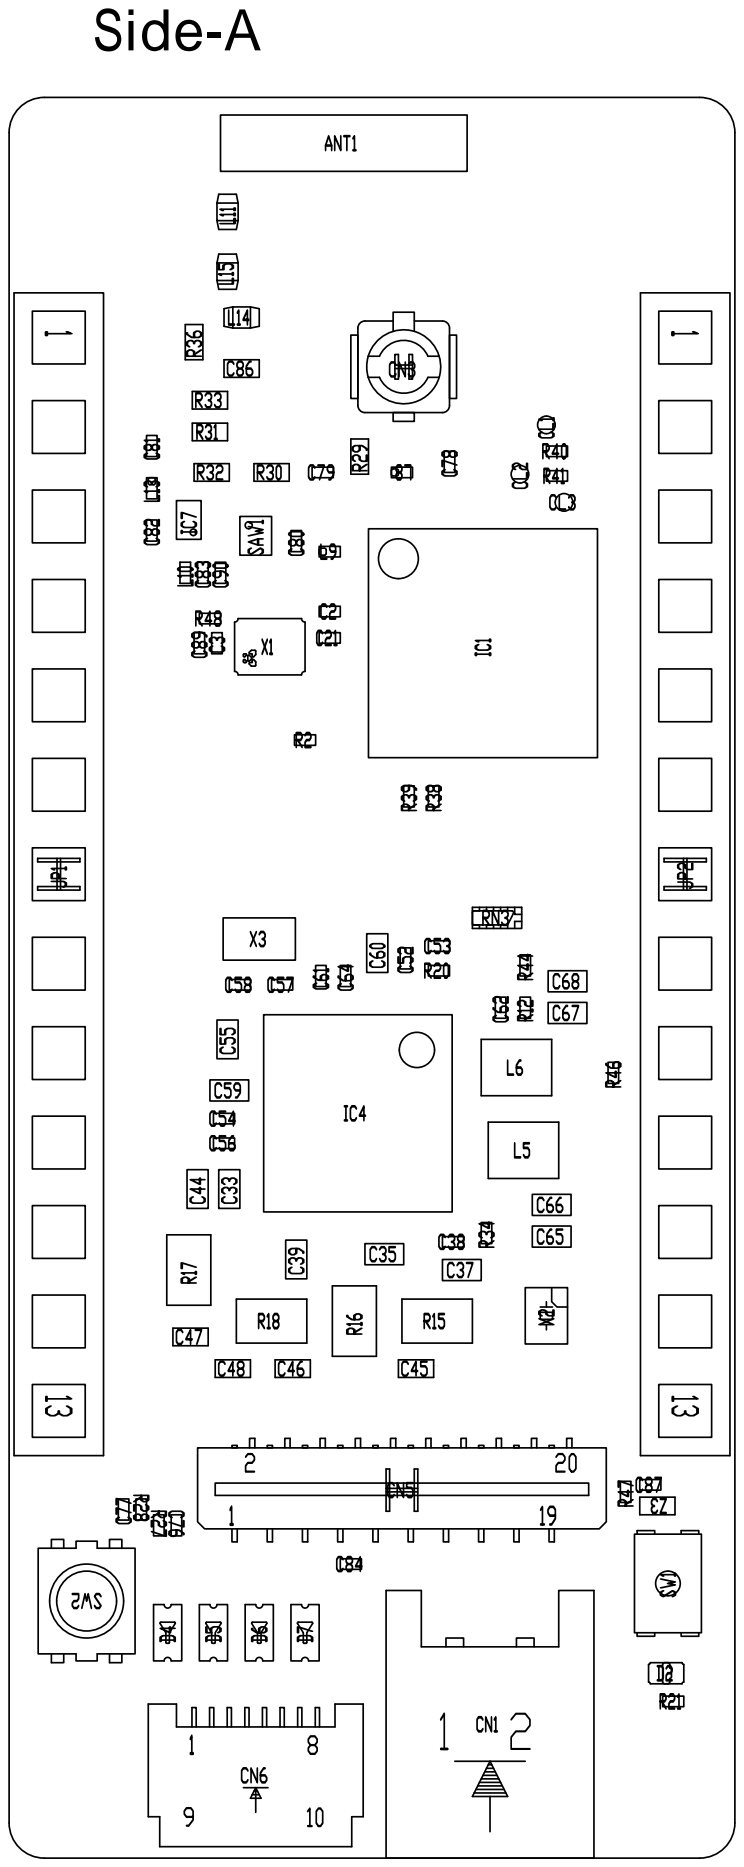
[picture p91: page 1]

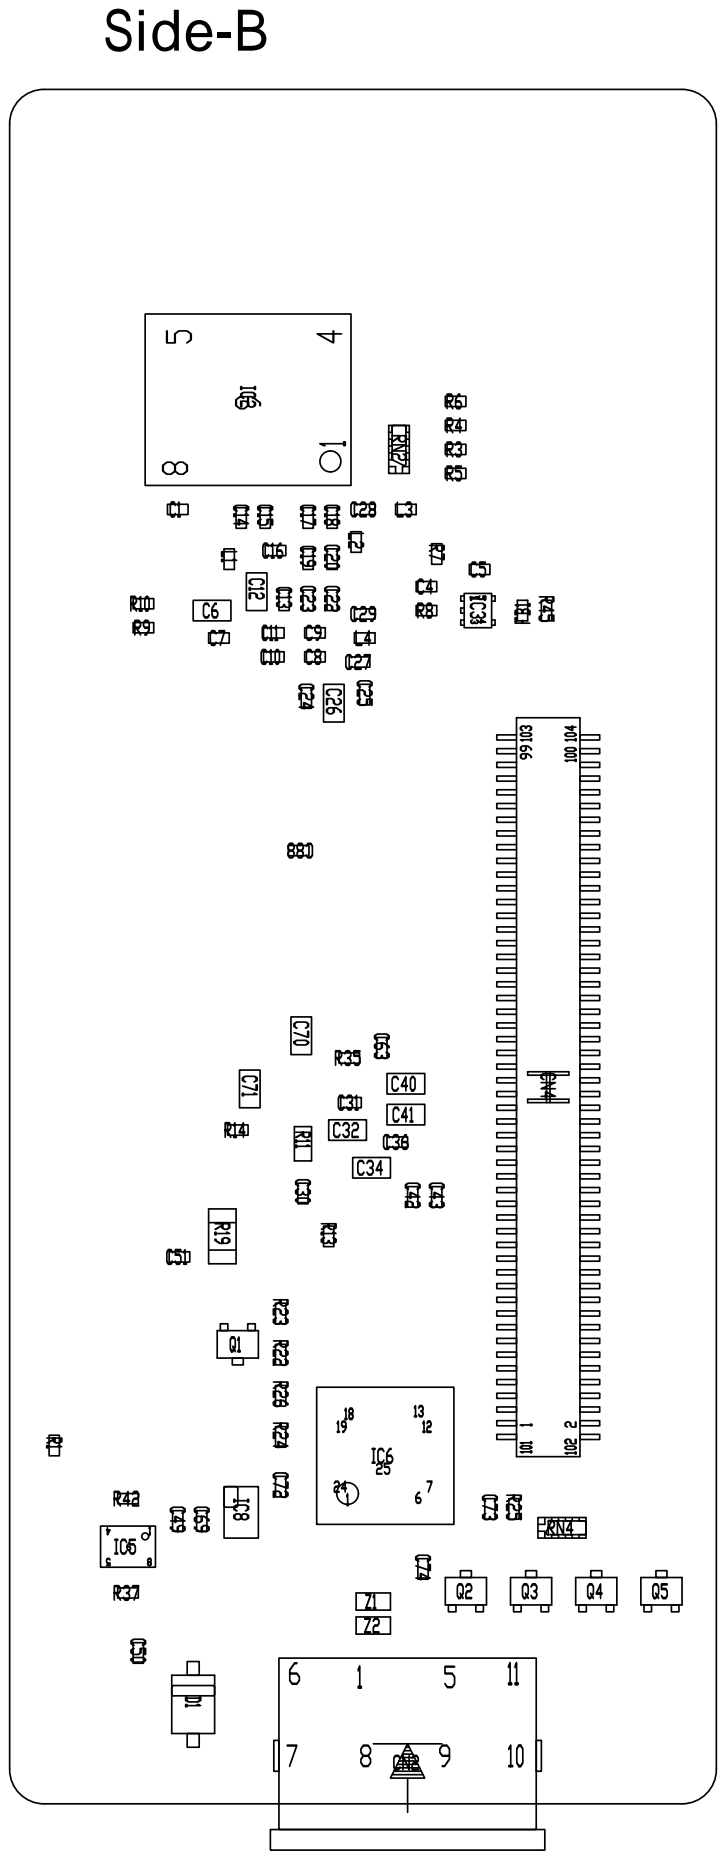
[picture p92: page 2]
