sonydevworld/spresense-hw-design-files/CXD5602PWBLM2/board_dimensions/CXD5602PWBLM2_board_dimensions_ja.pdf

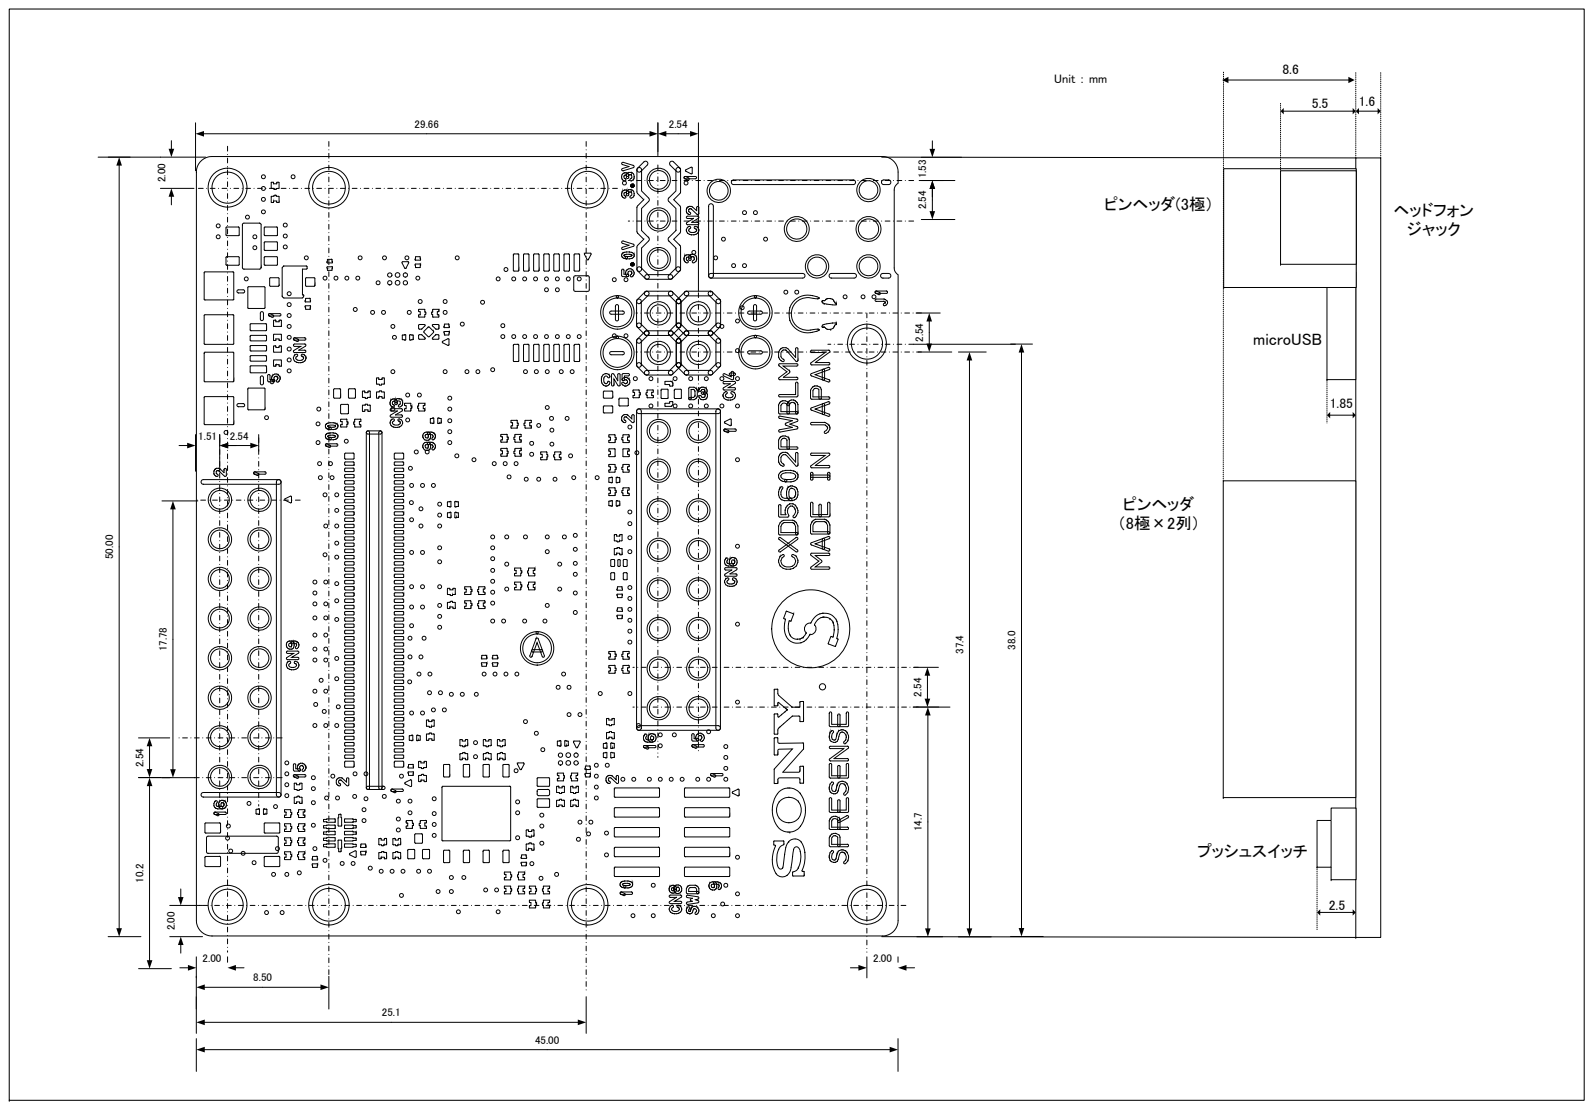
[picture p93: page 1]
ピンヘッダ(3極）; ピンヘッダ （8極×2列）; プッシュスイッチ; microUSB; ヘッドフォン ジャック; Unit ： mm
