sonydevworld/spresense-hw-design-files/CXD5602PWBCAM2/board_dimensions/CXD5602PWBCAM2_board_dimensions.pdf

# CXD5602PWBCAM2 Dimensional drawing

# Unit: mm

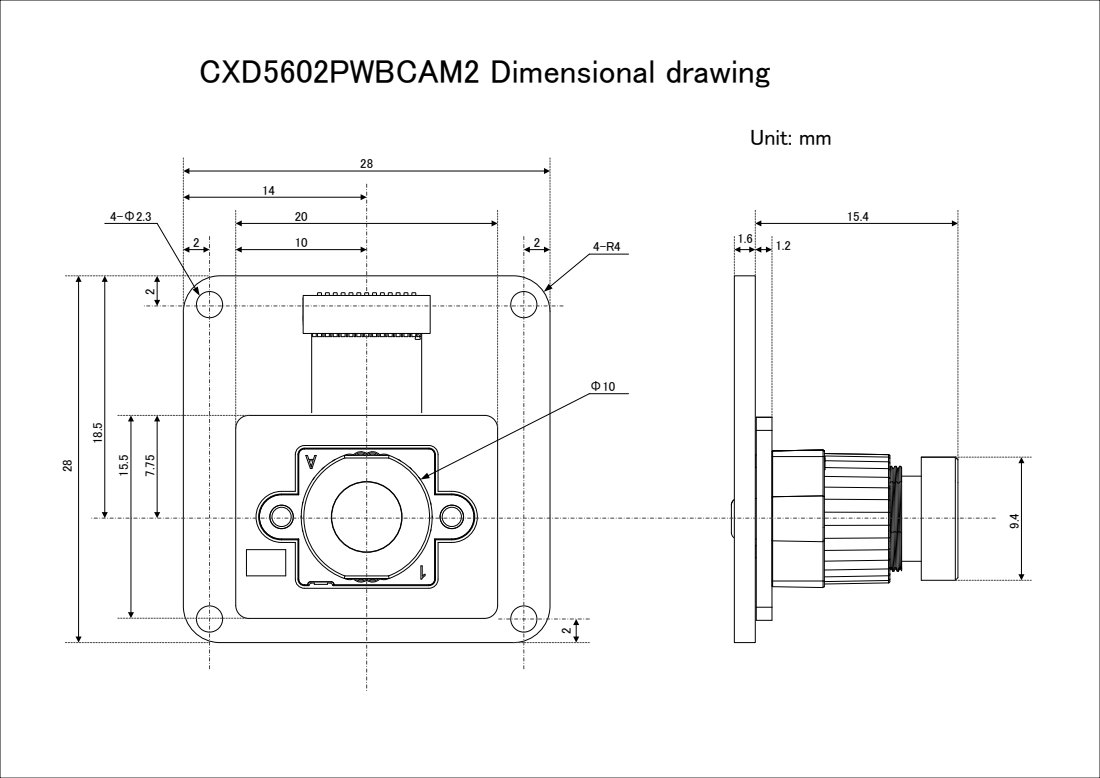
[picture p94: page 1]
