sonydevworld/spresense-hw-design-files/CXD5602PWBLM1/board_dimensions/CXD5602PWBLM1_board_dimensions_ja.pdf

LTE拡張ボード 寸法図 | Unit ： mm

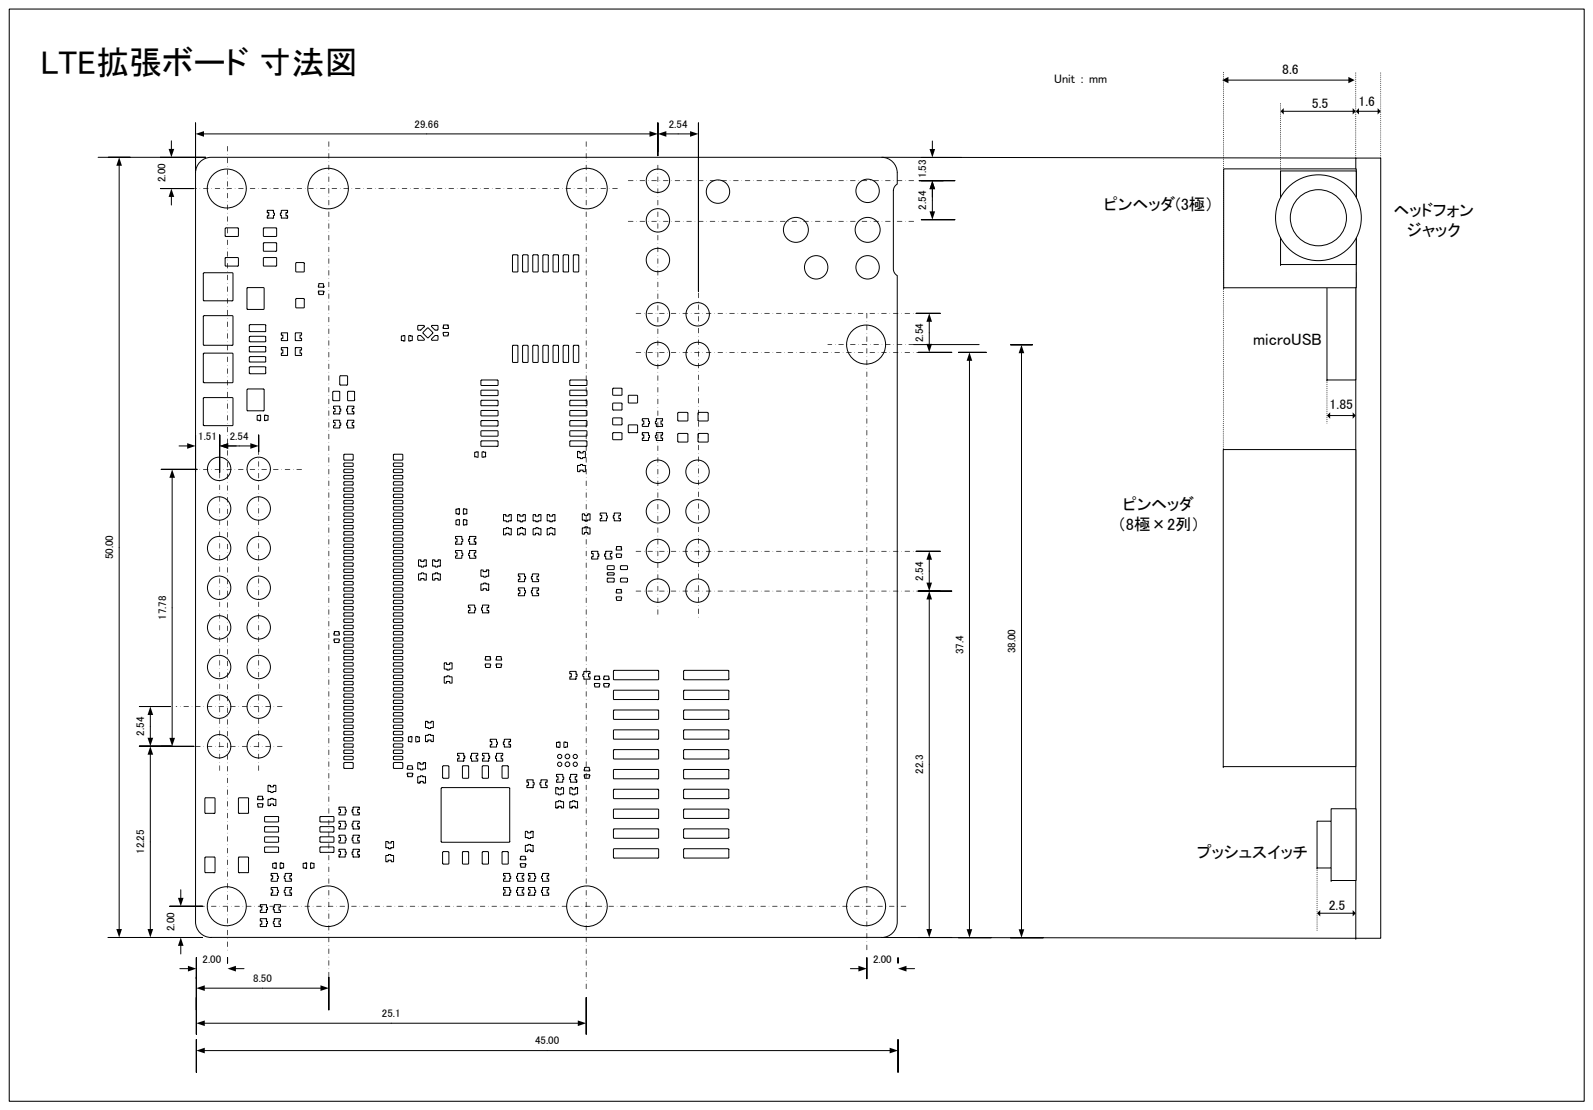
[picture p95: page 1]
ピンヘッダ(3極）; ピンヘッダ （8極×2列）; プッシュスイッチ; microUSB; ヘッドフォン ジャック
